radiolok/dekatronpc/TRS.md

---
title: DekatronPC — Требования v0.10
version: "0.10"
date: 2026-10-07
status: draft
supersedes: rtl/DekatronPC/DekatronPC_TRS_v0_7.md (с черновиком v0.8 golden model) и DekatronPC_TRS_v0_8.md
tags:
  - dekatronpc
  - requirements
  - rtl
  - hardware
  - checklist
---

# DekatronPC — Требования v0.10

## 0. Назначение документа

Документ задаёт функциональные и технические требования к проекту DekatronPC:

- ламповый компьютер на декатронах А110;
- RTL/FPGA-эмулятор (ядро `DekatronPC` + слой `Emulator`);
- модель одного декатрона `DekatronTubeV2` (физический уровень);
- испытательный стенд;
- ламповые модули;
- интерфейс к P&R-инструменту;
- верификацию и план работ.

Документ используется как:

- чек-лист «что готово / что осталось» (разделы 19, 21);
- источник требований для RTL, железа, тестов и P&R;
- основа для дальнейшего планирования (раздел 20).

**v0.9 заменяет v0.8.** Файл лежит в корне репозитория под именем `TRS.md` без номера версии: номер — в заголовке и в истории изменений ниже, прежние редакции — в истории git. Основа документа не переписана с нуля — сохранена структура и ID требований, статусы обновлены по результатам разбора двух функциональных отчётов по текущему RTL (`rtl-functional-report.md`, `emulator-functional-report.md`) и спецификации `DekatronTubeV2` (`Dekatron_Model_TRS_v0_1.md`). Новое помечается по версии, от **[v0.3]** до **[v0.9]**.

---

## 1. История изменений

### v0.10 — у декатрона нет признака достоверности

Признак `Valid` (ИЛИ-10 по главным катодам, лампа `OR10_X7`) удалён из `DekatronModule`, вместе с ним `out_valid` и `settled_q` в `DekatronCounter`. Признак говорил лишь «разряд на каком-то главном катоде», а не «операция закончена». Готовность теперь выводится из известных длительностей: шаг укладывается в один такт `clk`, запись и сброс — в окно реле времени `writeTimer`. Подъём `soft_rst`/`hard_rst` запускает то же окно (состояние `ST_RST`), и `ready` возвращается, только когда линия снята и окно истекло. Экономия — одна лампа ИЛИ-10 на каждую декаду.

`LOOP_DEKATRON_NUM = 2` внесён в `rtl/parameters.sv` (REQ-CNT-002 — Done): владелец подтвердил, что глубины вложенности 0–99 достаточно. Значение `TOP_VALUE` по умолчанию в `DekatronCounter` теперь следует за `D_NUM`, иначе двухдекадный счётчик давал WIDTHTRUNC. Схемы `img/schemes/` перерисованы генератором `tools/schemes/`.

Находка: при нарезке 3/4/3 и `FALL_STEP_HS = 3` разряд падал на главный катод ровно на следующем фронте `clk`, без запаса. Прежний `settled_q` это маскировал, фактически растягивая шаг на два такта. Нарезка по умолчанию изменена на **3/3/4** (`PHASE2_HS = 3`), а проверка окна сваливания стала строгой. `IpLine` на `looptest.bfk` — 656 мкс вместо 784. Отчёт: `doc/dekatron_valid_removal.md`.

Лишние триггеры `DekatronCounter` удалены по решению владельца: `primed_q` (автомат выходит из `rst_n` через `ST_RST`), `tops_q`, старшие разряды `nines_q`/`zeroes_q`. `zero` и `at_top` теперь комбинационно с катодов; защёлкнутые `zero_q`/`at_top_q` остались только при `TOP_LIMIT_MODE` для автоперехода через край. Флаги, маскированные `accept`, — без сброса. Переполнение вложенности (REQ-CNT-007) ловится до шага по `at_top`. По четырём счётчикам 49 → 24 триггера. Отчёт: `doc/dekatron_counter_flop_reduction.md`.

**Бюджет ламп и синтез.** Владелец задал бюджет: не более 1500 ламп на всю машину (REQ-MOD-009). Триггер в библиотеке теперь стоит 7 ламп (3×N16B + 4×J2B, 2 А накала при 6,3 В), инверсный выход у него бесплатный — в liberty добавлен вывод `QN` (REQ-MOD-010). `synt_dpc.tcl` переведён на отображение по площади (`&deepsyn` в ABC) с проверкой эквивалентности `equiv_opt` и проходом `qn_absorb.py`, который переносит инверторы с `Q` на `QN`: IpLine + ApLine + MachineCtrl — 2336,5 лампы против 2636 при прежнем скрипте; из них 910 — триггеры. Приём с терминала идёт по Valid/Ready, данные держит передающая сторона, входной регистр `rx_q` из ApLine удалён, у `DekatronPC` появился выход `rx_rdy` (REQ-UART-008, In Review; ApLine 989 → 874 лампы, три блока — 2242). Отчёт: `doc/tube_count_reduction.md`.

Автомат `ApLine` переписан (REQ-APV2-007): пары OP/WAIT слиты, 9 состояний → 6, стробы `valid` к счётчикам и памяти дешифруются из состояния и поднимаются только при готовности всех исполнителей, поэтому рукопожатие происходит в том же такте. Внешнее поведение не изменилось. ApLine 874 → 719 ламп, три блока — 2087. Отчёт: `doc/tube_count_reduction.md` §10.

Тем же способом переписан автомат `IpLine` (REQ-IPV2-007): пары OP/WAIT слиты, стробы дешифруются из состояния, `ip_dec` и `scan_dec_q` объединены в `dir_q`, `loop_init_q` и `clr_is_loop_q` убраны. Новый `IpLine_tb` с памятью по дисциплине `Ram` нашёл дефект прежнего автомата: инструкция защёлкивалась в такте приёма чтения по устаревшему `rd_valid`, и каждая выборка возвращала опкод предыдущей. Исправлено переписыванием. IpLine 902 → 722 лампы, три блока — 1948. Отчёт: `doc/tube_count_reduction.md` §11.

Третьим переписан `MachineCtrl` (REQ-CTLV2-010): 15 состояний → 10, все выходные стробы (`ip_valid`, `ap_valid`, `tx_vld`, `rx_rdy`, `*_rst_req`, `bell`) дешифруются из состояния, коды операций `ip_op`/`ap_op`/`ap_dec` — прямо из `insn`, который IpLine держит до следующей выборки. Убраны 16 триггеров, в том числе `echo_pending`, `bell_pending`, двухбитный `rst_type` и мёртвое состояние `S_BELL`; машина тратит на инструкцию на такт меньше. Новый `MachineCtrl_tb` (модели IpLine/ApLine/реле/терминала, все 32 опкода, TEST, CIN с эхом, загрузка, сбросы, переполнение, пошаговый режим) подтвердил дефект прежнего автомата из `doc/dpcrun_golden_model.md`: при переполнении вложенности ветка `S_FETCH_W` перебивала останов, машина декодировала скобку и шла дальше (REQ-CTLV2-005). Исправлено: переполнение приоритетнее любого состояния и ловится по фронту. MachineCtrl 512 → 284,5 лампы, триггеров 25 → 9, три блока — 1720,5. Отчёт: `doc/tube_count_reduction.md` §12.

CI `sim` падал: в образе Icarus 12, не знающий `break`/`continue`, которые появились в `IpLine_tb` и `MachineCtrl_tb`. Тестбенчи переписаны без них. Заодно найдены проверки, проходившие без проверки: `DekatronPC_tb.sv` не включал сценарий с программой (`TRY_PROGRAM`), терял символы TX на рукопожатии и завершал сторож через `$error` (код выхода 0); `DekatronPC_tb.cpp` не сравнивал ничего. Исправлено, пошаговое сравнение с golden model работает в CI (REQ-GM-002 — In Review). Отчёт: `doc/ci_sim_check.md`.

Появилась симуляция нетлиста (REQ-VER-025 — In Progress): `rtl/run/synth_sim.sh` синтезирует каждый DUT тем же `synt_dpc.tcl` с параметрами его тестбенча и гоняет те же Icarus-тесты на нетлисте. Модели ячеек `rtl/vtube/vtube_cells.v` приведены к liberty (имена, `NOR10_N16X7`, выход `QN`). Декатрон, `OneShot`/`Impulse`, `RstTimeRelay` и память под `SYNTH` пусты и остаются чёрными ящиками с RTL-моделью в симуляции. `OneShot`/`Impulse` — специальные ламповые схемы, а не логика из ячеек (решение владельца): в счёт ламп ABC они не входят, их надо учитывать в бюджете отдельно, как декатроны. Все тесты проходят, включая DekatronPC (helloworld, program.bfk). Две причины прежнего падения DekatronPC были не в ламповой логике: X из выходного регистра модели памяти (`RamGroup.digit_q` без начального значения; ABC-нетлист не маскирует X, как RTL) и всплеск нулевой длительности на `IsHalted`, который ловил асинхронный `wait` тестбенча. Отчёт: `doc/synth_sim.md`.

Вывод `.` переделан по решению владельца (OPEN-017 закрыт): символ всегда берётся со счётчика данных, мультиплексор `tx_data_bcd = lock ? data_out : rd_data` в ApLine удалён. `MachineCtrl` выдаёт `AP_COUT`, и только по его окончании — `tx_vld`. При снятом MemLock `AP_COUT` загружает ячейку в счётчик (из регистра памяти или после чтения), MemLock не меняется. Цена — одно окно записи на каждый `.`, при 110 бодах незаметно. Hello World через загрузчик теперь печатается верно. ApLine 714 → 679,5 лампы, три блока — 1672,5. Отчёт: `doc/tube_count_reduction.md` §13.

Инструкция декодируется один раз (R3) и хранится только в памяти (R4). Кодом операции ApLine теперь служит сама инструкция `{insn_mode, insn}`, её дешифрирует ApLine; порты `ap_op[3:0]`, `ap_dec` и шифратор в `MachineCtrl` убраны, у IpLine вместо `ip_op[1:0]` один бит `clr` (REQ-APV2-008). Регистр опкода `insn_q` в IpLine удалён: выходной регистр памяти программ меняется только при обращении, а следующее обращение бывает лишь после того, как `MachineCtrl` закончил с текущей инструкцией, поэтому `insn` — это прямо `mem_rd_data`. EOT в память не пишется, о нём сообщает однобитный `insn_eot` (решение владельца). При загрузке опкод пишется в память в такте рукопожатия, `insn_in_ready` поднимается при свободной памяти; состояния `S_FETCH_W` и `S_WRITE` убраны (REQ-IPV2-008). Интерфейс Emulator ↔ DekatronPC (Приложение B) не изменился. IpLine 717,5 → 652, MachineCtrl 282 → 250, ApLine 675,5 → 676 (оба варианта синтезированы в один день одним скриптом), три блока — 1578. Отчёт: `doc/tube_count_reduction.md` §14.

**Новая цель по лампам.** Владелец снизил бюджет всей машины с 1500 до **1200 ламп** (REQ-MOD-009). Три блока, которые сейчас считает синтез (IpLine + ApLine + MachineCtrl со счётчиками), занимают 1578 ламп — на 378 больше нового бюджета ещё до учёта обвязки памяти, реле сброса и пульта. Чистка автоматов исчерпана: оставшиеся идеи из `doc/tube_count_reduction.md` §5 (R5, R11) дают 10–30 ламп. Нужен новый подход (§22, п. 10).

**Реле для тумблеров** (REQ-MOD-011, In Review). Логика, которой управляют только панельные тумблеры, переведена на реле 2CO: ячейка `RELAY_2CO` (0 ламп), модули `RelayMux`/`RelayEn` (`rtl/Logic/Relay.sv`, не расплющиваются синтезом). В `MachineCtrl` — 5 реле (звонок ×3, выбор пуска после сброса ×2); эхо и `SoftRstOnEOT` оставлены на лампах, где реле ничего не экономит. Выигрыш по `MachineCtrl` — около 4,5 ламп в среднем по 7 зёрнам ABC (в пределах разброса одного прогона). Отчёт: `doc/tube_count_reduction.md` §15.

**Упреждающая выборка** (REQ-PERF-003, P3 из `doc/cycle_profile_helloworld.md`, решение владельца). Операция над ApLine не трогает ни IP, ни память программ, поэтому `MachineCtrl` в такте выдачи `ap_valid` выдаёт и `ip_valid`: следующая инструкция читается, пока исполняется текущая. Исключения — скобка (TEST: решение о промотке зависит от его результата) и CIN (ждёт терминал). Выход памяти программ при этом меняется до конца операции, поэтому код инструкции снова защёлкивается — в `MachineCtrl` (`op_q`, 4 триггера), а не в IpLine; ApLine получает `{insn_mode, op_q}` через порт `ap_op`. По окончании операции автомат идёт из `S_WAIT`/`S_COUT` прямо в `S_DECODE`. IP в это время стоит на следующей инструкции; при останове IpLine по входу `ip_ahead` его не сдвигает, а после пуска читает ту же инструкцию заново. helloworld: 5540 → 4184 такта, CPI 13,8 → 10,4; MachineCtrl 248 → 319 ламп. Интерфейс Emulator ↔ DekatronPC не изменился. Отчёт: `doc/prefetch_p3.md`.

**Pi пошагово.** `pi.bfk` прогнан на полном `DekatronPC` в Verilator с пошаговым сравнением (`DekatronPC_tb.cpp -s`, с упреждающей выборкой): 221 386 инструкций, 3,17 млн тактов, ни одного расхождения, вывод `3.141`. Независимый интерпретатор Brainfuck на Python даёт тот же вывод и сходится по счёту инструкций. Первый прогон остановился на 6-й инструкции (`<` из ячейки 0): RTL переходит на 99999, модель — на 29999. В `ApLine` счётчик AP собран без верхнего предела, а `Ram` данных — на 100 000 ячеек (владелец подтвердил, что RTL теперь работает со 100k), поэтому тестбенч собирает модель с `apTop = 99999` (ключ `-a` меняет предел). OPEN-001 не закрыт (REQ-CNT-005, REQ-MEM-DATA-005). Отчёт: `doc/pi_step_check.md`.

Появилась модель декатрона без тактовой базы (REQ-DEK-010 — In Progress): `DekatronTubeDelay` — та же кольцевая модель, но без входа `hsClk`, длительности отрабатываются инерционными задержками `#N` в абсолютном времени (`HS_NS = 100` нс на единицу `*_HS`). Положение разряда входит в запрос перемещения, поэтому два шага подряд в одну сторону не сливаются, а иголки нулевой длительности на подкатодах (нетлист) отфильтровываются. Подключается `` `define DEKATRON_DELAY_MODEL `` в `DekatronModule`, в `DPC.files` не входит (Verilator и Quartus её не видят). `DekatronPC_tb` теперь идёт на настоящих 10 МГц `hsClk` / 1 МГц `Clk` (было 5 МГц / 500 кГц). Все Icarus-тесты, pi.bfk на RTL и на нетлисте проходят; новые задания CI `sim_delay` и `synth_sim_delay`. Затем тем же define на задержки переведены `Impulse`, `OneShot`, `DekatronPhaseGen` и проверки `DekatronPulseSender` (новых модулей нет, логику выбирает `` `ifdef ``): `DekatronCounter` больше не использует `hs_clk`, тесты Counter/Dekatron идут с `hsClk` в нуле. У `OneShot` вход окна проходит инерционный фильтр 1 пс, чтобы иголки нулевой длительности не запускали окно. Затем так же переведено `RstTimeRelay`: весь DekatronPC работает без `hsClk`. Найдена гонка в `DekatronPC_tb`: кнопки пульта выставлялись блокирующим присваиванием сразу после `@(posedge Clk)`, и автомат видел их в том же такте или в следующем в зависимости от порядка событий (отсюда расхождение RTL и нетлиста на один такт). Кнопки и тумблеры теперь неблокирующие, обе модели и нетлист дают одинаковые числа тактов. Отчёт: `doc/dekatron_delay_model.md`.

**Один флаг MemLock** (REQ-APV2-003, решение владельца). Признак `dirty` удалён из `ApLine` и из `dpcrun`: он отличался от `lock` только после `STORE`. Правило теперь одно: без MemLock данные сначала загружаются, при MemLock шаг адреса и `CLRML` сначала выгружают счётчик, и выгрузка снимает MemLock. Попутно закрыт дефект v0.9 — MemLock больше не переживает шаг адреса после `STORE` (REQ-ML-005). Цена — повторная запись того же значения после `STORE`; на `pi.bfk` и `helloworld` счёт обращений не изменился. Отчёт: `doc/memlock_single_flag.md`.

**Требования к P&R по ревью webui** (2026-10-09, `doc/webui_review.md` на ветке `webui`, PR #28). Владелец ответил на Q1–Q11, решения внесены в §17 как REQ-PR-011…019. Нетлист остаётся иерархическим; блок P&R — это ящик из 3–5 корзин. Блок трассируется вместе с разъёмами HD-68 на другие блоки, а весь компьютер можно разводить в одном проекте. На плате корзины только питание, сигналы идут проводами. Ферритовая память — вне P&R. Для RTL добавлена задача: структуры из проводов по разъёмам блока (REQ-PR-019, §22).

### v0.9 — конфигурация счётчиков зафиксирована по реальным программам

Разрядность счётчиков до сих пор выбиралась по оценке. Теперь она проверена на наборе **Brainfuck-100**: сто программ с GitHub (классика, математика, текстовые утилиты, алгоритмы, интерпретаторы и компиляторы, квайны, игры, нагрузочные тесты), прогнанных в интерпретаторе с 8-битными ячейками. Для каждой сняты длина программы, занятая лента, число исполненных инструкций, число шагов промотки и **реальный максимум счётчика вложенности при промотке**.

**Зафиксирована конфигурация 5 + 2 + 5 + 3 = 15 декатронов.**

| Счётчик | Декатронов | Диапазон | Покрытие набора | Решение |
|---|---:|---|---|---|
| IP | 5 | 0–99999 | 99 из 100 (при 4 — 88, при 3 — 61) | оставлен |
| Loop | **2** | **0–99** | 100 из 100, максимум 67 | **сокращён с 3** |
| AP | 5 | 0–29999 / 0–99999 | 98 / 100 | предел остаётся открытым (OPEN-001) |
| Data | 3 | 0–255 | 100 из 100 | оставлен |

**Почему хватает двух декатронов вложенности.** Счётчик считает вложенность от скобки, с которой началась промотка, а не от начала программы. Статическая глубина в тексте завышает потребность: у `password-vault.bf` она 124, а при исполнении счётчик доходит до 52; у `Kiloseconds.b` — 90 против 67. Из 273 просмотренных программ не помещается только `OptimTease.b` — тест на прочность оптимизаторов с вложенностью 258. Переполнение по-прежнему безопасно: инкремент со 99 не выдаётся, промотка прерывается и машина останавливается (REQ-CNT-007). Экономия — одна декада без схемы чтения (`LOOP_READ = 0`), около 10 ламп.

**Попутная находка — цена промотки.** На одну исполненную инструкцию в среднем приходится 1,7 шага промотки IP; у `pi.bfk` 313 968 шагов промотки против 198 594 инструкций. Время выборки во время промотки влияет на быстродействие машины не меньше, чем время исполнения. Внесено как REQ-PERF-001.

Новый раздел 4.4 фиксирует текущие ограничения архитектуры и десять программ, которые их определяют.

**Сведение с веткой `claude_nextGen` (04.10.2026).** Существовали две параллельные редакции v0.8: в репозитории — черновик про golden model, вне репозитория — синтезируемость памяти и ассерты. Обе вошли в v0.8 ниже. Состояние RTL ветки на момент сведения:

- `LOOP_DEKATRON_NUM` в `rtl/parameters.sv` пока равен 3: решение REQ-CNT-002 принято, в коде не внесено.
- Ширины счётчиков задаются глобально в `rtl/parameters.sv`, а не параметрами `IpLine`/`ApLine`.
- Признак достоверности декатрона при синтезе (`SYNTH`) — явный экземпляр лампы ИЛИ-10 `OR10_X7` из `rtl/vtube/vtube_cells.lib`: abc не собирает такой широкий элемент из reduction-OR. В моделировании — `|MainOneHot`. Модуль `OneHotValid` из дерева удалён; запись — снова `BcdToBinEn`.
- При синтезе Yosys банковое дерево `Ram` заменяется заглушкой с тем же интерфейсом: рекурсивный `RamGroup` зацикливает `hierarchy -check`. Число ламп по синтезу (≈ 2600) — без памяти.
- В ветку не внесены две подготовленные правки: сброс `lock` в `ApLine` при шаге адреса без выгрузки (после STORE) и вывод через `AP_COUT` в `MachineCtrl` (OPEN-017).
- Операнды не защёлкиваются ни в `DekatronCounter`, ни в `ApLine`: мастер держит их до `ready`.

---

### v0.8 — синтезируемость памяти, параметр размера банка, управление ассертами

Версия написана по итогам первых прогонов в симуляторе и попытки синтеза. Все изменения — следствия того, что показали инструменты, а не пересмотр замысла.

**Память перестала быть несинтезируемой.**

Попытка синтеза подтвердила опасение, зафиксированное в `OPEN-015`, но причин оказалось две, а не одна.

Первая — дробление. Банк 10×10 при ширине четыре бита занимает 400 бит, а блок памяти ПЛИС вмещает 10 240: пропадает 96% каждого блока. На две памяти требовалось около 1300 блоков там, где по объёму достаточно 80.

Вторая, не менее важная и не замеченная ранее, — **асинхронное чтение в банке**. Блоки памяти ПЛИС умеют только синхронное чтение; при асинхронном массив раскладывается в триггеры, а это 700 000 штук при бюджете порядка 40 000 логических элементов. Одно увеличение банка проблему бы не решило.

Исправлено обоими способами сразу:

| | Банков | Блоков памяти |
|---|---:|---:|
| Программ 100k×4, банк 10×10 | 1000 | 1000 |
| Программ 100k×4, банк 100×100 | 10 | 50 |
| Данных 30k×10, банк 10×10 | 300 | 300 |
| Данных 30k×10, банк 100×100 | **3** | **30** |

**Размер банка стал параметром, а не выбором.** `BANK_DIGITS` = 2 даёт матрицу 10×10 для физической машины и P&R, 4 — матрицу 100×100 для ПЛИС. Рекурсия та же, меняется лишь уровень её остановки. Вторая, плоская реализация памяти, которую требовал `REQ-MEMV2-006`, оказалась не нужна: одна и та же память служит обеим целям. Требование снято, `OPEN-015` закрыт.

**Третье, найденное попутно:** без ограничения по реально используемому объёму память данных разворачивалась на все 100 000 ячеек адресного пространства при используемых 30 000. Введён параметр `CELLS`, банки выше границы не создаются.

**Цена.** Синхронное чтение добавляет такт: обращение занимает два такта вместо одного. На программе вычисления Pi это около 99 тысяч дополнительных тактов. Избежать нельзя — асинхронной памяти нужного объёма в ПЛИС нет.

**Внутри банка появилась адресная арифметика** — тетрады сводятся в линейный индекс. Это не возврат к тому, от чего избавлялись: пересчёт не выходит за пределы одного банка и существует только в поведенческой модели и реализации для ПЛИС. В железе тетрады идут прямо на дешифраторы строк и столбцов матрицы.

**Golden model на полный ISA** (черновик v0.8 из репозитория). C++ golden model (`bfutils/dpcrun`) переписана: оба ISA, MemLock с ленивым чтением, SOT/EOT, сбросы, переполнение счётчика циклов, ПЗУ загрузчика. По решению владельца проекта модель повторяет RTL как есть, в том числе там, где RTL расходится с TRS (CLRI и MemLock, снятие MemLock после STORE). 53 модульных теста в CI репозитория bfutils. Сверка вскрыла дефект: `.` не выдаёт `AP_COUT`, поэтому OPEN-017 открыт снова. Подробности и остальные находки — `doc/dpcrun_golden_model.md`.

**Управление ассертами переведено на условную компиляцию.**

Параметр `EN_ASSERTIONS` заменён на `` `ifdef ASSERTIONS ``. Параметр требовал протаскивания через всю иерархию инстанцирований и молча оставался включённым там, где его забыли передать. Проверки конфигурации на этапе элаборации (`initial` с контролем параметров) остаются под `` `ifndef SYNTH ``: их следует получать при каждой сборке, а не только при включённых ассертах.

---

### v0.7 — ленивое чтение, отказ от APB, регистровый выход памяти

Три связанных решения, принятых по итогам измерений на реальных программах.

**Ленивое чтение вместо упреждающего.**

В v0.6 `ApLine` читал ячейку сразу после каждой смены адреса. Замер показал, что это дорого: перемещения указателя составляют половину инструкций типичной программы, а каждое из них вызывало обращение к памяти, даже когда следующая инструкция — снова перемещение.

Теперь ячейка читается только тогда, когда её значение действительно нужно. Замер на программе вычисления числа Pi (`pi.bfk`, 198 594 инструкции, `<` и `>` — 51% кода):

| Схема | Обращений к памяти | Изменение |
|---|---:|---|
| Упреждающее чтение | 155 625 | — |
| Ленивое чтение | 99 077 | **−36%** |

На последовательности `>>>>>...<<<<<` разница сорокакратная: одно обращение против сорока одного. Закрывает `OPEN-016` с цифрами.

**Регистровый выход памяти вместо копии ячейки в ApLine.**

Первая редакция ленивого чтения требовала в `ApLine` собственную копию ячейки — десять триггеров, а лампового триггера дороже элемента в библиотеке нет. Оказалось, что регистр не нужно добавлять: он и так существует физически. У ферритовой памяти чтение разрушающее, считанное значение оседает в усилителях считывания и держится там на время восстановительной записи.

Поэтому регистр перенесён в память: `rd_data` хранит значение последней затронутой ячейки до следующего обращения, запись сквозная. В `ApLine` состояния осталось три бита — `lock`, `dirty`, `mem_here`. Показатели при этом соответствуют варианту с полной копией, а не урезанному.

**Отказ от APB.**

APB был выбран в v0.6 и оказался неподходящим по двум причинам. Во-первых, он гарантирует валидность данных только в такте `PREADY`, а требуется обратное — чтобы значение держалось до следующего чтения; полагаться на негарантированное поведение нельзя. Во-вторых, две обязательные фазы дают минимум два такта на обращение там, где достаточно одного.

Память переведена на тот же Valid/Ready, что и остальной тракт. Заодно исчез разнобой протоколов: раньше `ApLine` и `IpLine` были мастерами двух разных дисциплин сразу.

Наложение ПЗУ загрузчика перестало быть отдельным мультиплексором: `Ram` получил входы `ovl_hit`/`ovl_data`, поэтому автомат обращений и выходной регистр остались в единственном экземпляре.

**Цена решения.**

Проверка скобки перестала быть бесплатной: признак нуля при ленивом чтении не всегда под рукой, и перед `[` или `]` верхний автомат просит `ApLine` обеспечить его достоверность операцией `TEST`. Обращение к памяти при этом происходит, только если значение не прочитано, а во время самой промотки тела цикла проверка не повторяется. В Debug ISA скобки проверяют счётчик адреса, достоверный всегда, поэтому там `TEST` не выдаётся.

**Найденный дефект: комбинационная петля в `DekatronCounter`.** Обнаружен прогоном в симуляторе. Сигнал `ready` содержал условие `~writing`, а окно записи запускается от `accept`, который сам зависит от `ready`:

```
ready -> accept -> write_req -> Impulse -> OneShot -> writing -> ready
```

Петля замыкалась при любой операции записи, включая автопереходы через верхний предел. Icarus зацикливался на одном такте, Verilator выдавал `UNOPTFLAT`, синтез был бы некорректен. Следствие: `set`, `set_zero` и переходы `255+1`/`0−1` были неработоспособны, при том что инкремент, декремент и оба сброса работали.

Условие оказалось избыточным: автомат покидает `ST_IDLE` при приёме операции записи и возвращается только по окончании окна, поэтому состояние уже несёт нужную информацию. Петля разорвана удалением `~writing`.

**Второе замечание симулятора: UNOPTFLAT на цепочке переноса.** Поразрядная запись рипла

```systemverilog
assign step_f_chain[d] = step_f_chain[d-1] & nines_q[d-1];
```

заставляет Verilator видеть зависимость вектора от самого себя: анализ ведётся с точностью до целого сигнала, а не отдельных битов. Физически петли нет — перенос идёт строго от младшей декады к старшей.

Устранено структурно: рипл вынесен в локальные переменные внутри `always_comb`, а векторы `step_*_chain` только записываются и нигде не читаются. Подавление предупреждения не выбрано намеренно: оно скрыло бы и настоящие петли, если они появятся в этом же файле. Эквивалентность старой и новой цепочки проверена на 8000 случайных векторов.

**Этот дефект принципиально не мог быть найден на модели.** Такт-в-такт копия на Python вычисляет сигналы в порядке присваивания и нуль-задержечную петлю не видит вовсе: у неё нет понятия сходимости комбинационной логики. Это ровно тот класс ошибок, ради которого в документе стоит `REQ-VER-029`, и первое подтверждение, что «проверено на модели» и «проверено в симуляторе» — разные вещи.

**Найденный дефект.** `MachineCtrl` не видел сброса, пришедшего с пульта: реагировал только на сброс, запрошенный им самим по инструкции HRST или SRST. Реле срабатывало, счётчики сбрасывались, а автомат продолжал исполнять инструкцию и не менял набор команд — после аппаратного сброса машина осталась бы в Brainfuck ISA вместо Debug, и загрузчик бы не стартовал. Добавлены входы `soft_rst`/`hard_rst`, реакция общая для обоих источников.

---

### v0.6 — Шаг 1в выполнен: весь тракт переведён на Valid/Ready

Переписаны память, обе линии и верхний автомат. Фаза 1 плана работ закрыта полностью.

**Память переведена на банковую организацию и APB.** *(решение об APB отменено в v0.7, банковая организация сохранена)*

Единый массив с преобразованием BCD-адреса в двоичный заменён иерархией: банк 10×10 (2 декатрона) → группа из 10 банков (3 декатрона) → и так далее до пяти. Адресной арифметики нет вовсе — тетрада напрямую выбирает потомка сравнением. Это закрывает `REQ-MEM-IP-003/004`, `REQ-MEM-DATA-003/004` и снимает `REQ-REF-010`: умножители на 10/100/1000/10000 не появляются, потому что линейный индекс не вычисляется.

Ширина ячейки данных зафиксирована: **10 бит `{hundreds[1:0], tens[3:0], ones[3:0]}`** — закрывает расхождение `REQ-MEM-DATA-002`.

Загрузчик в памяти программ занимает ровно один банк 10×10 (100 инструкций по адресам 99900–99999). Прежний мультиплексор по `isBootloader` не нужен.

**ApLine: предвыборка текущей ячейки.** *(заменена ленивым чтением в v0.7)*

Прежний код считал `DataZero` как `~(|RamDataOut)` и выдавал `tx_data_bcd` прямо с выхода памяти — это работало только потому, что память моделировалась асинхронной. Ферритовая память так не умеет: чтение разрушающее, а по APB `rd_data` валиден лишь в такте `p_ready`. Поэтому `ApLine` держит копию текущей ячейки и обновляет её после каждой смены адреса. Побочный выигрыш: `LOAD`, `COUT`, `[`, `]` вообще не обращаются к памяти.

Замерено на модели: серия `+++++` после первой загрузки не трогает память ни разу, а `+++>+++` даёт ровно три обращения (предвыборка, выгрузка, предвыборка) — то, чего добивался §7.5.

**IpLine: промотка циклов целиком внутри блока.**

Прежде решение о перемотке принимал декодер и повторно поднимал `IpRequest`, а шаг IP выдавался из трёх мест. Теперь `IpLine` получает признак `loop_val_zero` и мотает сам; разбор скобки вынесен в отдельное состояние. Подключены `CLRI` и `CLRL`.

**MachineCtrl: логика циклов из декодера удалена.**

Декодер сводится к таблице диспетчеризации по паре `{insn_mode, insn}`. Сверено построчно с §6: все 32 комбинации покрыты. Подключены отсутствовавшие ранее `BELL`, `CLRL`, `CLRI`, `HRST`, `SRST`, `CLRD`, `CLRML`, `LOAD`, `STORE`.

Асинхронные входы `Rst_n`/`HardRst_n` из тракта убраны: сброс декатронов — физический импульс по катоду, длительность держит внешнее реле времени. Машина выдаёт запрос и ждёт снятия `rst_busy`.

**Найденные и устранённые дефекты:**

- **`CLRD` обязан выставлять `MemLock`.** Допущение v0.5 («не трогает, по аналогии с LOAD/STORE») проверено и оказалось неверным: при нём `[-]` не обнуляет ячейку — ноль ложится в счётчик, счётчик считается устаревшим, и при смене адреса из памяти возвращается прежнее значение. Закрывает `OPEN-002` против прежнего допущения.
- **Зависание при переполнении вложенности.** Счётчик циклов перескакивал 999→0, флаг ошибки поднимался, но промотка продолжалась: парная скобка уже не найдётся, IP уходит за пределы памяти, машина висит. Теперь промотка прерывается, машина останавливается.
- **Дублирующийся `InsnLoopDetector`** в `IpLine` — два инстанса, подключённые к одному и тому же регистру.
- **Запись в область загрузчика** прежде уходила в RAM, а читался всегда ROM: ячейка становилась недостижимой. Теперь блокируется и поднимает `p_slverr`.

**Замечание о методе проверки.** Первая модель `IpLine` работала с символами вместо опкодов и потому не отражала интерфейс RTL — именно она скрывала зависание при переполнении. После переписывания модели на опкоды дефект проявился сразу. Модели, не совпадающие с интерфейсом проверяемого блока, дают ложную уверенность.

---

### v0.5 — реализована подсистема декатрона, Шаги 1а и 1б Фазы 1 закрыты

Написан и проверен RTL нижних уровней. Шаги 1а и 1б плана работ выполнены, Шаг 1в (распространение Valid/Ready на `IpLine`/`ApLine`) остаётся открытым.

**Модель декатрона переработана на кольцевой регистр — отказ от FSM-модели TRS v0.1.**

Вместо FSM из четырёх состояний состояние прибора описывается 30-битным регистром в кольцевом режиме: ровно один установленный бит — текущее положение разряда, перемещение — циклический сдвиг. Соседние электроды вычислять не требуется, они соседние по построению. Кодировка: индекс `% 3 == 0` — главный катод (цифра = индекс/3), `% 3 == 1` — первый подкатод, `% 3 == 2` — второй.

Ключевое физическое уточнение, давшее эту переработку: **на подкатоде разряд остаться не может** — при снятии сигнала он сваливается на соседний главный катод (с первого подкатода назад, со второго вперёд). Отсюда напрямую следуют все случаи, которые в FSM-модели описывались отдельными таймерами:

- только первая фаза и снятие → возврат на исходный катод;
- вторая фаза пришла поздно → разряд уже свалился, шага нет;
- частичного инкремента не существует в принципе.

**Поэтому параметры `PHASE_WINDOW_HS` и `RETURN_TIMEOUT_HS` из TRS v0.1 упразднены** — их роль выполняет `FALL_STEP_HS`. Регистры `prev_digit_q`, `target_digit_q` и явная FSM из модели декатрона исчезли полностью.

**Формирователь импульсов: нарезка такта на трети.**

Первая версия делила такт на полуволны (первая фаза — положительная, вторая — отрицательная). Проверка на модели показала, что так счёт не идёт вовсе: к концу такта разряд остаётся на втором подкатоде, а первая фаза следующего такта утаскивает его обратно — разряд бесконечно колеблется между подкатодами и ни разу не попадает на главный катод. Потребовалась бы пауза длиной в целый такт, то есть счёт через такт (500 кГц).

Такт разделён на три части: первый подкатод, второй подкатод, пауза на сваливание. Пауза внутри такта даёт **счёт каждый такт — 1 МГц вместо 500 кГц**. Времязадающая часть вынесена в `DekatronPhaseGen` и моделирует RC-цепи реальной схемы; сам `DekatronPulseSender` стал чистой комбинаторикой (4 И, 2 ИЛИ).

**Найдены и устранены дефекты, которых не было видно в спецификации:**

- Операции записи/сброса «встык», без снятия воздействия между ними (например, импульс сброса в 0 сразу после сброса в 9), не срабатывали: признак завершения сбрасывался только при снятии всех воздействий. Физически импульс на другом катоде — это новая операция. Добавлено отслеживание цели: смена цели без снятия воздействия перезапускает отсчёт.
- Сочетание `GUIDE_STEP_HS=3, FALL_STEP_HS=4` при нарезке 3/4/3 срывает счёт наглухо: окно сваливания не вмещает падение, показание никогда не становится достоверным. Добавлены проверки согласованности таймингов на этапе компиляции.

**Сбросы стали физическими линиями счётчика.**

Промежуточно рассматривался вариант «аппаратный сброс как операция по handshake», но принято другое решение: `soft_rst` и `hard_rst` — прямые линии на уровне счётчика, который разводит их по катодным линиям декад, поскольку только он знает целевые позиции. Длительность обеспечивает **внешнее физическое реле времени**; растяжки внутри счётчика нет — это была бы лишняя логика поверх уже существующей физической цепи.

**Появился сигнал достоверности показания.**

Пока разряд идёт по подкатодам, ни один главный катод не светится и позиционный код нулевой — что неотличимо от настоящего нуля. Прежде это маскировалось выдачей `X` (`OutPos = ... ? 10'bx : _OutPos`), что работало только в симуляции. Теперь есть `Valid` — физически ИЛИ по десяти линиям чтения, реализуемо в железе.

**Подтверждено на модели:** 12 инкрементов подряд без снятия `ready` (одна операция за такт), перенос через все декады, оба режима верхнего предела (255+1→0 и 0−1→255), `hard_rst` → 99900 на пяти декадах.

---

### v0.4 — принципиальное уточнение физики декатрона и порядка работ

Зафиксировано explicit-решение по OPEN-008 (было открыто в v0.3): **последовательная миграция, а не параллельное ведение моделей.** Порядок: сначала `DekatronTubeV2` (физическая модель, полностью без handshake) реализуется и покрывается полным набором тестов из TRS v0.1 — только после этого RTL верхних уровней (`DekatronCounterV2` и выше) переписывается вокруг неё под Valid/Ready. Это меняет структуру Фазы 1 плана работ (раздел 20) — переход на Valid/Ready для `IpLine`/`ApLine` технически не может начаться раньше, чем готова физическая модель декатрона, поскольку именно `DekatronCounterV2` — первый уровень, где handshake вообще физически осмыслен.

Подтверждён и явно закреплён как принцип (не просто ссылкой на TRS v0.1) физический контракт декатрона:

- декатрон не реализует и не может реализовать `valid`/`ready`/`busy` — это физически бессмысленно для газоразрядного прибора;
- стабильное состояние — разряд между анодом и одним из главных катодов без внешних воздействий, не более и не менее того;
- метастабильное состояние (разряд на подкатоде) наблюдаемо только косвенно и годится для assertions в симуляции, но **не существует как физически снимаемый чистый сигнал** — в реальной машине это не будет отдельным проводом с уровнем;
- декатрон реагирует на внешние воздействия заданной длительности **независимо от своего текущего внутреннего состояния**: короткий первый подкатодный импульс может быть не отработан; корректный первый импульс без последующего второго вызывает возврат на исходный катод — это не ошибка декатрона, а его нормальная физика, и вышестоящий блок обязан её учитывать, а не рассчитывать на handshake от самого декатрона;
- гарантируется: инкремент/декремент — не дольше 1 такта 1 МГц; запись — не дольше 10 тактов 1 МГц. Вся дисциплина (handshake, повторные попытки, обработка коротких/отсутствующих импульсов) — ответственность `DekatronCounterV2`, а не декатрона.

**Обнаруженный серьёзный пробел [v0.4]:** в текущем RTL-блоке декатрона (`Dekatron.sv`/`DekatronModule.sv`) **временные характеристики отсутствуют полностью** — нет ни квалификации длительности подкатодных импульсов, ни таймаутов второй фазы, ни минимальной длительности записи как явных, тестируемых параметров (см. также REQ-RTL-015 о маскировании в `X` — это не замена таймингам, а побочный эффект отсутствия явной FSM). Это признано отдельным критическим недостатком, а не второстепенным техдолгом — без временных характеристик модель декатрона функционально неполна независимо от прогресса по handshake наверху.

---

### v0.3 — основные изменения относительно v0.2

**Решения, принятые в этой сессии:**

- **REQ-ARCH-007/008 (handshake):** выбран путь — **полный переход на Valid/Ready-подобный протокол** между блоками (`IpLine`, `ApLine`, `DekatronCounter`, память), а не точечные фиксы. Это поднимает приоритет рефакторинга и меняет объём Фазы 1 плана работ (раздел 20).
- **REQ-CNT-005 / OPEN-001 (AP limit 29999 vs 99999):** остаётся параметром RTL. Явно зафиксирован критерий: `99999` экономит ~20 ламп на декатронах адреса, но требует больше памяти (100k×10 бит вместо 30k×10 бит) и лишний перенос разряда. **Финальный выбор откладывается до момента непосредственно перед фиксацией RTL** — статус остаётся In Review, но с зафиксированными критериями оценки.
- **REQ-REF-003 (`DekatronPulseAllow`):** решение — **удалить как рудимент** (модуль пуст, логика управления переносом уже реализована через `Nines`/`Zeroes` + `RsLatch` в `DekatronCarrySignal`). Требование переведено из TODO в конкретную задачу удаления с проверкой, что каскад переноса в `DekatronCounter` не зависит от этого модуля.

**Рабочие предположения, требующие отдельного подтверждения** (заданы, но ответ не получен явно — помечены как допущение, не как решение):

- **REQ-ML-009 / OPEN-002 (`CLRD` vs `MemLock`):** рабочее допущение — **`CLRD` не трогает `MemLock`**, по аналогии с `LOAD`/`STORE` (симметрия с REQ-ISA-BF-002). Статус: In Review, помечено как допущение в разделе 18.
- **OPEN-003 (`SOT` и переключение ISA):** рабочее допущение — **оставить поведение как в текущем RTL** (см. `1786044911450-emulator-functional-report.md`, `SoftRstOnEOT`), задокументировать как есть. Статус: In Review, требуется явное подтверждение перед фиксацией.

**Находки по функциональным отчётам RTL/Emulator [v0.3]:**

- Подтверждено расхождение между исходным PDF-описанием (`DekatronPC.pdf`, IP = 6 декатронов, 0–999999) и фактической реализацией (RTL: IP = 5 декатронов, 0–99999, bootloader на `99900–99999`). **v0.2/v0.3 архитектура (5 декатронов) считается действующей**, PDF в этой части устарел.
- В `1786044911450-rtl-functional-report.md` формулировка «5 декатронов IP = 20 бит адреса (1M адресуемых ячеек)» — **опечатка/несогласованность в отчёте**: 5 BCD-декатронов дают 100 000 адресуемых ячеек, а не 1M. Зафиксировано как замечание к отчёту, архитектурное решение (100 000) не меняется.
- Интерфейс `Emulator ↔ DekatronPC` де-факто зафиксирован в отчёте (полный список сигналов из инстанцирования в `Emulator.sv:258`). Это закрывает REQ-EMU-002 — статус переведён в Done с фиксацией сигнатуры (Приложение B).
- Обнаружены конкретные технические долги в RTL, ранее описанные общими словами в REQ-REF-*: `RsLatch` не специфицирован при `S=R=1` (использует `always_latch`, потенциальная гонка), `DekatronModule` маскирует выход в `X` через `OutPos = ... ? 10'bx : _OutPos` (осознанный приём, но требует явной формулировки в требованиях к синтезируемости), `Dekatron.sv` дублирует логику для `EN_HARD_RST=0/1` вместо параметризации веткой без дублирования.
- Зафиксирован разрыв между целевой моделью декатрона `DekatronTubeV2` (TRS v0.1: чистый интерфейс `guide_a_i/guide_b_i/write_en_i/write_pos_i/reset0_i/reset9_i`, FSM из 4 состояний) и фактически используемой в RTL моделью (`Dekatron.sv`: `Pulses[1:0]`, `In_n[9:0]`, `HardRst_n`, дублирование по `EN_HARD_RST`). **`DekatronTubeV2` в код ещё не интегрирована** — это отдельная задача миграции (см. Приложение C, новый раздел 11.4).
- Добавлено новое приложение A — таблица сопоставления находок аудита RTL с конкретными файлами/модулями (для трассируемости).

---

## 2. Статусы

| Статус | Значение |
|---|---|
| TODO | Требование/работа ещё не выполнена |
| In Progress | Работа ведётся |
| In Review | Требование требует анализа, оценки или уточнения |
| Assumption **[v0.3]** | Рабочее допущение принято, но не подтверждено явно — использовать с осторожностью |
| Done | Требование принято или уже реализовано |
| Rejected | Отклонено / не требуется в целевой системе |

---

# 3. Область применения и аутентичность

## 3.1. Область применения

| ID | Требование | Статус | Комментарий |
|---|---|---:|---|
| REQ-SCOPE-001 | Проект охватывает: RTL/FPGA-эмулятор, реальную ламповую машину, испытательный стенд, ламповые модули, требования к P&R-инструменту. | Done | Принято. |
| REQ-SCOPE-002 | FPGA-эмулятор рассматривается как временное устройство для подмены ещё не собранных ламповых блоков. | Done | Обязательное требование. |
| REQ-SCOPE-003 | Приоритеты: RTL → стенд → ламповые модули → измерения/liberty. | Done | Принято. |
| REQ-SCOPE-004 | P&R-инструмент разрабатывается отдельно, но получает из этого документа требования по нетлисту, liberty, модулям и разъёмам. | Done | Принято. |
| REQ-SCOPE-005 **[v0.3]** | Модель `DekatronTubeV2` (TRS v0.1) входит в область документа как целевая физическая модель декатрона, отдельная от текущей рабочей RTL-модели `Dekatron.sv`. | Done | См. раздел 11.4 и Приложение C. |

## 3.2. Аутентичность

| ID | Требование | Статус | Комментарий |
|---|---|---:|---|
| REQ-AUTH-001 | В вычислительном тракте реальной машины запрещены кремниевые полупроводниковые элементы. | Done | Обязательное. |
| REQ-AUTH-002 **[v0.10]** | Допускаются германиевые диоды только в выпрямителях (цепях питания) и в обвязке ферритовой памяти. ~~BCD/HEX-шифраторы/дешифраторы~~ **[v0.10]** строятся на лампах. | Done | Обязательное. **[v0.10]** Владелец (2026-10-08): диодные кодеки недопустимы, идея T2 из `doc/tube_count_reduction.md` §17 отклонена. |
| REQ-AUTH-003 | FPGA-эмулятор допустим только как временное средство разработки и подмены несобранных блоков. | Done | Обязательное. |
| REQ-AUTH-004 | Внешние загрузчики, терминалы, UART-адаптеры могут быть внешними устройствами и не обязаны быть ламповыми. | Done | Граница системы. |

---

# 4. Целевая архитектура машины

## 4.1. Общая архитектура

| ID | Требование | Статус | Комментарий |
|---|---|---:|---|
| REQ-ARCH-001 | Машина строится на четырёх реверсивных BCD-счётчиках: IP, Loop, AP, Data. | Done | Базовая архитектура. |
| REQ-ARCH-002 | Архитектура гарвардская: раздельная память инструкций и данных. | Done | Принято. |
| REQ-ARCH-003 | Все внутренние счётчики работают в BCD. | Done | Двоичная адресация допускается только как реализационный приём в FPGA (`BcdToBinEnc`). |
| REQ-ARCH-004 | Основной набор исполняемых инструкций должен точно соответствовать Brainfuck. | Done | Обязательное требование проекта. |
| REQ-ARCH-005 | Машина должна исполнять программы, помещающиеся в 30 000 ячеек данных, без предварительной компиляции. | Done | Brainfuck-совместимость. |
| REQ-ARCH-006 | Ожидается, что 99% существующих 8-битных Brainfuck-программ должны исполняться при условии размещения в памяти. | Done | Исходная цель проекта. |
| REQ-ARCH-007 | Handshake между блоками должен быть надёжным: потеря запроса недопустима. | Done **[v0.6]** | Весь тракт переведён на Valid/Ready. |
| REQ-ARCH-008 | Текущий импульсный Request/Ready заменяется на надёжный Valid/Ready-протокол. | In Progress **[v0.3/v0.4]** | Приоритет Фазы 1 плана работ (раздел 20). Затрагивает `IpLine`, `ApLine`, `DekatronCounter`, `InsnDecoder`, `IpMemory`, `RAM`. **[v0.4]** Технически не может начинаться выше уровня `DekatronCounterV2` — сам декатрон handshake не реализует (физически не может), см. REQ-DEK-012. Порядок работ зафиксирован: `DekatronTubeV2` → `DekatronCounter` → память → `IpLine`/`ApLine` → `MachineCtrl`. **[v0.6]** Выполнено полностью. |
| REQ-ARCH-010 **[v0.9]** | Конфигурация счётчиков зафиксирована: IP — 5, Loop — 2, AP — 5, Data — 3 декатрона, всего 15. | Done | Обоснование — набор Brainfuck-100, раздел 4.4. Открытым остаётся только предел AP (REQ-CNT-005). |
| REQ-ARCH-011 **[v0.9]** | Изменение разрядности любого счётчика проверяется на наборе Brainfuck-100 по таблице раздела 4.4. | Done | Набор и метрики — `bfutils/programs/bf100/` (README, `metrics.json`). |
| REQ-ARCH-009 **[v0.3]** | Расхождение с исходным PDF (IP=6 декатронов, 0–999999) закрыто: действующая архитектура — IP=5 декатронов, 0–99999, bootloader `99900–99999`. | Done | PDF в этой части считается устаревшим. |

## 4.2. Счётчики

| ID | Требование | Статус | Комментарий |
|---|---|---:|---|
| REQ-CNT-001 | IP Counter: 5 декатронов, диапазон `0–99999`. | Done | 100 000 инструкций. Подтверждено RTL (`parameters.sv`). |
| REQ-CNT-002 | Loop Counter: **2 декатрона, диапазон `0–99`**. | Done **[v0.10]** | Решение принято: сокращён с 3 декатронов по набору Brainfuck-100, реальный максимум при промотке — 67 (`Kiloseconds.b`), все 100 программ помещаются. В RTL внесено: `LOOP_DEKATRON_NUM = 2` (`rtl/parameters.sv`) **[v0.10]**. См. раздел 4.4. |
| REQ-CNT-003 | AP Counter: физически 5 декатронов. | Done | Обязательно для BCD-адресации. |
| REQ-CNT-004 | AP Counter: целевой Brainfuck-режим `0–29999`. | Done | Минимально необходимая совместимость. |
| REQ-CNT-005 | AP Counter: выбор `29999` vs `99999` остаётся параметром до момента фиксации RTL. | In Review **[v0.3]** | Критерий зафиксирован: `99999` = −20 ламп на декатронах адреса, но +память (100k×10bit против 30k×10bit) и лишний перенос разряда. Решение — непосредственно перед RTL freeze. **[v0.9]** Данные набора Brainfuck-100: при `29999` помещаются 98 программ из 100, при `99999` — все 100 (выигрывают компилятор `awib` на длинном входе — 30 647 ячеек — и бесконечный генератор случайных чисел). |
| REQ-CNT-006 | Data Counter: 3 декатрона, рабочий диапазон `0–255`. | Done | Brainfuck-совместимость. |
| REQ-CNT-007 | Переполнение Loop Counter выше `99` **[v0.9]** должно вызывать аппаратную ошибку и прерывать промотку. | Done **[v0.6]** | ~~Детектируется обнулением счётчика при инкременте.~~ **[v0.10]** Детектируется ДО шага: `at_top` счётчика (все декады на 9, комбинационно с катодов) и инкремент своей скобкой; шаг не выдаётся, счётчик остаётся на 99 до CLRL или сброса. **Обязательно прерывать промотку:** парная скобка уже не найдётся, и без прерывания машина зависает в бесконечном переборе адресов — дефект найден тестированием. `IpLine` выходит из промотки, `MachineCtrl` останавливает машину. |
| REQ-CNT-008 | В симуляции обязателен контроль невалидных BCD-состояний. | TODO | Для RTL/верификации. |
| REQ-CNT-009 | В реальной машине детектор невалидного BCD не реализуется, если он требует лишних ламп. | Done | Принято. |

## 4.3. Представление данных

| ID | Требование | Статус | Комментарий |
|---|---|---:|---|
| REQ-DATA-001 | Декатронные счётчики выдают BCD шириной `число декатронов × 4`. | Done | Принято. |
| REQ-DATA-002 | Data Counter выдаёт 12 бит BCD. | Done | 3 декатрона × 4 бита. Подтверждено (`tx_data_bcd[11:0]`, `rx_data_bcd[11:0]`). |
| REQ-DATA-003 | В Data RAM и далее на дешифраторы/шифраторы подаются только младшие 10 бит из 12-битного BCD. | Done | Принято. |
| REQ-DATA-004 | Кодирование 10-битной ячейки данных: `{hundreds[1:0], tens[3:0], ones[3:0]}`. | Done **[v0.6]** | Зафиксировано в памяти и в упаковке/распаковке внутри ApLine. |
| REQ-DATA-005 | При чтении из RAM старшие 2 бита hundreds-цифры восстанавливаются как `2'b00`. | Done **[v0.6]** | Реализовано в ApLine при разворачивании десятибитной ячейки в двенадцатибитный код счётчика. |
| REQ-DATA-006 | Терминальная шина данных — 8 бит. | Done | Внешний терминал/UART/Console. |
| REQ-DATA-007 | Преобразование BCD ↔ ASCII допускается выполнять вне лампового ядра, если это внешний интерфейс. | Done | Реализовано: `AsciiToBcd`/`BcdToAscii`, 256-элементные LUT в `Functions/`. |

## 4.4. Текущие ограничения архитектуры [v0.9]

Набор программ, входы и полные метрики лежат в сабмодуле `bfutils/programs/bf100/`, программы разложены по категориям, источники и лицензии — в его README.

Ёмкости при конфигурации REQ-ARCH-010:

| Ресурс | Ёмкость | Определяет | Что не помещается |
|---|---:|---|---|
| Память программ | 99 900 команд | IP, 5 декатронов, минус 100 ячеек загрузчика | `LostKng.b` — 2 110 289 команд |
| Память данных | 30 000 ячеек | AP с пределом 29999 | `awib-0.4.b` на длинном входе — 30 647; бесконечные генераторы со временем |
| Вложенность при промотке | 99 | Loop, 2 декатрона | `OptimTease.b` (вне набора) — 258 |
| Значение ячейки | 0–255 по кругу | Data, 3 декатрона | программы, рассчитанные на 16- и 32-битные ячейки |
| Левый край ленты | переход 0 → 29999 | AP | программы, использующие дальний правый край вместе с ячейкой −1 |

Десять программ, определяющих ограничения, — использование счётчиков:

| Программа | Что проверяет | IP, команд | AP, ячеек | Loop, макс. | Инструкций | Шагов промотки |
|---|---|---:|---:|---:|---:|---:|
| `LostKng.b` — текстовая игра Lost Kingdom | предел памяти программ | **2 110 289** ✗ | 651 | 5 | 9,9·10⁷ | 1,1·10⁹ |
| `hanoi-opt.bf` — Ханойские башни с анимацией | длинная программа | 44 354 | 276 | 9 | 3,2·10⁸ | 4,0·10⁸ |
| `pi-digits.bf` — π до 30 знаков | длинная программа и счёт | 37 655 | 1 245 | 13 | 3,2·10¹⁰ | 3,5·10¹⁰ |
| `Zozotez.b` — интерпретатор LISP | длина и вложенность | 35 269 | 2 648 | 33 | 5,0·10⁸ | 5,2·10⁸ |
| `awib-0.4.b` — компилятор awib | предел памяти данных | 33 528 | **30 647** ✗ | 31 | 1,4·10⁸ | 4,5·10⁸ |
| `cristofd-30000.b` — проверка ленты | ровно 30 000 ячеек | 100 | 30 000 | 4 | 1,8·10⁷ | 1,8·10⁷ |
| `BusyBeaver.b` — «усердный бобёр» | длинная лента | 79 | 27 306 | 3 | 4,0·10⁸ | 4,0·10⁸ |
| `Collatz.b` — гипотеза Коллатца | длинная лента и долгий счёт | 379 | 26 581 | 5 | 4,1·10⁹ | 6,6·10⁹ |
| `Kiloseconds.b` — время в килосекундах | максимум вложенности | 1 675 | 23 | **67** | 1,9·10⁴ | 1,8·10⁴ |
| `password-vault.bf` — проверка пароля | глубокая вложенность в тексте | 3 623 | 9 | 52 (в тексте 124) | 8,1·10³ | 6,1·10³ |

Для сравнения — программа проекта `pi.bfk`: 618 команд, 66 ячеек (включая ячейку −1), Loop — 11, 198 594 инструкции, 313 968 шагов промотки.

По набору в целом: медиана максимума Loop — 5, у 22 программ из 100 он не меньше 10. Счётчик Data у всех программ работает в диапазоне 0–255 с переходом по кругу.

---

# 5. Память

## 5.1. Память инструкций

| ID | Требование | Статус | Комментарий |
|---|---|---:|---|
| REQ-MEM-IP-001 | Ёмкость памяти инструкций: 100 000 ячеек. | Done | Подтверждено (`IpMemory`, `ROWS = 10**IP_DEKATRON_NUM`). |
| REQ-MEM-IP-002 | Ширина ячейки программы: 4 бита. | Done | Opcode. |
| REQ-MEM-IP-003 | Физическая организация: 1000 банков по 10×10 ячеек. | Done **[v0.6]** | Относится к ФИЗИЧЕСКОЙ машине и P&R: `BANK_DIGITS = 2`. Реализовано рекурсивной иерархией: банк 10×10 (2 декатрона) → группа из 10 (3) → и далее. **[v0.8]** Эмулятор использует ту же память с `BANK_DIGITS = 4` — см. REQ-MEMV2-008. |
| REQ-MEM-IP-004 | Банки должны адресоваться BCD-сигналами без появления логических пропусков. | Done **[v0.6]** | Тетрада выбирает потомка сравнением, адресной арифметики нет. Тетрады A..F не выбирают никого и поднимают `p_slverr`. |
| REQ-MEM-IP-005 | В FPGA-эмуляторе допускается RAM + ROM overlay. | Done **[v0.6]** | Загрузчик занимает ровно один банк 10×10 (100 инструкций). Преобразование BCD→binary больше не требуется. |
| REQ-MEM-IP-006 | Bootloader занимает последние 100 инструкций: `99900–99999`. | Done | Подтверждено RTL. |
| REQ-MEM-IP-007 | Bootloader не отключается. | Done | Принято. |
| REQ-MEM-IP-008 | Bootloader исполняется после Hard Reset только при включённом тумблере автозапуска. | Done | Принято, `RunOnHardRst` в Emulator. |

## 5.2. Память данных

| ID | Требование | Статус | Комментарий |
|---|---|---:|---|
| REQ-MEM-DATA-001 | Ёмкость памяти данных для базового режима: 30 000 ячеек. | Done | Подтверждено (`RAM` 30000×8bit в `DekatronPC.sv`). |
| REQ-MEM-DATA-002 | Физическая ширина ячейки данных: 10 бит. | Done **[v0.6]** | Зафиксировано: `{hundreds[1:0], tens[3:0], ones[3:0]}`, диапазон 0..255. Расхождение с прежним 8-битным RTL закрыто. |
| REQ-MEM-DATA-003 | Физическая организация: 300 банков по 10×10 ячеек. | Done **[v0.6]** | Относится к физической машине (`BANK_DIGITS = 2`). Та же иерархия, что и для памяти программ, отличается шириной ячейки. **[v0.8]** В эмуляторе — три банка 100×100. |
| REQ-MEM-DATA-004 | Банки должны адресовываться BCD-сигналами без появления логических пропусков. | Done **[v0.6]** | Аналогично REQ-MEM-IP-004. |
| REQ-MEM-DATA-005 | Если будет выбран AP-режим `0–99999`, объём Data RAM должен быть увеличен до 100 000 ячеек. | In Review | Ожидает оценки вместе с REQ-CNT-005. **[v0.10]** Текущий RTL уже в этом режиме: `Ram` данных на 100 000 ячеек (`D_NUM = AP_DEKATRON_NUM`), счётчик AP в `ApLine` без верхнего предела (`TOP_LIMIT_MODE = 0`, `AP_TOP_VALUE` не подключён), AP переходит 0 ↔ 99999. OPEN-001 остаётся открытым. |
| REQ-MEM-DATA-006 | После включения/сброса память данных должна быть готова к работе с нулевыми ячейками согласно Brainfuck-семантике. | TODO | Bootloader/очистка. |

## 5.3. Bootloader

| ID | Требование | Статус | Комментарий |
|---|---|---:|---|
| REQ-BOOT-001 | Bootloader размещается в адресах `99900–99999`. | Done | Подтверждено RTL. |
| REQ-BOOT-002 | Hard Reset устанавливает IP на начало bootloader. | Done | `IP = 99900`. |
| REQ-BOOT-003 | Bootloader должен очищать Data RAM до нулей. | TODO | Требуется реализация/проверка. |
| REQ-BOOT-004 | Bootloader может завершаться Soft Reset, Halt или переходом к программе. | In Review | Нужно выбрать точное поведение. |
| REQ-BOOT-005 | Bootloader должен использовать Debug-циклы для обхода/очистки памяти данных. | In Review | Соответствует исходной идее (см. пример в PDF §7.3.3). |

---

# 6. Набор инструкций

## 6.1. Общие требования

| ID | Требование | Статус | Комментарий |
|---|---|---:|---|
| REQ-ISA-001 | Текущая таблица опкодов считается около-финальной. | Done | Уже используемые коды не менять. |
| REQ-ISA-002 | Инструкции NOP, HALT, ISA0, ISA1 присутствуют в обоих ISA. | Done | Подтверждено RTL (`insnValues.sv`). |
| REQ-ISA-003 | Пустые/undefined опкоды исполняются как NOP. | Done | Принято. |
| REQ-ISA-004 | Undefined opcode не вызывает аппаратную ошибку. | Done | Принято. |
| REQ-ISA-005 | В симуляции undefined opcode может дополнительно логироваться/подсвечиваться. | TODO | Опционально для отладки. |
| REQ-ISA-006 | Добавить инструкцию BELL. | Done **[v0.6]** | Опкод `0x02` подключён в MachineCtrl, выход `bell` выведен. |

## 6.2. Debug ISA

| Opcode | Мнемоника | Назначение | Статус |
|---:|---|---|---|
| 0x0 | NOP | Нет операции | Done |
| 0x1 | HALT | Останов | Done |
| 0x2 | BELL | Вызов оператора / звонок | TODO — отсутствует в RTL |
| 0x3 | reserved | Пустой opcode, ведёт себя как NOP | Done |
| 0x4 | EOT | Конец загрузки программы | Done |
| 0x5 | SOT | Начало загрузки программы | Done |
| 0x6 | LABEG / `{` | Пропустить тело цикла, если AP == 0 | Done |
| 0x7 | LAEND / `}` | Повторить цикл, если AP != 0 | Done |
| 0x8 | CLRL | Сброс Loop Counter | Done |
| 0x9 | CLRI | Сброс IP Counter и MemLock | Done |
| 0xA | CLRD | Сброс Data Counter | In Review |
| 0xB | CLRA | Сброс AP Counter и MemLock | Done |
| 0xC | HRST | Hard Reset | In Review **[v0.3]** | 
| 0xD | SRST | Soft Reset | In Review **[v0.3]** |
| 0xE | ISA0 | Переход в Debug ISA | Done |
| 0xF | ISA1 | Переход в Brainfuck ISA | Done |

> **[v0.3] Несогласованность найдена:** v0.2 фиксирует `0xC = HRST`, `0xD = SRST` (REQ-ISA-DEBUG-008/009). В `1786044911450-rtl-functional-report.md` (`insnValues.sv`) присутствует только `5'h0D = RST` (Hard Reset), опкод `0x0C` в отчёте не упомянут отдельно, `SRST` как отдельный код не подтверждён. **Требуется сверка кода `insnValues.sv` построчно с этой таблицей** — вынесено в раздел 18 как открытый пункт.

### Требования Debug ISA

| ID | Требование | Статус | Комментарий |
|---|---|---:|---|
| REQ-ISA-DEBUG-001 | Debug-циклы `{`/`}` проверяют AP, а не Data. | Done | Подтверждено (`LoopValZero = InsnMode ? DataZero : ApZero`). |
| REQ-ISA-DEBUG-002 | `LABEG`: если AP == 0 — пропустить тело цикла. | Done | Принято. |
| REQ-ISA-DEBUG-003 | `LAEND`: если AP != 0 — повторить итерацию. | Done | Принято. |
| REQ-ISA-DEBUG-004 | `CLRI` сбрасывает IP Counter и MemLock. | Done | Подтверждено. |
| REQ-ISA-DEBUG-005 | `CLRA` сбрасывает AP Counter и MemLock. | Done | Подтверждено. |
| REQ-ISA-DEBUG-006 | `CLRL` сбрасывает Loop Counter. | Done | Принято. |
| REQ-ISA-DEBUG-007 | `CLRD` сбрасывает Data Counter. | In Review | Влияние на MemLock требует уточнения (см. REQ-ML-009). |
| REQ-ISA-DEBUG-008 | `HRST` вызывает Hard Reset. | Done **[v0.6]** | Опкод `0x0C` подключён: выдаётся `hard_rst_req`, машина ждёт снятия `rst_busy`. |
| REQ-ISA-DEBUG-009 | `SRST` вызывает Soft Reset. | Done **[v0.6]** | Опкод `0x0D` подключён, выдаётся `soft_rst_req`. Вопрос «нужен ли opcode-триггер» решён положительно: он нужен для завершения загрузчика. |
| REQ-ISA-DEBUG-010 | Opcode `0x3` считается пустым и исполняется как NOP. | Done | Подтверждено. |

## 6.3. Brainfuck ISA

| Opcode | Мнемоника | BF | Назначение | Статус |
|---:|---|---|---|---|
| 0x0 | NOP | — | Нет операции | Done |
| 0x1 | HALT | — | Останов | Done |
| 0x2 | INC | `+` | Инкремент данных | Done |
| 0x3 | DEC | `-` | Декремент данных | Done |
| 0x4 | AINC | `>` | Инкремент AP | Done |
| 0x5 | ADEC | `<` | Декремент AP | Done |
| 0x6 | LBEG | `[` | Пропустить цикл, если данные == 0 | Done |
| 0x7 | LEND | `]` | Повторить цикл, если данные != 0 | Done |
| 0x8 | COUT | `.` | Вывод | Done |
| 0x9 | CIN | `,` | Ввод | Done |
| 0xA | CLRD | `[-]` | Обнуление текущей ячейки | In Review |
| 0xB | CLRML | — | Сброс MemLock | Done |
| 0xC | LOAD | — | Явная загрузка из RAM в Data Counter | Done |
| 0xD | STORE | — | Явная запись Data Counter в RAM | Done |
| 0xE | ISA0 | — | Переход в Debug ISA | Done |
| 0xF | ISA1 | — | Переход в Brainfuck ISA | Done |

### Требования Brainfuck ISA

| ID | Требование | Статус | Комментарий |
|---|---|---:|---|
| REQ-ISA-BF-001 | Brainfuck-циклы `[`/`]` проверяют значение данных, а не адрес. | Done | Подтверждено. |
| REQ-ISA-BF-002 | `LOAD` и `STORE` не изменяют MemLock. | Done | Подтверждено. |
| REQ-ISA-BF-003 | `LOAD` после `+`/`-` перезаписывает Data Counter значением из RAM по текущему AP. | Done | Нужно покрыть тестами. |
| REQ-ISA-BF-004 | `STORE` без предварительного `LOAD` записывает текущее значение Data Counter в RAM. | Done | Используется для копирования. |
| REQ-ISA-BF-005 | `.` и `,` при активном MemLock работают со значением в Data Counter. | Done | Нужно покрыть тестами. |
| REQ-ISA-BF-006 | `CLRML` принудительно сбрасывает MemLock. | Done | Принято. |

---

# 7. BELL и оператор

| ID | Требование | Статус | Комментарий |
|---|---|---:|---|
| REQ-BELL-001 | В Debug ISA реализовать инструкцию `BELL` по opcode `0x2`. | TODO | Подтверждено отсутствие в RTL. |
| REQ-BELL-002 | `BELL` не изменяет IP, AP, Data, Loop, MemLock. | TODO | Кроме собственного advance IP. |
| REQ-BELL-003 | Машина должна иметь физический/эмуляторный выход BELL. | TODO | Звонок, лампа, реле. Не найдено в Emulator-отчёте. |
| REQ-BELL-004 | BELL может автоматически вызываться при входе в CIN. | TODO | Требует тумблера. |
| REQ-BELL-005 | BELL может автоматически вызываться при HALT. | TODO | Требует тумблера. |
| REQ-BELL-006 | BELL может автоматически вызываться при hardware error. | TODO | Требует тумблера. |
| REQ-BELL-007 | Панельные тумблеры: `BellOnCIN`, `BellOnHALT`, `BellOnError`. | TODO | Состав может быть уточнён. |

---

# 8. Сбросы и панельное управление

## 8.1. Hard Reset

| ID | Требование | Статус | Комментарий |
|---|---|---:|---|
| REQ-RST-001 | Hard Reset устанавливает IP Counter на начало bootloader: `99900`. | Done | Подтверждено. |
| REQ-RST-002 | Hard Reset устанавливает AP, Data, Loop в 0. | Done | Принято. |
| REQ-RST-003 | Hard Reset сбрасывает MemLock. | Done | Принято. |
| REQ-RST-004 | Hard Reset устанавливает ISA в Debug. | Done | Подтверждено (`InsnDecoder`: `HardRst → ISA=DEBUG`). |
| REQ-RST-005 | Hard Reset сбрасывает error-флаги. | TODO | Error-флагов пока нет вообще (см. REQ-CNT-007). |
| REQ-RST-006 | После снятия Hard Reset при включённом тумблере автозапуска bootloader машина начинает исполнять bootloader. | Done | Принято. |
| REQ-RST-007 | Если автозапуск bootloader выключен, машина ждёт Run или Step. | Done | Принято. |

## 8.2. Soft Reset

| ID | Требование | Статус | Комментарий |
|---|---|---:|---|
| REQ-RST-010 | Soft Reset устанавливает все счётчики в 0. | Done | Главное отличие от Hard Reset. |
| REQ-RST-011 | Soft Reset устанавливает IP = 0. | Done | Принято. |
| REQ-RST-012 | Soft Reset сбрасывает MemLock. | Done | Принято. |
| REQ-RST-013 | Soft Reset устанавливает ISA в Brainfuck. | Done | Подтверждено (`SoftRst → ISA=BRAINFUCK`). |
| REQ-RST-014 | Soft Reset сбрасывает error-флаги. | TODO | Аналогично REQ-RST-005. |
| REQ-RST-015 | При включённом тумблере автозапуска программы машина начинает исполнение с IP = 0. | Done | Принято. |
| REQ-RST-016 | Если автозапуск выключен, машина ждёт Run или Step. | Done | Принято. |

## 8.3. Панельные тумблеры

| ID | Требование | Статус | Комментарий |
|---|---|---:|---|
| REQ-PANEL-001 | Тумблер `RunBootloaderAfterHardRst`. | Done | В RTL — `RunOnHardRst` (сейчас захардкожен `1'b0` в Emulator, требуется реальный тумблер). |
| REQ-PANEL-002 | Тумблер `RunProgramAfterSoftRst`. | Done | В RTL — `RunOnSoftRst` (аналогично захардкожен `1'b0`). |
| REQ-PANEL-003 | Тумблер `SoftRstOnEOT`. | Done | Подтверждено, в Emulator сейчас захардкожен `1'b1`. |
| REQ-PANEL-004 | Тумблер `BellOnCIN`. | TODO | Опционально. |
| REQ-PANEL-005 | Тумблер `BellOnHALT`. | TODO | Опционально. |
| REQ-PANEL-006 | Тумблер `BellOnError`. | TODO | Опционально. |
| REQ-PANEL-007 | Тумблеры конфигурации UART. | TODO | Для FPGA-эмулятора. Не найдено — скорость 110 бод захардкожена. |
| REQ-PANEL-008 | Тумблер EchoMode. | In Review | Подтверждено: в Emulator сейчас `EchoMode = 1'b1` всегда (захардкожен). |

> **[v0.3] Замечание:** несколько тумблеров, задокументированных как «Done» в v0.2, по факту в RTL реализованы как **захардкоженные константы**, а не переключаемые физические тумблеры (`RunOnHardRst=0`, `RunOnSoftRst=0`, `SoftRstOnEOT=1`, `EchoMode=1`). Формально сигнал в интерфейсе `DekatronPC` есть (Done по контракту модуля), но физического тумблера на плате/эмуляторе — нет (TODO по железу/панели). Статусы оставлены как в v0.2 (интерфейс), но это несоответствие явно вынесено в раздел 19 чек-листа отдельными пунктами.

---

# 9. Загрузка программ: SOT/EOT

| ID | Требование | Статус | Комментарий |
|---|---|---:|---|
| REQ-LOAD-001 | После исполнения `SOT` машина переходит в режим приёма инструкций по текущему адресу, т.е. по адресу после SOT. | Done | Принято. |
| REQ-LOAD-002 | Машина сама инкрементирует IP после каждой принятой инструкции. | Done | Принято. |
| REQ-LOAD-003 | Приём инструкций идёт по handshake: `InsnInValid` / `InsnInReady`. | Done | Подтверждено сигнатурой `IpLine`/`Emulator`. |
| REQ-LOAD-004 | Стартовый адрес загрузки может быть любым. | Done | Принято. |
| REQ-LOAD-005 | Основное предполагаемое размещение `SOT` — старший адрес памяти, чтобы после инкремента IP перейти в 0. | Done | Для 5-разрядного IP. |
| REQ-LOAD-006 | Пользовательская программа может исполнить `SOT`. | TODO | Нужно проверить тестами. |
| REQ-LOAD-007 | При приёме `EOT` машина завершает режим загрузки. | Done | Принято. |
| REQ-LOAD-008 | Если включён тумблер `SoftRstOnEOT`, после EOT выполняется Soft Reset. | Done | Принято. |
| REQ-LOAD-009 | Если `SoftRstOnEOT` выключен, машина либо остаётся в Halt, либо при автозапуске исполняет программу с текущего адреса. | Done | Принято. |
| REQ-LOAD-010 | Переполнение памяти программ не отслеживается. | Done | Явное не-требование. |
| REQ-LOAD-011 | Загрузка программ возможна с клавиатуры, терминального параллельного порта, перфоленты и магнитной ленты. | TODO | Нужна внешняя обвязка. В RTL сейчас — клавиатура и 2 предзашитых `FirmwareLoader` (Hello World, Pi). |
| REQ-LOAD-012 | Переключение источников загрузки может выполняться релейными блоками. | Done | Редкое переключение. В эмуляторе сейчас — `selector[3:0]`, программный мультиплексор. |
| REQ-LOAD-013 | Основной канал ввода инструкций — 4-битный opcode-канал. | Done | Принято. |
| REQ-LOAD-014 | К 4-битному каналу могут подключаться DTMF-декодер магнитной ленты, считыватель перфоленты или ASCII→opcode энкодер. | TODO | Нужно зафиксировать интерфейсы. |
| REQ-LOAD-015 | В FPGA-эмуляторе должна поддерживаться загрузка через UART и/или внешний параллельный терминальный канал. | In Progress | UART есть (110 бод), но подключён к CIN/COUT-каналу, а не к каналу загрузки инструкций напрямую — путать не стоит, это два разных канала. |
| REQ-LOAD-016 **[v0.3]** | `SOT` должна явно и однозначно переключать ISA-регистр (в текущем RTL поведение не зафиксировано этим документом отдельно). | Assumption **[v0.3]** | Рабочее допущение: оставить поведение как в текущем RTL (см. раздел 1). Требуется явное подтверждение. |

---

# 10. MemLock и доступ к памяти данных

| ID | Требование | Статус | Комментарий |
|---|---|---:|---|
| REQ-ML-001 | MemLock защёлкивается перед первым `+` или `-`, если значение ещё не загружено в Data Counter. | Done | Базовая оптимизация. |
| REQ-ML-002 | При активном MemLock последовательности `+`, `-`, `.`, `,` работают с Data Counter без лишнего чтения/записи RAM. | Done | Принято. |
| REQ-ML-003 | MemLock сбрасывается при необходимости записать значение обратно в RAM. | Done | Точные события должны быть специфицированы. |
| REQ-ML-004 | Явные `LOAD` и `STORE` не изменяют MemLock. | Done | Подтверждено. |
| REQ-ML-005 | При смене AP через `>`/`<` при активном MemLock значение Data Counter должно быть записано в старую ячейку. | Done **[v0.6]** | Реализовано в ApLine: выгрузка выполняется до шага счётчика адреса. |
| REQ-ML-006 | `CLRI` сбрасывает MemLock. | Done | Подтверждено. |
| REQ-ML-007 | `CLRA` сбрасывает MemLock. | Done | Подтверждено. |
| REQ-ML-008 | `CLRML` выгружает счётчик в память и снимает MemLock. | Done **[v0.6]** | Уточнено: без выгрузки значение терялось бы. |
| REQ-ML-009 | `CLRD` выставляет MemLock. | Done **[v0.6]** | **Допущение v0.3–v0.5 опровергнуто проверкой.** Если MemLock не выставлять, `[-]` не обнуляет ячейку: ноль ложится в счётчик, счётчик считается устаревшим, и при смене адреса из памяти возвращается прежнее значение. Симметрия с LOAD/STORE обманчива — те не меняют содержимое ячейки, а CLRD меняет. |
| REQ-ML-010 | Поведение `.` и `,` при активном MemLock должно быть покрыто тестами. | TODO | Особенно CIN/COUT. |

---

# 11. Декатроны и временные параметры

| ID | Требование | Статус | Комментарий |
|---|---|---:|---|
| REQ-DEK-001 | Модель декатрона отражает 10 главных катодов и 30 физических катодов. | Done | Подтверждено (`Dekatron.sv`: `Cathodes[29:0]`, 3 триады × 10). |
| REQ-DEK-002 | FPGA-эмулятор использует `Clk = 1 MHz` как процессорный такт. | Done | Принято. |
| REQ-DEK-003 | FPGA-эмулятор использует `hsClk = 10 MHz` для моделирования длительностей импульсов декатрона. | Done | Принято, совпадает с параметром `HS_PER_CLK=10` из TRS v0.1. |
| REQ-DEK-004 | В реальной машине `hsClk = 10 MHz` не требуется. | Done | Декатрон реагирует на длительности сам. |
| REQ-DEK-005 | Импульс записи/сброса декатрона примерно в 10 раз длиннее счётного импульса. | Done | Оценка подтверждена (RTL: `OneShot#(DELAY=100)` на запись vs `DELAY=3/4/8/9` на счётный импульс). |
| REQ-DEK-006 | Текущая задержка записи `100 hsClk` является оценочной и должна уточняться экспериментами. | In Progress | Совпадает с `WRITE_MIN_HS=100` из TRS v0.1. Нужны измерения на стенде. |
| REQ-DEK-007 | Перенос между декатронами работает параллельно: контроль текущего значения и запрошенной операции. | Done | Текущая RTL-логика через `DekatronCarrySignal` (`RsLatch` на `CarryLow`/`CarryHigh`). |
| REQ-DEK-008 | FPGA-эмулятор должен максимально точно имитировать задержки реальных декатронов. | Done | Принято. |
| REQ-DEK-009 | После синтеза в физическую библиотеку поведение должно сохраняться без служебного `hsClk`, если это требуется для физической модели. | TODO | Критично для Yosys/physical flow. |
| REQ-DEK-010 | RTL должен допускать замену `OneShot`/`hsClk`-модели на физическую модель задержек/таймеров без изменения ISA. | In Progress **[v0.10]** | Архитектурно заложить. Согласуется с §18.2–18.3 TRS v0.1 (SYNTH-подмена). **[v0.10]** Первый шаг — сам декатрон: `DekatronTubeDelay` (без `hsClk`, инерционные задержки `#N` в нс, те же параметры `*_HS`), выбирается `` `define DEKATRON_DELAY_MODEL `` в `DekatronModule`. Все Icarus-тесты и pi.bfk проходят на RTL и на нетлисте (`run_tests.sh -d`, `synth_sim.sh -d`, CI `sim_delay`/`synth_sim_delay`). Второй шаг: тем же define `Impulse`, `OneShot`, `DekatronPhaseGen`, `DekatronPulseSender` переходят на задержки (ветки `` `ifdef ``/`` `else `` в тех же модулях, порты не меняются), и `DekatronCounter` работает без `hsClk`: Counter_tb и Dekatron_tb держат `hsClk` в нуле и проходят, в нетлисте у всех `Impulse`/`OneShot` `.Clk(1'h0)`. Третий шаг: так же переведено `RstTimeRelay`, и весь `DekatronPC` работает с `hsClk` в нуле (`DekatronPC_tb` под define сам формирует `Clk`); порт `hsClk` остаётся (Приложение B), но внутрь не идёт. helloworld, program.bfk и pi.bfk проходят на RTL и на нетлисте с теми же числами тактов, что и тактовая модель. Отчёт: `doc/dekatron_delay_model.md` §8–9. |
| REQ-DEK-011 | Для формирователя импульсов сброса/записи допускается использовать реле времени или аналогичный физический таймер. | Done | Принято. |
| REQ-DEK-012 **[v0.4]** | Декатрон физически не реализует и не может реализовать `valid`/`ready`/`busy` или любую форму handshake. Он только реагирует на внешние воздействия заданной длительности, независимо от своего текущего внутреннего состояния. Всю дисциплину операций (включая обработку коротких/пропущенных импульсов) обеспечивает вышестоящий блок. | Done (принцип) | Формализованный физический контракт — см. раздел 1 (v0.4) и TRS v0.1 §2.2. Обязателен к соблюдению в `DekatronTubeV2` и любых будущих моделях декатрона. |
| REQ-DEK-013 **[v0.4]** | Метастабильное состояние (разряд на подкатоде) допустимо использовать в assertions симуляции, но оно не является физически снимаемым чистым сигналом и не должно трактоваться верхним уровнем как надёжный логический выход. | Done (принцип) | Согласуется с TRS v0.1 §3.2 (`on_guide_dbg_o` — debug-only, не физический выход). |
| REQ-DEK-014 **[v0.4]** | В RTL-блоке декатрона временные характеристики должны присутствовать как явные параметры. | Done **[v0.5]** | Закрыто. Реализованы `GUIDE_STEP_HS`, `FALL_STEP_HS`, `GUIDE_MAX_HS`, `WRITE_MIN_HS`, `RESET_MIN_HS`. `PHASE_WINDOW_HS`/`RETURN_TIMEOUT_HS` не реализованы намеренно — упразднены кольцевой моделью (см. REQ-DTV2-010). |
| REQ-DEK-015 **[v0.5]** | На подкатоде разряд остаться не может: при снятии подкатодных сигналов он сваливается на соседний главный катод — с первого подкатода назад, со второго вперёд. | Done (принцип) | Ключевое физическое свойство, на котором построена кольцевая модель. Из него следуют возврат при неполной последовательности и отсутствие частичного инкремента. |
| REQ-DEK-016 **[v0.5]** | Показание декатрона достоверно только когда разряд стоит на главном катоде и внешних воздействий нет. Во всех прочих состояниях позиционный код нулевой. | Done | Реализовано: `main_onehot_o` обнуляется вне устойчивого состояния. Отдельного признака достоверности нет **[v0.10]**: верхний уровень опирается на известные длительности, а не на чтение катодов. |

## 11.4. DekatronTubeV2 — целевая модель декатрона [v0.3]

TRS v0.1 (`Dekatron_Model_TRS_v0_1.md`) задаёт **новую целевую модель** одного декатрона — `DekatronTubeV2`, с интерфейсом и FSM, заметно отличающимися от того, что реально используется в текущем RTL (`Dekatron.sv` + `DekatronModule.sv` + `DekatronPulseSender.sv`).

| ID | Требование | Статус | Комментарий |
|---|---|---:|---|
| REQ-DTV2-001 | `DekatronTubeV2` должна моделировать только физику одного декатрона: положение разряда, реакцию на подкатодные импульсы, запись, сбросы. | Done **[v0.5]** | Реализовано (`DekatronTubeV2.sv`). Проверено на 90 сценариях плана TRS v0.1 §14 на двух наборах параметров. |
| REQ-DTV2-002 | `DekatronTubeV2` не должна включать `valid/ready/busy`, очередь команд, логику многоразрядного счёта, верхний предел — это ответственность `DekatronCounter`. | Done **[v0.5]** | Граница соблюдена: в модуле декатрона нет ни одного сигнала handshake. |
| REQ-DTV2-003 | Интерфейс: `guide_a_i`, `guide_b_i`, `write_en_i`, `write_pos_i` (one-hot), `reset0_i`, `resetN_i`, `main_onehot_o` + debug-выходы. | Done **[v0.5]** | Отличие от TRS v0.1: `reset9_i` обобщён до `resetN_i` с параметром `RESET_N_POS`. При 9 это прежний reset9, при 5 — линия сброса в 5 для счётчика данных до 255. Добавлены модельные `sim_preset_*` (не физические, отключаются параметром). |
| REQ-DTV2-004 | Отсутствие цифровых сбросов (`rst_n` и т.п.) как части физического интерфейса — только `reset0_i`/`reset9_i`. | Done (спецификация) | Прямо противоречит текущему RTL, где `Dekatron.sv` имеет `Rst_n` и `HardRst_n` как отдельные цифровые входы, причём с **дублированной** логикой под `EN_HARD_RST=0/1`. |
| REQ-DTV2-005 | FSM из 4 состояний: `ST_STABLE`, `ST_GUIDE`, `ST_WRITE_RESET`, `ST_INVALID`. | **Отменено [v0.5]** | Заменено кольцевой моделью (REQ-DTV2-010): состояние полностью описывается положением разряда в 30-битном кольце, отдельная FSM не нужна. Assertions сохранены и расширены инвариантом one-hot кольца. |
| REQ-DTV2-006 | Мигрировать текущий RTL (`Dekatron`/`DekatronModule`/`DekatronCounter`) на `DekatronTubeV2`, а не вести её параллельно. | Done (решение) **[v0.4]** | **Решение принято.** Порядок зафиксирован: сначала `DekatronTubeV2` реализуется и полностью покрывается тестами (TRS v0.1 §14–16) в изоляции, без handshake — затем и только затем начинается переписывание `DekatronCounter`/`IpLine`/`ApLine` под Valid/Ready вокруг неё. Закрывает OPEN-008. |
| REQ-DTV2-007 | `DekatronCounter` переписывается по контракту раздела 17 TRS v0.1: handshake, HardReset через `resetN`+`reset0` по разрядам, SoftReset через `reset0`. | Done **[v0.5]** | Реализовано (`DekatronCounter.sv`). Первый и единственный уровень, где вводится Valid/Ready. |
| REQ-DTV2-008 | Полный набор unit-тестов `DekatronTubeV2` (TRS v0.1 §14–16) переносится в верификационный набор. | In Progress **[v0.5]** | Тестбенч написан (`DekatronTubeV2_tb.sv`, 5 конфигураций DUT). **Не прогонялся в симуляторе** — проверка выполнялась на такт-в-такт Python-копии RTL. Требуется прогон в Verilator. Не покрыты операции «встык» (см. REQ-VER-028). |
| REQ-DTV2-009 **[v0.5]** | Смена цели операции записи/сброса без снятия воздействия (импульс по другому катоду встык) должна трактоваться как новая операция и перезапускать отсчёт длительности. | Done | Найдено тестированием: `SetZero` сразу после `SetTop` не срабатывал. Исправлено отслеживанием цели операции. |
| REQ-DTV2-010 **[v0.5]** | Состояние декатрона описывается 30-битным кольцевым регистром (one-hot), перемещение разряда — циклический сдвиг. Явная FSM, `prev_digit`, `target_digit`, окно фазы и таймаут возврата не используются. | Done | Заменяет REQ-DTV2-005. Инвариант one-hot проверяется assertion. |

## 11.5. Реализованная подсистема декатрона [v0.5]

Состав: `DekatronTubeV2` → `DekatronModule` → `DekatronCounter`, плюс `DekatronPhaseGen`, `DekatronPulseSender`, кодеры `BinToBcd` и `BcdToBinEn`. Признака достоверности у модуля нет **[v0.10]**.

### Формирователь импульсов

| ID | Требование | Статус | Комментарий |
|---|---|---:|---|
| REQ-PULSE-001 | Такт счёта делится на три интервала: первый подкатод, второй подкатод, пауза на сваливание разряда. | Done | Деление на две полуволны проверено и отвергнуто: счёт не идёт вовсе. |
| REQ-PULSE-002 | Третий интервал обязателен и должен вмещать `FALL_STEP_HS` с запасом **[v0.10]**: окно строго больше `FALL_STEP_HS`, чтобы разряд был на главном катоде до следующего фронта `clk`. | Done | Проверяется `$error` на этапе компиляции в `DekatronModule`. При 3/4/3 окно равнялось `FALL_STEP_HS` и разряд падал на самом фронте; нарезка по умолчанию — 3/3/4 **[v0.10]**. |
| REQ-PULSE-003 | Направление счёта меняет порядок фаз, а не логику: вперёд — первая фаза на подкатод A, назад — на подкатод B. | Done | Реализовано мультиплексированием, 4 И и 2 ИЛИ. |
| REQ-PULSE-004 | Времязадающая часть выделена в отдельный модуль и моделирует RC-цепи реальной схемы. | Done | `DekatronPhaseGen` на `Impulse` + двух `OneShot`. При физическом синтезе заменяется реальной времязадающей цепью. |
| REQ-PULSE-005 | Генератор фаз общий на весь многоразрядный счётчик: фазы одинаковы для всех декад, шагает та, которой цепочка переноса разрешила. | Done | Параметр `EXT_PHASES`. Для шестидекадного счётчика экономит пять времязадающих цепей. |
| REQ-PULSE-006 | Шаг подаётся на декаду уровнем на весь такт, а не импульсом. | Done | Следствие нарезки на трети. Снятие запроса в середине такта оставит разряд на подкатоде — требование к вышестоящему блоку. **[v0.10]** Уровнем держится разрешение декады `En`. |
| REQ-PULSE-007 **[v0.10]** | Формирователь импульсов один на счётчик: `DekatronPulseSender` в `DekatronCounter` выдаёт общие шины `GuideA`/`GuideB` в порядке, заданном направлением, а декада пропускает их на свои подкатоды двумя ключами — по лампе J2 (пентод с двумя управляющими сетками: импульс подкатода и `En`) на подкатод — по разрешению `En` из цепочки переноса. | Done | Владелец, 2026-10-08 (T5). Ключ — ячейка `GUIDE_EN_J2` в `vtube_cells.lib` (1 лампа J2 на подкатод, 2 на декаду; без функции: ABC её не использует), у `DekatronModule` порты `GuideA`, `GuideB`, `En` вместо `StepF`/`StepR`/`Phase*_i`. Было 6 ламп И-ИЛИ на декаду, стало 2 (`doc/tube_count_reduction.md` §17.7). |

### Декатронный модуль

| ID | Требование | Статус | Комментарий |
|---|---|---:|---|
| REQ-DMOD-001 | Декатрон присутствует всегда; преобразователь BCD→позиционный ставится только по `WRITE`, позиционный→BCD только по `READ`. | Done | Схема записи — самая дорогая по лампам часть обвязки. |
| REQ-DMOD-002 | Все вложенные блоки остаются отдельными инстансами для замены базовыми ячейками на этапе P&R. | Done | Внутри — вентильные примитивы. |
| REQ-DMOD-003 | Преобразователь BCD→позиционный выполняется пятивходовыми И, где пятый вход — сигнал записи. | Done | Соответствует схемотехнике из описания проекта (пятивходовые И на двух сдвоенных триодах, сетка — сигнал записи). |
| REQ-DMOD-004 | `TOP_LIMIT_MODE` подключает выход позиции `TOP_PIN_OUT` к линии `TopPin` для вышестоящего счётчика. | Done | Нужно для получения 255+1→0. |
| REQ-DMOD-005 | Сброс в нуль и в верхнюю позицию идут на выделенные катодные линии декатрона, а не подмешиваются в шину записи. | Done | Ручная сборка `InPosDek_n` из `Set[2:0]` упразднена. |
| REQ-DMOD-006 | ~~Модуль выдаёт признак достоверности показания.~~ | **Rejected [v0.10]** | Признак показывал только «разряд на главном катоде» и не говорил о завершении операции. Выход `Valid` и лампа `OR10_X7` удалены; готовность выводит `DekatronCounter` по длительностям (REQ-CNT-V2-002/003). |

### Счётчик

| ID | Требование | Статус | Комментарий |
|---|---|---:|---|
| REQ-CNT-V2-001 | Счётчик предоставляет Valid/Ready; `ready` не зависит от `valid`. | Done | Первый уровень иерархии, где handshake физически осмыслен. |
| REQ-CNT-V2-002 | Инкремент/декремент выполняется за один такт, `ready` при этом не снимается. | Done | Проверено: 12 операций подряд без снятия `ready`. Состояния `INC`/`DEC` упразднены. С **[v0.10]** это гарантия по длительности, а не по чтению катодов: показание и признаки достоверны на следующем фронте `clk` (REQ-PULSE-002). |
| REQ-CNT-V2-002a **[v0.7]** | `ready` не должен зависеть от сигнала окна записи. Готовность определяется только состоянием автомата и линиями сброса (признак установления разряда упразднён **[v0.10]**). | Done | Зависимость от окна замыкает комбинационную петлю через `accept`, поскольку окно этим же `accept` и запускается. Условие избыточно: состояние автомата уже несёт эту информацию. |
| REQ-CNT-V2-002b **[v0.7]** | Окно записи обязано быть длиннее такта счёта. | Done | Автомат проверяет окно по фронту `clk`; при более коротком окне он увидит его уже снятым и прервёт операцию. Проверяется на этапе компиляции. |
| REQ-CNT-V2-003 | Запись и сбросы по handshake снимают `ready` на время окна записи. | Done | Около 10 тактов `clk` при `WRITE_MIN_HS=100`. |
| REQ-CNT-V2-004 | Операнды не защёлкиваются **[v0.9]**: `dec`, `set`, `set_zero` нужны мастеру только до рукопожатия (`valid & ready`), `in` — до возврата `ready`, потому что идёт прямо в схему записи декатронов на всё окно записи. | Done **[v0.9]** | Решение владельца: регистр на входе убран ради экономии ламп. Единственный мастер с `set` — `ApLine` для счётчика данных: `in` — это `rx_data_bcd` (его держит передающая сторона, REQ-UART-008) или регистр памяти, выбор по `op`, а `MachineCtrl` держит `ap_op` до `ap_ready`, поэтому вход стабилен. Прежняя формулировка («защёлкиваются по accept») отменена. |
| REQ-CNT-V2-005 | `soft_rst` и `hard_rst` — физические линии счётчика, а не операции по handshake. Разводку по декадам выполняет счётчик. | Done **[v0.5]** | Только счётчик знает целевые позиции: `soft_rst` → нуль всех декад, `hard_rst` → девятка старших `HARD_RST_D_CNT` декад и нуль остальных. |
| REQ-CNT-V2-006 | Длительность сигналов сброса обеспечивает внешнее физическое реле времени. Растяжка внутри счётчика не реализуется. | Done **[v0.5]** | Лишняя логика поверх уже существующей физической цепи. В симуляции недостаточная длительность ловится проверкой. |
| REQ-CNT-V2-007 | Пока сброс активен, счётчик не готов и шаги не выдаются. | Done | Подкатодные импульсы во время сброса — недопустимое воздействие на декатрон. **[v0.10]** Подъём линии запускает окно `writeTimer` (состояние `ST_RST`); `ready` возвращается после снятия линии и конца окна. Сама линия не растягивается (REQ-CNT-V2-006). |
| REQ-CNT-V2-008 | Цепочка переноса строится на значениях, защёлкнутых до текущего шага, и распространяется в пределах одного такта. | Done | Значения защёлкиваются на каждом фронте `clk` **[v0.10]**: к фронту шаг завершён по длительности. |
| REQ-CNT-V2-008a **[v0.7]** | Рипл переноса не должен записываться поразрядно в вектор, который сам же и читается. | Done | Иначе Verilator видит зависимость сигнала от самого себя и выдаёт UNOPTFLAT, хотя петли физически нет: он анализирует зависимости с точностью до целого сигнала. Рипл вынесен в локальные переменные `always_comb`. |
| REQ-CNT-V2-009 | Счётчик выдаёт ~~признак достоверности показания и~~ признак достижения верхнего предела. | Done | `at_top`. `out_valid` удалён **[v0.10]**: мастер ждёт `ready`. **[v0.10]** `at_top` и `zero` берутся с катодов комбинационно (достоверны на фронтах при `ready`, как `out`); без `TOP_LIMIT_MODE` `at_top` = все декады на 9. IP и AP его не подключают. |
| REQ-CNT-V2-010 | `rst_n` сбрасывает только логику счётчика и не двигает разряд. | Done | Позицию задают исключительно катодные импульсы. |

---

# 12. Требования к RTL

## 12.1. Платформа и инструменты

| ID | Требование | Статус | Комментарий |
|---|---|---:|---|
| REQ-RTL-001 | Целевая FPGA-плата: DE0-Nano-SoC. | Done | Подтверждено (`De0Nano.sv`, Cyclone V, 50 МГц). |
| REQ-RTL-002 | Основная симуляционная среда: Verilator. | Done | Принято. |
| REQ-RTL-003 | Дополнительная симуляционная среда: Icarus Verilog. | Done | Принято. |
| REQ-RTL-004 | Синтез для FPGA сохраняется как рабочий flow. | Done | Quartus/Yosys по ситуации. **[v0.10]** Сборка битстрима из командной строки: `rtl/run/build_fpga.sh` (проект собирается из `DPC.files`/`Emul.files`, выводы из `rtl/quartus/Emulator.qsf`); elaboration проходит, полная компиляция ещё не запускалась (`doc/fpga_build.md`). |
| REQ-RTL-005 | Синтез в ламповую библиотеку через Yosys рассматривается как отдельный целевой flow. | TODO | Требуется для physical netlist. |

## 12.2. Стиль и синтезируемость

| ID | Требование | Статус | Комментарий |
|---|---|---:|---|
| REQ-RTL-010 | В RTL допускаются только синтезируемые конструкции. | Done | Есть исключения — см. REQ-RTL-015 [v0.3]. |
| REQ-RTL-011 | FPGA-трюки допускаются только выше блока `DekatronPC`, т.е. в слое эмулятора. | Done | Принято. |
| REQ-RTL-012 | Внутри `DekatronPC` не должно быть платформенно-зависимых FPGA-примитивов. | TODO | Нужно проверить. |
| REQ-RTL-013 | Стиль кода должен быть унифицирован в SystemVerilog. | TODO | `BcdToBin.v`/`BinToBcd.v` до сих пор в Verilog-95. |
| REQ-RTL-014 | Не допускается необоснованное подавление lint-предупреждений. | TODO | Особенно UNUSEDSIGNAL. |
| REQ-RTL-017 **[v0.8]** | Ассерты времени выполнения включаются условной компиляцией `` `ifdef ASSERTIONS ``, а не параметром модуля. | Done | Параметр требовал протаскивания через всю иерархию и молча оставался включённым там, где его забыли передать. |
| REQ-RTL-018 **[v0.8]** | Проверки конфигурации на этапе элаборации остаются под `` `ifndef SYNTH `` и не зависят от `ASSERTIONS`. | Done | Некорректную конфигурацию нужно ловить при каждой сборке, а не только при включённых ассертах. |
| REQ-RTL-015 **[v0.3]** | Маскирование выхода `DekatronModule` в `X` во время импульсов недопустимо как синтезируемая цель. | Done **[v0.5]** | Приём удалён. Заменён физически реализуемым сигналом `Valid` (ИЛИ по десяти линиям чтения, `OR10_X7`), который в свою очередь удалён **[v0.10]**. |
| REQ-RTL-016 **[v0.3]** | `Dekatron.sv` дублирует логику полностью для `EN_HARD_RST=0` и `EN_HARD_RST=1` вместо единой параметризованной ветки. | TODO | Технический долг, повышает риск рассинхронизации при правках. Кандидат на устранение при миграции на `DekatronTubeV2`. |

## 12.3. Такты и сбросы

| ID | Требование | Статус | Комментарий |
|---|---|---:|---|
| REQ-CLK-001 | Основной CPU-домен: 1 MHz. | Done | Принято. |
| REQ-CLK-002 | Физический моделирующий домен: 10 MHz hsClk. | Done | Только для FPGA-эмуляции. |
| REQ-CLK-003 | Остальные такты относятся к эмулятору/периферии и не обязательны для ядра. | Done | Подтверждено полным деревом тактов в отчёте (10MHz→1MHz→10KHz/1KHz→100Hz/1Hz). |
| REQ-CLK-004 | Необходимы CDC-правила для оценки критических путей. | TODO | Минимально необходимо. Особое внимание: `consul` (100 Hz) и UART (1 MHz) читают данные из домена `Clk` (1 MHz) — переходы не задокументированы. |
| REQ-RST-RTL-001 | Регистры имеют один асинхронный сброс. | Done | Принято. |
| REQ-RST-RTL-002 | Каждый декатрон поддерживает сброс в 0. | Done | Принято. |
| REQ-RST-RTL-003 | IP-декатроны должны поддерживать дополнительный сброс/установку в 9. | Done **[v0.3]** | Подтверждено: `TOP_LIMIT_MODE`/`SET_TOP` в `DekatronCounter`/`DekatronModule` реализуют установку в TOP_VALUE, используется для `IP=99900` через HardRst. Согласуется с TRS v0.1 §17.2 (`reset9_i` на разряды 4/3/2). |
| REQ-RST-RTL-004 | HardRst и SoftRst должны быть разделены на уровне декатронных счётчиков. | Done | Принято, подтверждено (`HardRst_n` отдельно от `Rst_n` в `DekatronCounter`). |

## 12.4. Рефакторинг по итогам аудита

| ID | Требование | Статус | Комментарий |
|---|---|---:|---|
| REQ-REF-001 | Устранить потерю запросов из-за однотактного импульсного handshake. | Done **[v0.6]** | Закрыто на всех уровнях: счётчик, память, обе линии, верхний автомат. |
| REQ-REF-002 | Перевести взаимодействие модулей на надёжный уровневый/Valid-Ready протокол. | Done **[v0.7]** | Единый протокол на всех уровнях: память, счётчики, обе линии, верхний автомат. Промежуточное решение v0.6 об APB для памяти отменено. |
| REQ-REF-003 | Удалить пустой `DekatronPulseAllow` и все его инстанцирования. | Done **[v0.5]** | Модуль не используется в новой подсистеме: цепочка переноса строится напрямую на защёлкнутых `nines_q`/`zeroes_q`. Остаётся удалить файл и инстанцирования из старых блоков при переходе Шага 1в. |
| REQ-REF-004 | Устранить гонку `Nines`/`Zeroes` и `state` в `DekatronCounter`. | Done **[v0.5]** | Старый счётчик заменён целиком. Гонки нет: состояния `INC`/`DEC` упразднены, а `zeroes_q`/`nines_q`/`tops_q` обновляются только при достоверном показании всех декад. **[v0.10]** Оставлены только нужные триггеры: `nines_q`/`zeroes_q[D-2:0]` для переноса, `zero_q`/`at_top_q` только при `TOP_LIMIT_MODE`, все без сброса; `tops_q` и `primed_q` удалены (doc/dekatron_counter_flop_reduction.md). |
| REQ-REF-005 | Уменьшить/убрать длинные комбинаторные цепочки Ready. | In Review **[v0.6]** | `ready` каждого блока собирается из состояния и готовности подчинённых. Глубину цепочки надо оценить после прогона синтеза. |
| REQ-REF-006 | Сократить лишние Impulse-прослойки, кроме необходимых для физической модели импульсов. | Done **[v0.5]** | Из четырёх прослоек осталась одна пара `Impulse`+`OneShot` — таймер окна записи. Шаг подаётся уровнем, нарезку делает `DekatronPhaseGen`; растяжка сбросов не нужна, её обеспечивает физическое реле времени. |
| REQ-REF-007 | Устранить рассогласование `Insn` и `IpLineReady` на 1 такт. | Done **[v0.6]** | Введён `insn_valid`; выборка считается завершённой только при `ip_ready & insn_valid`. |
| REQ-REF-008 | Определить поведение `RsLatch` при `S=1, R=1`. | **Неактуально [v0.5]** | `DekatronCarrySignal` и `RsLatch` в новой подсистеме не используются: перенос строится на защёлкнутых по `clk` значениях `nines_q`/`zeroes_q`, одновременный перенос в обе стороны невозможен по построению (`step_f` и `step_r` взаимоисключающи). Требование сохраняет силу только для старых блоков до их замены. |
| REQ-REF-009 | Убрать дублирование логики HardRst/Rst. | TODO | Medium. Пересекается с REQ-RTL-016 (`Dekatron.sv` дублирование по `EN_HARD_RST`). |
| REQ-REF-010 | Оптимизировать `BcdToBinEnc`, чтобы избежать избыточных умножителей. | Done **[v0.6]** | Снято банковой организацией памяти: линейный индекс не вычисляется, `BcdToBinEnc` из тракта памяти удалён вместе с умножителями. |
| REQ-REF-011 | Обеспечить детерминированное поведение всех FSM после сброса. | Done **[v0.6]** | Все новые автоматы имеют явную инициализацию всех регистров по `rst_n`. |
| REQ-REF-012 **[v0.3]** | Унифицировать стиль модулей `BcdToBin.v`/`BinToBcd.v` (Verilog-95) с остальным SystemVerilog-кодом. | TODO | Низкий приоритет, но снижает риск lint-проблем при масштабировании. |

## 12.5. Реализованный тракт Valid/Ready [v0.6]

Состав: `Ram` / `IpMemory` → `ApLine` / `IpLine` → `MachineCtrl`. Все интерфейсы — Valid/Ready.

### Память

| ID | Требование | Статус | Комментарий |
|---|---|---:|---|
| REQ-MEMV2-001 | Память использует тот же Valid/Ready, что и остальной тракт: `valid`, `ready`, `wr`, `addr`, `wr_data`, `rd_data`, `rd_valid`, `err`. | Done **[v0.7]** | **Заменяет решение v0.6 об APB.** APB гарантирует валидность данных только в такте `PREADY`, а требуется удержание до следующего чтения; кроме того две обязательные фазы дают два такта на обращение вместо одного. Единый протокол снимает и разнобой: линии перестали быть мастерами двух дисциплин сразу. |
| REQ-MEMV2-001a **[v0.7]** | Выход `rd_data` — регистр, хранящий значение последней затронутой ячейки до следующего обращения. Запись сквозная: после неё регистр содержит записанное значение. | Done | Регистр не добавлен ради удобства, а перенесён туда, где существует физически: у ферритовой памяти считанное значение оседает в усилителях считывания на время восстановительной записи. Благодаря этому вышестоящим блокам не нужна собственная копия ячейки. |
| REQ-MEMV2-001b **[v0.7]** | Соответствие выходного регистра нужному адресу отслеживает мастер; память знает лишь то, что регистр относится к последнему обращению. | Done | Разграничение ответственности: память не знает, сменился ли у мастера адрес. |
| REQ-MEMV2-002 | Число тактов чтения и записи параметризуется отдельно. | Done | У ферритовой памяти чтение разрушающее и требует восстановления, поэтому заведомо длиннее записи; единым параметром это не выразить. |
| REQ-MEMV2-002a **[v0.8]** | Обращение занимает не менее двух тактов: синхронное чтение добавляет такт поверх такта приёма запроса. | Done | Плата за синтезируемость. На `pi.bfk` это около 99 тысяч дополнительных тактов; избежать нельзя, асинхронной памяти нужного объёма в ПЛИС нет. |
| REQ-MEMV2-003 | Адрес принимается в BCD, по тетраде на декатрон; значения A..F не используются и поднимают `err`. | Done | Преобразование адреса не выполняется. |
| REQ-MEMV2-004 | Загрузчик занимает старший банк памяти программ и защищён от записи. | Done **[v0.6]** | Запись туда поднимает `err`. Прежде она уходила в RAM, а читался всегда ROM — ячейка становилась недостижимой. |
| REQ-MEMV2-007 **[v0.7]** | Наложение ПЗУ реализуется входами `ovl_hit`/`ovl_data` самой памяти, без отдельного автомата обращений и второго выходного регистра. | Done | Прежний мультиплексор на выходе `IpMemory` не нужен. |
| REQ-MEMV2-005 | Второй порт чтения предназначен только для индикации в эмуляторе и отключается параметром. | Done | В реальной машине его нет. |
| REQ-MEMV2-006 | Для FPGA-эмулятора требуется плоская реализация памяти с тем же интерфейсом. | **Отменено [v0.8]** | Не понадобилась: размер банка стал параметром, и одна банковая память служит и физической модели, и ПЛИС. Заменено на REQ-MEMV2-008..011. |
| REQ-MEMV2-008 **[v0.8]** | Размер банка задаётся параметром `BANK_DIGITS`: 2 — матрица 10×10 для физической машины и P&R, 4 — матрица 100×100 для ПЛИС. | Done | Рекурсия та же, меняется только уровень её остановки. При банке 10×10 эмулятор требует около 1300 блоков памяти вместо 80 по объёму: банк занимает 400 бит при ёмкости блока 10 240. |
| REQ-MEMV2-009 **[v0.8]** | Чтение внутри банка синхронное, выходной регистр стоит в самом банке. | Done | Условие работоспособности, а не оптимизация: блоки памяти ПЛИС умеют только синхронное чтение, при асинхронном массив раскладывается в 700 000 триггеров при бюджете около 40 000 логических элементов. Одного укрупнения банка недостаточно. |
| REQ-MEMV2-010 **[v0.8]** | Параметр `CELLS` ограничивает реально используемый объём; банки целиком выше границы не создаются. | Done | Иначе память данных разворачивается на все 100 000 ячеек адресного пространства при используемых 30 000 — три банка вместо десяти. |
| REQ-MEMV2-011 **[v0.8]** | Сведение тетрад в линейный индекс допускается ВНУТРИ банка и только там. | Done | В железе этой арифметики нет: тетрады идут прямо на дешифраторы строк и столбцов матрицы. Пересчёт существует лишь в поведенческой модели и реализации для ПЛИС и за пределы банка не выходит, поэтому REQ-REF-010 не нарушается. |

### Линия работы с данными

| ID | Требование | Статус | Комментарий |
|---|---|---:|---|
| REQ-APV2-001 | Чтение ленивое: смена адреса не вызывает обращения к памяти. Ячейка читается только когда её значение действительно нужно. | Done **[v0.7]** | **Заменяет упреждающее чтение из v0.6.** Замер на `pi.bfk`: 99 077 обращений против 155 625, на 36% меньше. На чистом перемещении указателя — одно обращение вместо сорока одного. |
| REQ-APV2-002 | Собственной копии ячейки блок не хранит: значение держит выходной регистр памяти. | Done **[v0.7]** | Состояния три бита — `lock`, `dirty`, `mem_here` — вместо двенадцатибитной копии. **[v0.10]** Осталось два: `dirty` удалён, флаг владения один — `lock` (REQ-APV2-003). Ламповый триггер дороже любого другого элемента библиотеки, поэтому перенос регистра в память, где он есть физически, важнее удобства. |
| REQ-APV2-003 | ~~Выгрузка счётчика в память выполняется только при `dirty`.~~ **[v0.10]** Флаг владения ячейкой один — MemLock (`lock`). Изменить данные без MemLock нельзя: счётчик сначала загружается. Сменить адрес (`>`, `<`, `CLRA`) или выполнить `CLRML` при MemLock нельзя без выгрузки, которая снимает MemLock. | Done **[v0.10]** | **[v0.10] Решение владельца:** `dirty` отличался от `lock` только после `STORE` и экономил одну повторную запись того же значения; ценой было то, что MemLock переживал шаг адреса (дефект v0.9, REQ-ML-005). Теперь после `STORE` следующий шаг адреса или `CLRML` пишет ячейку второй раз. bfpp `STORE` не порождает: на `pi.bfk` счёт обращений тот же (55 723 чтения + 43 354 записи = 99 077). |
| REQ-APV2-004 | Признак `mem_here` снимается при смене адреса и при физическом сбросе счётчиков. | Done | Иначе после сброса значение относилось бы к прежней ячейке. |
| REQ-APV2-005 | Блок выдаёт `data_zero_valid`; обеспечить достоверность признака перед проверкой цикла обязан вышестоящий блок. | Done **[v0.7]** | Прямое следствие ленивого чтения: признак нуля перестал быть всегда доступным. |
| REQ-APV2-006 | Операции задаются кодом, а не набором отдельных линий запроса. | Done | Подключены LOAD, STORE, CLRML, отсутствовавшие в прежнем ApLine, и добавлена внутренняя операция TEST. **[v0.10]** Кодом служит сама инструкция (REQ-APV2-008); TEST — это скобка BF, выданная в ApLine. |
| REQ-APV2-007 **[v0.10]** | Стробы исполнителям (`ap_valid`, `data_valid`, `mem_valid`, `set`, `set_zero`, `wr`) дешифруются из состояния автомата, а не хранятся в триггерах. Каждое состояние выдаёт одну операцию, когда готовы все исполнители, и покидает себя в такте её приёма; отдельных состояний ожидания нет. Окончание обращения к памяти — возврат `mem_ready`: `rd_data` к этому моменту достоверен. | In Review **[v0.10]** | 6 состояний вместо 9, 7 регистровых стробов убраны; ApLine 874 → 719 ламп. `ApLine_tb` дополнен STORE, CLRML, CLRA с выгрузкой, переходом 255 ↔ 0, счётом обращений к памяти и монитором «`mem_valid` без `mem_ready`» (прежний автомат нарушал его на первом обращении после сброса; на остальных он принимал за окончание чтения устаревший `rd_valid` предыдущего обращения и работал только благодаря `mem_ready` в условии `ready`). `mem_rd_valid` в ApLine больше не используется. |
| REQ-APV2-008 **[v0.10]** | Кодом операции ApLine служит инструкция `{insn_mode, insn}` без перекодирования: `0x0A`/`0x1A` — обнуление данных, `0x0B` — обнуление адреса, `0x12`/`0x13` — шаг данных, `0x14`/`0x15` — шаг адреса, `0x16`/`0x17` — TEST, `0x18` — COUT, `0x19` — CIN, `0x1B` — CLRML, `0x1C` — LOAD, `0x1D` — STORE. Направление шага — `insn[0]`. Дешифрирует ApLine; прочие коды — NOP, `MachineCtrl` их не выдаёт. | In Review **[v0.10]** | Порты `ap_op[3:0]`, `ap_dec` и шифратор в `MachineCtrl` убраны (часть R3, `doc/tube_count_reduction.md` §14). MachineCtrl 282 → 250 ламп, ApLine без изменений (675,5 → 676). `ApLine_tb` переведён на опкоды, добавлены оба кода обнуления и `]` как TEST; `MachineCtrl_tb` проверяет, что `{insn_mode, insn}` не меняется до `ap_ready` и что ApLine получает только операции над данными. **[v0.10]** С упреждающей выборкой (REQ-PERF-003) код операции — `{insn_mode, op_q}`: регистр `op_q` в `MachineCtrl` (порт `ap_op[4:0]`), потому что выход памяти программ меняется раньше, чем ApLine заканчивает операцию. Перекодирования по-прежнему нет, ApLine не изменён. |

### Линия выборки инструкций

| ID | Требование | Статус | Комментарий |
|---|---|---:|---|
| REQ-IPV2-001 | Промотка тела цикла выполняется внутри IpLine по признаку `loop_val_zero`. | Done | Декодер в этом больше не участвует. |
| REQ-IPV2-002 | Промотка останавливается НА парной скобке, а не за ней. | Done | Дальше её обрабатывает обычная выборка. |
| REQ-IPV2-003 | Счётчик вложенности самоочищается: к концу промотки он снова нуль. | Done | Проверено на вложенности до трёх уровней. |
| REQ-IPV2-004 | При переполнении счётчика вложенности промотка прерывается. | Done **[v0.6]** | Без прерывания машина зависает: парная скобка не найдётся, IP уходит за пределы памяти. |
| REQ-IPV2-005 | На уровне IpLine инструкции представлены ТОЛЬКО опкодами. | Done **[v0.6]** | Преобразование символ/опкод выполняет загрузчик программ. Модель для верификации обязана соблюдать это же ограничение. |
| REQ-IPV2-006 | Распознавание скобок не зависит от набора команд. | Done | Опкоды `0x6`/`0x7` одинаковы в Debug и Brainfuck ISA, поэтому достаточно одного детектора. |
| REQ-IPV2-007 **[v0.10]** | Стробы исполнителям (`ip_valid`, `loop_valid`, `mem_valid`, `set_zero`, `dec`, `wr`) дешифруются из состояния автомата и регистров `dir_q`/`insn_q` (**[v0.10]** `insn_q` позже убран, см. REQ-IPV2-008, — опкод с выхода памяти), а не хранятся в отдельных триггерах. Каждое состояние выдаёт одну операцию, когда готовы оба счётчика и память, и покидает себя в такте её приёма. Окончание чтения — возврат `mem_ready`; ждёт его только `S_FETCH_W`, защёлкивающий опкод. В память при загрузке пишется защёлкнутый `insn_q`, а не живой `insn_in`. | In Review **[v0.10]** | 11 состояний вместо 12, триггеров 51 → 40 (со счётчиками); IpLine 902 → 722 лампы, `equiv_opt` доказан. Прежний автомат защёлкивал опкод в такте приёма чтения по устаревшему `rd_valid` и с памятью по дисциплине `Ram` возвращал опкод предыдущей выборки; при загрузке писал в память `insn_in` через такт после рукопожатия. `IpLine_tb` переписан: память с задержкой и X до `ready`, загрузка с EOT, 400 выборок со случайным `loop_val_zero` против эталонной модели, переполнение и CLRL, CLRI, останов с ручными шагами, аппаратный сброс; проходит на Icarus. `mem_rd_valid` в IpLine больше не используется. |
| REQ-IPV2-008 **[v0.10]** | Собственного регистра опкода у IpLine нет: `insn` — выходной регистр памяти программ, который меняется только при обращении и держит последнюю прочитанную или записанную (сквозная запись) инструкцию. EOT в память не пишется; о нём сообщает признак `insn_eot`, снимаемый следующей операцией. При загрузке опкод пишется в память прямо с `insn_in` в такте рукопожатия, `insn_in_ready` поднимается только при свободной памяти и не зависит от `insn_in_valid`. Операция от `MachineCtrl` — один бит `clr`: 0 — следующая инструкция, 1 — CLRL/CLRI по `insn[0]`. | In Review **[v0.10]** | Часть R3 и R4 (`doc/tube_count_reduction.md` §14). Состояний 11 → 9 (`S_FETCH_W`, `S_WRITE` убраны), триггеров обвязки 22 → 17, IpLine 717,5 → 652 лампы, `equiv_opt` доказан; `looptest` в `IpLine_tb` на 13% быстрее. Условие для памяти: регистр `rd_data` не меняется без обращения — так устроены `Ram` (банковый `rd_q`, `digit_q`, `ovl_*_q` обновляются только при приёме) и ферритовая память. Запись в область загрузчика `Ram` отвергает, и `insn` тогда показывает ПЗУ, а не принятый опкод; такая запись и так ошибка. `IpLine_tb` проверяет `insn` после каждой записи, `insn_eot` после EOT и его снятие. **[v0.10]** С упреждающей выборкой (REQ-PERF-003) следующее обращение выдаётся вместе с операцией ApLine, поэтому опкод текущей инструкции снова защёлкивается — но в `MachineCtrl` (`op_q`), а не в IpLine. У IpLine регистра опкода по-прежнему нет; решение о промотке он принимает в такте приёма запроса, пока `insn` ещё текущий. Новый вход `ip_ahead`: при останове с заранее выбранной инструкцией IP не сдвигается. |

### Верхний автомат

| ID | Требование | Статус | Комментарий |
|---|---|---:|---|
| REQ-CTLV2-001 | Декодирование ведётся по паре `{insn_mode, insn}`. | Done | Опкоды 0xB..0xD в двух наборах означают разное. |
| REQ-CTLV2-002 | Все 32 комбинации набора команд покрыты явно или общей веткой. | Done | Сверено построчно с разделом 6. |
| REQ-CTLV2-003 | Сброс счётчиков запрашивается, а удерживается внешним реле времени. | Done | Машина не может держать импульс сама — для этого нужен счётчик на сотню тактов `hs_clk`. |
| REQ-CTLV2-004 | Набор команд после сброса: Debug ISA после аппаратного, Brainfuck после программного. | Done | Реализовано состоянием ожидания сброса, а не асинхронными ветками. |
| REQ-CTLV2-005 | Переполнение счётчика вложенности останавливает машину. | Done | Флага ошибки без остановки недостаточно. **[v0.10]** До v0.10 не выполнялось: присваивание `S_HALT` по переполнению перебивалось веткой `S_FETCH_W` того же `always_ff`, машина декодировала скобку и продолжала работу, а флаг ошибки, снятый CLRL в такте до сброса признака в IpLine, взводился снова и глушил следующее переполнение. Исправлено переписыванием (REQ-CTLV2-010): останов приоритетнее любого состояния, реакция по фронту `loop_overflow`; проверено `MachineCtrl_tb`. |
| REQ-CTLV2-006 | `EOT` вне режима загрузки исполняется как NOP. | Done **[v0.6]** | Вне загрузки у кода нет смысла. Зафиксировано явно, а не как следствие ветки по умолчанию. |
| REQ-CTLV2-007 **[v0.7]** | Перед скобкой автомат обеспечивает достоверность признака нуля операцией `TEST` к ApLine. | Done | Обращение к памяти происходит, только если значение не прочитано. Во время промотки тела цикла проверка не повторяется: решение принимается один раз, на входе в промотку. |
| REQ-CTLV2-008 **[v0.7]** | В Debug ISA скобки проверяют счётчик адреса, достоверный всегда, поэтому `TEST` там не выдаётся. | Done | Экономит обращение на каждой служебной скобке. |
| REQ-CTLV2-009 **[v0.7]** | Автомат реагирует на физические линии сброса, а не только на собственный запрос. | Done | **Дефект найден при разборе слоя эмулятора:** сброс с пульта автомат не видел, продолжал исполнять инструкцию и не менял набор команд. После аппаратного сброса машина осталась бы в Brainfuck ISA, и загрузчик бы не стартовал. |
| REQ-CTLV2-010 **[v0.10]** | Стробы исполнителям (`ip_valid`, `ap_valid`, `tx_vld`, `rx_rdy`, `soft_rst_req`/`hard_rst_req`, `bell`) дешифруются из состояния автомата, а коды операций (`ip_op`, `ap_op`, `ap_dec`) — из `{insn_mode, insn}`, а не хранятся в триггерах (**[v0.10]** позже коды убраны вовсе: ApLine получает `{insn_mode, insn}`, IpLine — бит `ip_clr`, REQ-APV2-008/REQ-IPV2-008; EOT при загрузке приходит признаком `insn_eot`). `valid` поднимается только при готовности обеих линий, рукопожатие — в том же такте. Ожиданий окончания операции два: `S_FETCH_W` (выборка) и общий `S_WAIT`. После сброса с `RunOnHardRst`/`RunOnSoftRst` автомат идёт из `S_RST_WAIT` прямо в `S_IDLE`. | In Review **[v0.10]** | 10 состояний вместо 15 (`S_BELL` был недостижим), триггеров 25 → 9, MachineCtrl 512 → 284,5 лампы, `equiv_opt` доказан. Коды `S_HALT`, `S_IDLE`, `S_DECODE`, `S_CIN_WAIT` сохранены для `DekatronPC_tb.cpp`. `MachineCtrl_tb` проходит на Icarus; на Hello World (`DekatronPC_tb`, загрузка через загрузчик) вывод и IP на каждом символе совпадают с прежним автоматом. Прежний автомат на один такт проходил `S_HALT` после сброса с автозапуском, и `DekatronPC_tb` (`TRY_PROGRAM`) принимал это за конец программы. **[v0.10]** Упреждающая выборка (REQ-PERF-003): в `S_EXEC` вместе с `ap_valid` выдаётся `ip_valid` (кроме TEST), `ip_clr` = `S_EXEC` & CLRL/CLRI; после `S_WAIT`/`S_COUT` автомат идёт прямо в `S_DECODE`. Код дешифрируется из `op_q`, который пишется в `S_FETCH_W` и в последнем такте инструкции. `DekatronPC_tb.cpp` считает инструкцию законченной и на входе в `S_DECODE` из `S_WAIT`/`S_COUT`. |

---

# 13. Эмулятор и периферия

## 13.1. Границы эмулятора

| ID | Требование | Статус | Комментарий |
|---|---|---:|---|
| REQ-EMU-001 | Слой `Emulator` находится выше `DekatronPC` и может использовать FPGA-удобства. | Done | Принято. |
| REQ-EMU-002 | Интерфейс `Emulator ↔ DekatronPC` должен быть зафиксирован. | Done **[v0.3]** | **Закрыто.** Полный список сигналов задокументирован по факту инстанцирования `DekatronPC` в `Emulator.sv:258` — см. Приложение B. Любое изменение этого списка теперь считается breaking change и требует ревизии этого документа. |
| REQ-EMU-003 | Эмулятор может подменять несобранные ламповые блоки. | Done | Принято. |

## 13.2. Дисплей, клавиатура, IN-12, MS6205

| ID | Требование | Статус | Комментарий |
|---|---|---:|---|
| REQ-EMU-DISP-001 | Поддержка MS6205, IN-12 и клавиатуры относится к эмулятору. | Done | Подтверждено (`io_key_display_block`, `Sequencer`, `MS6205`, `Keyboard`). |
| REQ-EMU-DISP-002 | Существующая логика отображения считается работоспособной. | Done | Нужны правки после рефакторинга handshake (см. REQ-EMU-DISP-003). |
| REQ-EMU-DISP-003 | После изменения handshake RTL дисплей должен быть адаптирован. | TODO | Обязательно потребуется — `MS6205`/`Sequencer` завязаны на текущие сигналы `IpAddress`/`ApAddress`/`RomData1` и т.п., которые переживут рефакторинг по контракту (Приложение B), но внутренняя синхронизация (`Clock_1ms`-сравнение) может потребовать проверки при смене протокола. |

## 13.3. UART

| ID | Требование | Статус | Комментарий |
|---|---|---:|---|
| REQ-UART-001 | UART рассматривается как внешняя периферия поверх параллельного интерфейса терминала. | Done | Принято. |
| REQ-UART-002 | UART не входит в аутентичное вычислительное ядро. | Done | Принято. |
| REQ-UART-003 | UART может быть реализован на внешнем микроконтроллере. | Done | Допускается. |
| REQ-UART-004 | В FPGA-эмуляторе UART сохраняется для отладки. | Done | Подтверждено (`uart_tx`/`uart_rx`, DATA_WIDTH=7, PARITY_CHECK=NONE, CLK_FREQ=1MHz, BAUD_RATE=110, STOP_BITS=1). |
| REQ-UART-005 | Скорость 110 бод является базовой для имеющегося терминала. | Done | Принято. |
| REQ-UART-006 | Скорость/параметры UART должны быть конфигурируемы тумблерами на FPGA-плате. | TODO | Подтверждено: сейчас параметры (`BAUD_RATE=110` и т.п.) захардкожены в инстанцировании, тумблеров нет. |
| REQ-UART-007 | FIFO на выходе UART — опциональное требование. | TODO | Не обязательно. |
| REQ-UART-008 **[v0.10]** | Приём символа с терминала — handshake Valid/Ready: передающая сторона держит `rx_data_bcd` до рукопожатия, входного регистра в ядре нет. | In Review **[v0.10]** | Сделано: `rx_q` (12 триггеров) из `ApLine` удалён, `data_in` при CIN берётся прямо с `rx_data_bcd`. У `DekatronPC` появился выход `rx_rdy` (Приложение B): его комбинационно выдаёт `MachineCtrl` в такте, когда `ApLine` закончил CIN (`S_AP_OP_W & ap_op==AP_CIN & ap_ready`, вне сброса); от `rx_vld` он не зависит. В `Emulator.sv` добавлен буфер приёма: байт UART/консула захватывается по фронту `vld` и держится до `rx_vld & rx_rdy`. `ApLine_tb` проверяет CIN с выгрузкой и обратным LOAD; буфер эмулятора проверен только линтом. |

## 13.4. Consul

| ID | Требование | Статус | Комментарий |
|---|---|---:|---|
| REQ-CONSUL-001 | Текущая поддержка Consul работает, но в целевой машине от него планируется отказ. | Done | Подтверждено рабочей реализацией: FSM из 5 состояний (`IDLE`→`WAIT`→`SET_CODE`→`SET_SYNC`→`SET_PAUSE`), таймингами `PERIOD_SYMBOL/PAUSE/NL` на 100 Гц, полной перекодировкой ASCII→консул. |
| REQ-CONSUL-002 | Consul не является обязательным для целевой системы. | Rejected | Может остаться как legacy в эмуляторе. |
| REQ-CONSUL-003 | Если Consul остаётся в тестах, его поведение должно быть задокументировано как legacy. | Done **[v0.3]** | Задокументировано в разделе 11 `1786044911450-emulator-functional-report.md` — считать закрытым. |

## 13.5. IO-шины и платы расширения

| ID | Требование | Статус | Комментарий |
|---|---|---:|---|
| REQ-IO-001 | Старая модель `io_register_block`, рассчитанная на низкие частоты, отвергается. | Rejected | Принято. При этом модуль по факту используется в эмуляторе (2 из 16 плат установлено) — считается временным решением до появления LVDS-плат. |
| REQ-IO-002 | Нужны новые внешние платы с LVDS-интерфейсом до FPGA. | TODO | Принято. |
| REQ-IO-003 | Одна такая плата должна позволять подключить целый блок машины. | TODO | Блочное подключение. |
| REQ-IO-004 | Ожидаемое количество таких плат: 2–3. | In Review | Оценка. |
| REQ-IO-005 | Новые IO-платы должны поддерживать частоты целевого блока, вплоть до 1 MHz. | TODO | Критично. |
| REQ-IO-006 | Необходимо зафиксировать распиновку и протокол LVDS-подключения блоков. | TODO | Пока отсутствует. |

---

# 14. Верификация

## 14.1. Текущее состояние

| ID | Требование | Статус | Комментарий |
|---|---|---:|---|
| REQ-VER-001 | Все текущие тесты считаются проходящими на момент подготовки рефакторинга. | Done | Подтверждено (таблица тестов PASSED в PDF §9.1.2: Dekatron, Counter, IpLine-LoopTest, ApLine, Hello World, Pi, ROT13). |
| REQ-VER-002 | C++ golden model существует, но поддерживает только базовый набор инструкций. | Done | Расширена до полного ISA **[v0.8]**, см. REQ-GM-001. |
| REQ-VER-003 | После рефакторинга RTL текущие тесты должны быть починены/адаптированы. | TODO | Обязательно, особенно с учётом перехода на Valid/Ready. |

## 14.2. Обязательные тесты

| ID | Требование | Статус | Комментарий |
|---|---|---:|---|
| REQ-VER-010 | Unit-тесты декатрона. | Done/TODO | Есть для текущего `Dekatron.sv`. Для `DekatronTubeV2` — полный список готов в TRS v0.1 §14 (UT-PERF-001..005, UT-DBG-001..005 и др.), но не реализован. |
| REQ-VER-011 | Unit-тесты декатронных счётчиков. | Done/TODO | Есть, но пересмотреть при переходе на `DekatronCounterV2`. |
| REQ-VER-012 | Тесты переноса между разрядами. | TODO | Особенно для 5-разрядных счётчиков. |
| REQ-VER-013 | Тесты IP-счётчика и Loop-поиска. | Done/TODO | Уже есть базово. |
| REQ-VER-014 | Тесты AP/Data-линии. | Done/TODO | Уже есть базово. |
| REQ-VER-015 | Тесты всех инструкций Debug ISA. | TODO | Особенно BELL, HRST/SRST (после сверки opcode, см. §6.2), CLRI/CLRA. |
| REQ-VER-016 | Тесты всех инструкций Brainfuck ISA. | TODO | Нужно расширить после доработок. |
| REQ-VER-017 | Тесты MemLock для последовательностей `+`, `-`, `>`, `<`, `.`, `,`, LOAD, STORE. | TODO | Критично. |
| REQ-VER-018 | Тесты SOT/EOT загрузки. | TODO | Особенно разные стартовые адреса. |
| REQ-VER-019 | Тесты bootloader. | TODO | Очистка памяти, HardRst, автозапуск. |
| REQ-VER-020 | Тесты невалидных BCD-состояний в симуляции. | TODO | Обязателен для RTL. |
| REQ-VER-021 | Тесты переполнения Loop Counter. | TODO | Должен быть hardware error. |
| REQ-VER-022 | Тесты undefined opcode. | TODO | Undefined должен вести себя как NOP. |
| REQ-VER-023 | Тесты 10-битного представления данных и банков памяти. | TODO | Новые требования. |
| REQ-VER-024 | Тесты производительности. | TODO | Отсутствуют. |
| REQ-VER-025 | Gate-level simulation после Yosys с задержками liberty. | In Progress **[v0.10]** | Требуется для physical flow. **[v0.10]** Первый шаг без задержек: `rtl/run/synth_sim.sh` гоняет Icarus-тесты на нетлистах Yosys (декатрон, `OneShot`/`Impulse`, `RstTimeRelay`, память — чёрные ящики с RTL-моделью). Все прогоны проходят, включая DekatronPC (исправлены начальное значение `RamGroup.digit_q` в модели памяти и выборка `IsHalted` по спаду `Clk` в тестбенче). CI `synth_sim` прошёл на Icarus 12 и стал обязательным (без `continue-on-error`). Задержки liberty ещё не учтены. Отчёт: `doc/synth_sim.md`. **[v0.10]** `synth_sim.sh -d` — тот же прогон с моделью декатрона на задержках (`DekatronTubeDelay`, чёрный ящик без `hsClk`), плюс тест `Pi` (pi.bfk на нетлисте DekatronPC); CI `synth_sim_delay`. См. `doc/dekatron_delay_model.md`. |
| REQ-VER-026 **[v0.3]** | Полный перенос тестового плана `DekatronTubeV2` (TRS v0.1 §14–16) в верификационный набор проекта — FSM coverage, функциональное покрытие (инкремент/декремент/запись/сброс для всех цифр 0–9, короткие/длинные импульсы, конфликты входов). | TODO | Зависит от решения REQ-DTV2-006 (мигрировать или вести параллельно). |
| REQ-VER-027 **[v0.3]** | Тесты на Valid/Ready-протокол: отсутствие потери транзакций, корректный backpressure между `IpLine`/`ApLine`/`DekatronCounter`. | In Progress **[v0.5]** | Для счётчика проверено на модели (back-to-back без снятия `ready`). Для верхних уровней — после Шага 1в. |
| REQ-VER-028 **[v0.5]** | Тестбенч `DekatronTubeV2` должен покрывать операции записи и сброса «встык», без снятия воздействия между ними. | TODO | Дефект REQ-DTV2-009 был найден вне тестбенча; регрессии на него пока нет. |
| REQ-VER-029 **[v0.5]** | Весь написанный RTL должен быть прогнан в Verilator и Icarus. | In Progress **[v0.7]** | Первый прогон выполнен и сразу дал результат: найдена комбинационная петля в `DekatronCounter`, из-за которой не работали `set`, `set_zero` и переходы через верхний предел. Подтверждает, что проверка на Python-модели не заменяет симулятор: нуль-задержечные петли в ней невидимы. Остальные блоки прогнать. **[v0.9]** В регрессии CI на Icarus — `DekatronPulseSender`, `DekatronCounter`, `Ram`, `IpMemory` (тесты переписаны под Valid/Ready); `ApLine`, `IpLine`, `MachineCtrl` — пока только Verilator-прогоны `run_tests.sh -t`. |
| REQ-VER-031 **[v0.7]** | Регрессия должна включать проверку на комбинационные петли: `UNOPTFLAT` в Verilator трактуется как ошибка, а не предупреждение. | TODO | Класс ошибок, который модель не ловит вовсе, а симулятор ловит сразу. Уже дал две находки: настоящую петлю через окно записи и ложную на векторе цепочки переноса. |
| REQ-VER-032 **[v0.7]** | Предупреждения `UNOPTFLAT` устраняются структурно, а не подавлением `lint_off`. | Done | Подавление в файле скрыло бы и настоящие петли, появившиеся в нём позже. Обе находки устранены переписыванием. |
| REQ-VER-033 **[v0.9]** | Набор Brainfuck-100 входит в регрессию: каждая программа на своём входе, сравнение вывода с эталонным интерпретатором. | TODO | Программы, входы и метрики — `bfutils/programs/bf100/`. Бесконечные генераторы прогоняются с ограничением числа шагов. |
| REQ-VER-034 **[v0.9]** | Регрессия сверяет с метриками набора максимум AP, максимум Loop и число шагов промотки, снятые с RTL. | TODO | Расхождение означает ошибку в промотке или ленивом чтении. |
| REQ-VER-030 **[v0.5]** | Тестбенчи `DekatronModule` и `DekatronCounter` (Valid/Ready, перенос, оба режима верхнего предела, физические линии сброса). | In Progress **[v0.9]** | cocotb-тест `DekatronCounter` (`tb/tests/test_dekatron_counter.py`) в CI: инкремент, декремент, перенос, `set`, `set_zero`, back-to-back, обнуление по `soft_rst`. Не покрыты: `DekatronModule` отдельно, `hard_rst`, режимы верхнего предела. |

## 14.3. Быстродействие [v0.9]

| ID | Требование | Статус | Комментарий |
|---|---|---:|---|
| REQ-PERF-001 **[v0.9]** | Время шага промотки (шаг IP + чтение опкода + при скобке шаг Loop) оптимизируется наравне со временем исполнения инструкции. | TODO | По набору Brainfuck-100 на одну исполненную инструкцию приходится в среднем 1,7 шага промотки. **[v0.10]** Измерено на helloworld: шаг промотки — 4 такта (S_IP, S_FETCH, ожидание памяти, S_SCAN_EVAL), промотка — 20,6% тактов программы; можно сократить до 3 тактов (`doc/cycle_profile_helloworld.md`, P2). |
| REQ-PERF-002 **[v0.9]** | Быстродействие измеряется прогоном набора Brainfuck-100 в Verilator: тактов на программу, тактов на инструкцию, тактов на шаг промотки. | In Progress **[v0.10]** | Заменяет оценки из исходного описания (200 тыс. операций в секунду в пике, 45 тыс. в среднем). **[v0.10]** Первое измерение — helloworld в Icarus, профиль по волновой диаграмме (`rtl/run/cycle_profile.py`): 401 инструкция за 5540 тактов, CPI 13,8; набор Brainfuck-100 в Verilator ещё не прогонялся (`doc/cycle_profile_helloworld.md`). **[v0.10]** С упреждающей выборкой (REQ-PERF-003): 401 инструкция за 4184 такта, CPI 10,4 (`doc/prefetch_p3.md`). |
| REQ-PERF-003 **[v0.10]** | Упреждающая выборка (P3): пока ApLine исполняет операцию, кроме скобки (TEST) и CIN, IpLine уже сдвигает IP и читает следующую инструкцию; по окончании операции `MachineCtrl` сразу дешифрирует её. Код текущей инструкции держит регистр `op_q` в `MachineCtrl`. При останове с заранее выбранной инструкцией IP стоит на ней (вход `ip_ahead` IpLine), после пуска она читается заново. | In Review | helloworld: 5540 → 4184 такта (−24,5 %), `+` 9 → 6, `+` после смены адреса 22 → 17, `<`/`>` → 6; program.bfk −21 % времени всего прогона. Теперь узкое место простой инструкции — сама выборка (4 такта). MachineCtrl +70 ламп. Проверено: `MachineCtrl_tb` (выборка вместе с операцией ровно у нужных опкодов, `ap_op` держится, останов в пошаговом режиме с повторным чтением), `IpLine_tb` (останов с `ip_ahead`), `ApLine_tb`, `DekatronPC_tb` (helloworld, program.bfk) на Icarus, Verilator `--lint-only`. Решение владельца. Отчёт: `doc/prefetch_p3.md`. |

## 14.4. Golden model

| ID | Требование | Статус | Комментарий |
|---|---|---:|---|
| REQ-GM-001 | C++ golden model должна поддерживать полный ISA. | Done **[v0.8]** | `bfutils/dpcrun`: все 32 комбинации `{mode, opcode}`, память программ хранит опкоды. Модель повторяет RTL, расхождения с TRS перечислены в `doc/dpcrun_golden_model.md` §4. 53 модульных теста в CI bfutils. |
| REQ-GM-002 | Golden model должна использоваться для пошагового сравнения с RTL. | In Review **[v0.10]** | `DekatronPC_tb.cpp` переведён на новую модель и новые состояния `MachineCtrl`. **[v0.10]** Прежде тест ничего не сравнивал: память программ без предзагрузки, Run терялся во время реле, `-s` не передавался. Теперь программа загружается по `InsnIn` после кнопки загрузки, EOT даёт Soft Reset с автозапуском; `run_tests.sh -t` гоняет `-s`: helloworld (400 инструкций) и program.bfk (5771) совпадают с моделью на каждом шаге, расхождение даёт код выхода 1. Отчёт: `doc/ci_sim_check.md`. **[v0.10]** `pi.bfk` совпадает с моделью на всех 221 386 шагах (с упреждающей выборкой, вывод `3.141`), модель собирается с пределом AP 99999, как в RTL. Отчёт: `doc/pi_step_check.md`. |
| REQ-GM-003 | Golden model должна поддерживать Debug ISA. | Done **[v0.8]** | Включая Debug-циклы по AP, BELL, CLRI/CLRA/CLRL, HRST/SRST. |
| REQ-GM-004 | Golden model должна поддерживать MemLock, SOT/EOT, reset behavior. | Done **[v0.8]** | MemLock с `lock`/`mem_here` (**[v0.10]** `dirty` удалён, как в RTL) и счётом обращений (99 077 на `pi.bfk`, совпадает с §1 v0.7), SOT/EOT с защитой ПЗУ, Hard/Soft Reset. |

---

# 15. Испытательный стенд

## 15.1. Назначение стенда

| ID | Требование | Статус | Комментарий |
|---|---|---:|---|
| REQ-STAND-001 | Стенд включается в данный документ. | Done | Принято. |
| REQ-STAND-002 | Основная функция стенда: питание модулей. | Done | Принято. |
| REQ-STAND-003 | Вторая функция: отладка ламповых и декатронных схем с подачей последовательностей. | Done | Принято. |
| REQ-STAND-004 | Стенд должен позволять измерять параметры для формирования liberty. | Done | Принято. |
| REQ-STAND-005 | Стенд должен позволять отрабатывать схемотехнику до установки в полную машину. | Done | Принято. |

## 15.2. Питание

| ID | Требование | Статус | Комментарий |
|---|---|---:|---|
| REQ-PWR-001 | Источник накала 6.3 В, не менее 6 А. | Done | Базовое требование. |
| REQ-PWR-002 | Токовый шунт до 6 А с выводом на байонет. | TODO | Нужно реализовать. |
| REQ-PWR-003 | Проволочный резистор на 50 Вт с байпасом. | TODO | Нужно реализовать. |
| REQ-PWR-004 | Регулируемое анодное питание 50–200 В, 0.1 А. | Done | Базовое требование. |
| REQ-PWR-005 | Источник питания декатрона 300–500 В, 20 мА. | Done | Базовое требование, согласуется с PDF (финальная схема +500В). |
| REQ-PWR-006 | Напряжение смещения −20…−70 В. | Done | Базовое требование. |
| REQ-PWR-007 | Источники +10 В и −20 В, 0.2 А каждый для питания логики. | Done | Базовое требование. |
| REQ-PWR-008 | Все регулируемые напряжения должны отображаться на вольт-амперметрах. | Done | Желательно стрелочные, но не обязательно. |

## 15.3. Генератор последовательностей

| ID | Требование | Статус | Комментарий |
|---|---|---:|---|
| REQ-GEN-001 | Встроенный генератор должен покрывать базовые нужды отладки до 1 МГц. | Done | Принято. |
| REQ-GEN-002 | Если требуется частота выше 1 МГц, используется внешний генератор. | Done | Принято. |
| REQ-GEN-003 | Фронты встроенного генератора: не хуже 50 нс. | Done | Принято. |
| REQ-GEN-004 | Идеальная цель по фронтам: около 10 нс. | Done | Принято как цель. |
| REQ-GEN-005 | Должны быть делители на 2, 4, 8, 16, 32. | Done | Исходное требование. |
| REQ-GEN-006 | Должна быть цепочка импульсов длиной до 6–8. | Done | Для setup/hold. |
| REQ-GEN-007 | Должна быть возможность ручной подачи сигналов кнопками. | Done | Исходное требование. |
| REQ-GEN-008 | Должна быть возможность отключить встроенный генератор и подключить внешний. | Done | Исходное требование. |

## 15.4. Измерения и точки доступа

| ID | Требование | Статус | Комментарий |
|---|---|---:|---|
| REQ-STAND-IO-001 | Основные сигналы должны выводиться на байонеты. | Done | Исходное требование. |
| REQ-STAND-IO-002 | Синхросигнал с генератора должен выводиться отдельно. | Done | Исходное требование. |
| REQ-STAND-IO-003 | Нужно 2–4 выхода на осциллограф/логический анализатор. | Done | Исходное требование. |
| REQ-STAND-IO-004 | Нужны банановые точки напряжений питания. | Done | Исходное требование. |
| REQ-STAND-IO-005 | Три слота для установки плат поперёк сетапа. | Done | Исходное требование. |
| REQ-STAND-IO-006 | Измерение задержек выполняется вручную осциллографом. | Done | Принято. |

## 15.5. Безопасность и охлаждение

| ID | Требование | Статус | Комментарий |
|---|---|---:|---|
| REQ-SAFE-001 | Высоковольтные цепи должны быть изолированы. | Done | Обязательное. |
| REQ-SAFE-002 | Необходима индикация наличия высокого напряжения. | Done | Обязательное. |
| REQ-SAFE-003 | Необходима безопасная схема заземления. | Done | Обязательное. |
| REQ-SAFE-004 | В HV-цепях нужны разрядные резисторы/цепочки. | TODO | Желательно зафиксировать. |
| REQ-SAFE-005 | TO-220 фланцы в силовых каналах стенда должны быть изолированы от общего радиатора. | Done | Уже отмечено в стенде. |
| REQ-SAFE-006 | Активное охлаждение требует расчёта. | TODO | Нужно выполнить, см. PDF §8.3.1 (openFoam + натурные эксперименты). |
| REQ-SAFE-007 | Нужно определить допустимую температуру воздуха. | In Review | В материалах упоминалось 65°C. |
| REQ-SAFE-008 | Нужно определить минимальный воздушный поток. | In Review | В PDF даны конкретные цифры: 3× вентилятора NMB 4710PS-23T-B20 → 5.8 м³/мин (350 м³/ч), для лампы ГУ-5 достаточно 400 м³/ч — т.е. текущая конфигурация чуть ниже расчётной цели. Нужно уточнить для реальной ламповой нагрузки блока (не ГУ-5). |

---

# 16. Ламповые модули

| ID | Требование | Статус | Комментарий |
|---|---|---:|---|
| REQ-MOD-001 | Финальный разъём модуля логики: edge connector 2×36. | Done | Принято, согласуется с PDF (модуль 140×140мм, разъём 3×36 либо ГРПМШ-31 — уточнено до 2×36 edge connector). |
| REQ-MOD-002 | ГРПМШ-31 может использоваться только в специальных местах, если потребуется. | Done | Не основной разъём. |
| REQ-MOD-003 | Библиотека логических элементов близка к финальной, но не финальна. | Done | Текущий список: BUF_N16, NOT_N16, OR2_N16, OR4_N16, NOR2_N16, NOR4_N16, AOI21_J2N16, AOI22_J2, NAND_J2, LATCH_J2N16, DFF_J2N16. |
| REQ-MOD-004 | Для каждой ячейки должны быть измерены задержки, fan-out и потребление. | TODO | Критично для liberty. |
| REQ-MOD-005 | Должны быть разработаны платы: ИЛИ-НЕ, 2И-НЕ/ИЛИ-И-НЕ, D-триггер, управление декатроном, плата декатрона, усилители записи/чтения. | TODO | По roadmap. |
| REQ-MOD-006 | Схема сброса декатрона должна быть вынесена за пределы декатронной платы до выбора финального варианта. | Done | Есть в материалах (PDF §5.1). |
| REQ-MOD-007 | Нужно определить вариант сброса: отрицательный импульс на катод или отключение остальных катодов. | TODO | Экспериментально. **[v0.3]** TRS v0.1 уже де-факто выбрала подход «отключение остальных катодов» (изоляция главных катодов при записи/сбросе, §3.4) как модель поведения — но это выбор для RTL-модели, не подтверждённый экспериментом на реальном А110. Физический выбор варианта остаётся открытым. |
| REQ-MOD-008 **[v0.3]** | RTL-примитивы (`Impulse`, `OneShot`, `RsLatch`, `Compare`, `BCDCounterX1`, `Register`, mux-библиотека) должны быть сопоставлены с целевыми ламповыми ячейками (REQ-MOD-003) для оценки, какие примитивы уже имеют прямой ламповый аналог, а какие нужно спроектировать отдельно. | TODO | Пример: `RsLatch` → `LATCH_J2N16`, `Register`/`DFF`-подобное → `DFF_J2N16`. Не сделано. |
| REQ-MOD-009 **[v0.10]** | Бюджет: вся машина — не более ~~1500~~ **1200** ламп **[v0.10]**. | TODO | **[v0.10]** Владелец снизил бюджет с 1500 до 1200 на всю машину. Входят ли в бюджет декатроны, уточнить у владельца. Сейчас синтез считает только IpLine + ApLine + MachineCtrl со счётчиками — 1578 (`run_tests.sh -s`, после R1–R4, R6, R7: переписка автоматов ApLine/IpLine/MachineCtrl, вывод со счётчика данных, однократная дешифрация, без `insn_q`; при старом скрипте синтеза было 2636); память, реле сброса и пульт не входят. Только эти три блока на 378 ламп (24 %) выше бюджета всей машины. Оставшиеся идеи (R5, R11) дают 10–30 ламп; нужен новый подход. Сводка и статус идей: `doc/tube_count_reduction.md` (раздел Status, §5, §6). **[v0.10]** Упреждающая выборка (REQ-PERF-003) добавляет в MachineCtrl ≈ 70 ламп (248 → 319, среднее по трём seed `&deepsyn`): 5 триггеров (35) и дешифрация (`doc/prefetch_p3.md` §5). **[v0.10]** T4–T6 (владелец, 2026-10-08): один формирователь импульсов на счётчик с ключом J2 в декаде (REQ-PULSE-007), счётчики вложенности и AP без записи — один триггер занятости вместо автомата, коды состояний MachineCtrl подобраны перебором: три блока **1377** ламп в среднем по трём seed (1437 → 1377, −60; `doc/tube_count_reduction.md` §17.7). Диодные кодеки (T2) отклонены (REQ-AUTH-002), защёлки (T3) и волновой перенос (T8) отложены, P3 остаётся (T7). **[v0.10]** Двоичное кодирование состояний автоматов DekatronCounter, IpLine и ApLine (`fsm_encoding = "binary"`; Yosys иначе перекодировал их в one-hot): три блока 1669,5 → **1450,5** лампы (по трём seed ≈ 1656 → 1437, −219), триггеров 80 → 64 (`doc/tube_count_reduction.md` §17). Следующие идеи там же: диодные кодеки по REQ-AUTH-002 (≈ −160), защёлки для флагов переноса (≈ −75). |
| REQ-MOD-010 **[v0.10]** | Триггер (`DFF`, `DFFSR`, `DFFSR_n`, `LATCH`) имеет бесплатный инверсный выход `QN`; синтез обязан его использовать. Цена триггера — 7 ламп, накал 2 А при 6,3 В. | Done | `QN` в `vtube_cells.lib`, проход `rtl/run/qn_absorb.py` в `synt_dpc.tcl`. |
| REQ-MOD-011 **[v0.10]** | Логика, которой управляют только панельные тумблеры (EN/MUX от тумблера), строится на реле 2CO (две перекидные группы), а не на лампах: у реле нет накала. Обмотку реле питает только тумблер; в тактируемой и вообще быстрой логике реле запрещены. Реле ставится только там, где оно действительно убирает лампы. | In Review | Ячейка `RELAY_2CO` в `vtube_cells.lib` (площадь 0, без функции — ABC её не использует), модули `RelayMux`/`RelayEn` с `keep_hierarchy` в `rtl/Logic/Relay.sv`. В `MachineCtrl`: `BellOnHALT`/`BellOnCIN`/`BellOnError` — три `RelayEn`, выбор `RunOnSoftRst`/`RunOnHardRst` — `RelayMux` на 2 реле; итого 5 реле. `EchoMode` и `SoftRstOnEOT` оставлены на лампах: реле там лампу не экономит (замер по 8 вариантам × 7 зёрен ABC). `dpc_stat.py` печатает лампы и реле. Отчёт: `doc/tube_count_reduction.md` §15. |

---

# 17. Требования к P&R-инструменту

P&R разрабатывается отдельно, но из этого документа получает следующие требования.

| ID | Требование | Статус | Комментарий |
|---|---|---:|---|
| REQ-PR-001 | P&R должен принимать структурный Verilog-нетлист после синтеза. | In Progress **[v0.10]** | Базовый вход. **[v0.10]** Нетлист **иерархический** (решение владельца 2026-10-09): `synt_dpc.tcl` не делает `flatten`, подмодули становятся платами (REQ-PR-011). Парсер webui пока понимает только плоский нетлист и на иерархии молча склеивает цепи — `doc/webui_review.md` F1 (ветка `webui`, PR #28). |
| REQ-PR-002 | P&R должен принимать liberty-файл с именами ячеек и портов. | Done **[v0.10]** | Базовый вход. **[v0.10]** Парсер webui читает все 27 ячеек `rtl/vtube/vtube_cells.lib`, включая `QN` и `tubes`; группа `relays` пока игнорируется. |
| REQ-PR-003 | P&R должен поддерживать пользовательские элементы-заглушки, например DEKATRON. | Done **[v0.10]** | Важно для ранних этапов. **[v0.10]** Вкладка Elements. Базовые элементы = ячейки liberty плюс добавленные вручную (`Impulse`, `OneShot`, `RstTimeRelay`, `DekatronTubeV2`), REQ-PR-016. |
| REQ-PR-004 | P&R должен поддерживать KiCad netlist для модулей. | TODO | Для маппинга пинов. |
| REQ-PR-005 | P&R должен поддерживать модуль с edge connector 2×36. | Done | Принято. |
| REQ-PR-006 | Приоритет: ручное размещение и ручная трассировка. | Done | Исходный приоритет. |
| REQ-PR-007 | Автоматическое размещение/трассировка — поздние фазы. | Done | Исходный приоритет. |
| REQ-PR-008 | P&R должен экспортировать таблицы соединений для монтажа. | TODO | Важно. |
| REQ-PR-009 | P&R должен учитывать будущие liberty-параметры: задержки, fan-out, нагрузку. | TODO | После измерений. |
| REQ-PR-010 | P&R должен позволять работать с блоками: IpLine, ApLine, MachineCtrl, память, декатронные узлы. | In Progress **[v0.10]** | Архитектурно. **[v0.10]** Блоки IpLine, ApLine, MachineCtrl — по ящикам (REQ-PR-012); ферритовая память — вне P&R (REQ-PR-018); декатронный узел — одна плата (REQ-PR-011). |
| REQ-PR-011 **[v0.10]** | Нетлист для P&R остаётся иерархическим. Подмодуль, которому назначен тип платы (например, `DekatronModule` — одна плата), размещается как один модуль; остальные подмодули разворачиваются до базовых элементов. | TODO | Решение владельца 2026-10-09 (Q3, Q7). |
| REQ-PR-012 **[v0.10]** | Блок P&R = функциональный блок (IpLine, ApLine, MachineCtrl) = ящик машины из 3–5 корзин. Ряд в P&R = корзина: 420 мм, сетка 12 мм, трансформатор по центру шириной 72 + 12·K мм. | In Progress | Решение владельца 2026-10-09 (Q2, Q4, Q8). В webui модель блока и ряда уже такая; ширина трансформатора пока задаётся 70–100 мм. |
| REQ-PR-013 **[v0.10]** | Трассируется блок вместе с разъёмами на другие блоки. Разъёмов на блоке может быть несколько; рассматривается кабель SCSI HD-68, разъёмы стоят сверху страницы блока. Контакты разъёма — концы трасс. | TODO | Решение владельца 2026-10-09 (Q1, Q9). |
| REQ-PR-014 **[v0.10]** | Все три блока можно вести в одном проекте и разводить весь компьютер сразу; межблочные цепи идут по кабелям между разъёмами блоков. | TODO | Решение владельца 2026-10-09 (Q1). Нужен REQ-PR-019 на стороне RTL. |
| REQ-PR-015 **[v0.10]** | На соединительной плате корзины — только питание, все сигналы — проводами. Провод в P&R — либо связь «вывод — вывод», либо проложенный провод из горизонтальных и вертикальных участков. Цепи питания не трассируются. Для отдельных узлов (декатрон + запись + считывание) допускаются небольшие соединительные платы. | TODO | Решение владельца 2026-10-09 (Q10). Вид провода в модели webui уже совпадает. |
| REQ-PR-016 **[v0.10]** | Фиксированного набора плат модулей нет. Модуль описывается набором базовых элементов: какой элемент на каких выводах стоит и сколько их. | Done | Решение владельца 2026-10-09 (Q11). Совпадает с моделью слотов webui 0.3.0. |
| REQ-PR-017 **[v0.10]** | Логика на реле (`RelayMux`/`RelayEn`) стоит на отдельных платах модулей. | Assumption | Решение владельца 2026-10-09 (Q5): от реле, возможно, откажемся — экономия 5 ламп даёт 5 реле и новый тип модуля. |
| REQ-PR-018 **[v0.10]** | Ферритовая память — отдельный блок вне P&R. | Done | Решение владельца 2026-10-09 (Q6). |
| REQ-PR-019 **[v0.10]** | RTL: для межблочных соединений сделать структуры из проводов — по структуре на каждый разъём блока, чтобы порты IpLine, ApLine и MachineCtrl в нетлисте группировались по разъёмам. | TODO | Решение владельца 2026-10-09 (Q1). Вход для REQ-PR-013/014. |

---

# 18. Открытые решения

| ID | Вопрос | Статус | Комментарий |
|---|---|---:|---|
| OPEN-001 | AP limit: `29999` или `99999`. | In Review | Критерий зафиксирован (раздел 1): 99999 экономит ~20 ламп, но требует больше памяти и переноса. Решение — непосредственно перед фиксацией RTL. |
| OPEN-002 | Точное поведение `CLRD` относительно MemLock. | **Closed [v0.6]** | Решено проверкой: `CLRD` выставляет MemLock. Прежнее допущение опровергнуто — без этого `[-]` не обнуляет ячейку. См. REQ-ML-009. |
| OPEN-003 | Должен ли `SOT` автоматически переключать ISA в текущем RTL. | Assumption **[v0.3]** | Рабочее допущение: оставить как есть в RTL. Требует подтверждения. |
| OPEN-004 | Точное завершение bootloader. | In Review | Soft Reset / Halt / переход к программе. |
| OPEN-005 | Физическая распиновка и протокол LVDS-плат. | TODO | Нужно для гибридной эмуляции. |
| OPEN-006 | Охлаждение: воздушный поток и температура. | TODO | Нужен расчёт, ориентир — данные PDF §8.3.1. |
| OPEN-007 | BELL: длительность, снятие, подтверждение оператора. | TODO | Нужно определить поведение. |
| OPEN-008 | Мигрировать текущий RTL декатрона на `DekatronTubeV2`/`DekatronCounterV2`, или вести параллельно? | **Closed [v0.4]** | Решено: последовательная миграция. Сначала `DekatronTubeV2` реализуется и полностью верифицируется в изоляции (без handshake — он физически невозможен на этом уровне), затем вокруг неё пишется `DekatronCounterV2` с Valid/Ready, и только потом рефакторинг идёт выше (`IpLine`/`ApLine`). См. REQ-DTV2-006/007, раздел 20 Фаза 1. |
| OPEN-009 **[v0.3]** | Opcode `0xC`/`0xD` в Debug ISA — сверить `HRST`/`SRST` построчно между `DekatronPC_TRS_v_02.md` и фактическим `insnValues.sv`; в частности, существует ли отдельный opcode-триггер Soft Reset или SRST только внешний сигнал. | TODO | См. раздел 6.2, примечание после таблицы Debug ISA. |
| OPEN-010 **[v0.3]** | `RsLatch` при `S=R=1` в `DekatronCarrySignal`. | **Closed [v0.5]** | Снят: узел не используется в новой подсистеме, см. REQ-REF-008. |
| OPEN-012 **[v0.5]** | `TOP_LIMIT_MODE` и `HARD_RST_D_CNT` взаимоисключающи: обе используют линию `resetN` декатрона, но с разной целевой позицией (цифра `TOP_VALUE` против девятки). По текущей таблице инстансов конфликта нет (IP — предустановка, AP и Data — верхний предел), поэтому поставлен `$error`. Нужно ли где-то сочетание, требующее второй линии сброса? | TODO | Влияет на число линий сброса и на количество ламп в обвязке декады. |
| OPEN-013 **[v0.5]** | Значения `GUIDE_STEP_HS`, `FALL_STEP_HS`, `WRITE_MIN_HS`, `RESET_MIN_HS` и нарезка `PHASE1_HS`/`PHASE2_HS` пока оценочные. Требуется калибровка на экспериментальной декатронной ячейке. | TODO | Прямо влияет на достижимую тактовую частоту: при неверном соотношении фаз и времени сваливания счёт срывается полностью (проверено на модели). Задача Фазы 2. **[v0.10]** Нарезка по умолчанию 3/3/4: окно сваливания обязано быть строго больше `FALL_STEP_HS`, иначе шаг не укладывается в такт `clk`. |
| OPEN-015 **[v0.6]** | Банковая память не синтезируется для ПЛИС. | **Closed [v0.8]** | Причин оказалось две: дробление на мелкие банки и асинхронное чтение. Решено параметром `BANK_DIGITS` и переносом выходного регистра внутрь банка. Вторая реализация не понадобилась: 80 блоков памяти вместо 1300. |
| OPEN-016 **[v0.6]** | Упреждающее чтение против ленивого. | **Closed [v0.7]** | Измерено на Hello World, ROT13, MOV и `pi.bfk`. Ленивое чтение выигрывает 36% обращений на Pi, где перемещения указателя составляют половину кода. Выбрано ленивое, копия ячейки перенесена в выходной регистр памяти. |
| OPEN-017 **[v0.6]** | Операция `AP_COUT` определена, но не используется. | In Review **[v0.10]** | Было закрыто в v0.7 («теперь используется»), но в `MachineCtrl.sv` опкод `5'h18` поднимает `tx_vld`, не выдавая `AP_COUT`. После `>` выводится предыдущая ячейка: Hello World печатается как `Hello WWrld!!` (подтверждено в Icarus). См. `doc/dpcrun_golden_model.md` §5.1. **[v0.10]** Решение владельца: вывод всегда со счётчика данных. `MachineCtrl` выдаёт `AP_COUT` и поднимает `tx_vld` по его окончании; `AP_COUT` без MemLock загружает ячейку в счётчик, MemLock не меняет; в ApLine `tx_data_bcd = data_out`. Hello World печатается верно. Golden model приведена к тому же: COUT без MemLock грузит ячейку в счётчик, `txData()` = счётчик данных (55 тестов bfutils проходят). |
| OPEN-018 **[v0.7]** | Инвариант «между операциями к памяти программ не обращается никто, кроме IpLine» держится на том, что у каждой памяти единственный мастер. Стоит ли закрепить его assertion или структурно? | TODO | Сейчас соблюдается по построению, но нигде не проверяется. |
| OPEN-014 **[v0.5]** | Ограничение темпа: непрерывный счёт возможен только если окно сваливания внутри такта вмещает `FALL_STEP_HS`. Нужно подтвердить на железе, что при 1 МГц реальный декатрон А110 успевает отработать все три интервала. | TODO | От этого зависит, останется ли быстродействие 1 МГц или придётся вернуться к счёту через такт (500 кГц). |
| OPEN-011 **[v0.3]** | Панельные тумблеры `RunOnHardRst`, `RunOnSoftRst`, `SoftRstOnEOT`, `EchoMode` сейчас захардкожены в Emulator — нужны ли они как физические тумблеры в ближайшем релизе, или это можно отложить до этапа реальной панели управления? | TODO | Влияет на объём Фазы 2/3 плана работ. |

---

# 19. Чек-лист готовности

## 19.1. Архитектура и ISA

- [x] IP = 100k, 5 декатронов.
- [x] Loop = 2 декатрона, 0–99. **[v0.9]**
- [x] Конфигурация 5 + 2 + 5 + 3 = 15 декатронов проверена на наборе Brainfuck-100. **[v0.9]**
- [x] `LOOP_DEKATRON_NUM = 2` в `rtl/parameters.sv`; `LoopCount` в интерфейсе эмулятора сужается до 8 бит (ширина выводится из параметра). **[v0.9]** **[v0.10]**
- [x] AP физически 5 декатронов.
- [x] Brainfuck AP limit = 30k как базовый.
- [ ] Финальный выбор AP `29999` vs `99999` (откладывается до RTL freeze).
- [x] Data Counter = 0–255.
- [x] Data Counter выдаёт 12-bit BCD.
- [x] Data RAM использует младшие 10 бит (по контракту; физически RAM пока 8-бит — см. REQ-MEM-DATA-002).
- [x] Debug-циклы смотрят AP.
- [x] Brainfuck-циклы смотрят Data.
- [x] Реализовать BELL. **[v0.6]**
- [x] Undefined opcode работает как NOP.
- [x] Сверены `0xC`/`0xD` как HRST/SRST, обе подключены. **[v0.6]**
- [x] Поведение CLRD относительно MemLock подтверждено проверкой: выставляет MemLock. **[v0.6]**
- [ ] Подтвердить поведение SOT относительно переключения ISA (сейчас — допущение).

## 19.2. Память

- [x] Программа: 100 000 × 4 бит.
- [x] Программа: 1000 банков 10×10 для физической машины (`BANK_DIGITS=2`). **[v0.6]**
- [x] Для эмулятора та же память с банком 100×100 (`BANK_DIGITS=4`). **[v0.8]**
- [x] Bootloader: последние 100 инструкций, ровно один банк.
- [x] Bootloader: адреса 99900–99999, защищён от записи.
- [x] Данные: 30 000 ячеек как базовый режим.
- [x] Данные: 300 банков 10×10 для физической машины. **[v0.6]**
- [x] Data RAM использует 10-битное кодирование `{hundreds[1:0], tens, ones}`. **[v0.6]**
- [x] Адресная арифметика устранена, `BcdToBinEnc` из тракта памяти удалён. **[v0.6]**
- [x] Память имеет раздельные тайминги чтения и записи. **[v0.6]**
- [x] Память использует Valid/Ready с регистровым выходом и сквозной записью. **[v0.7]**
- [x] Наложение ПЗУ загрузчика встроено в память входами `ovl_*`. **[v0.7]**
- [x] Память синтезируема для ПЛИС: параметр размера банка и синхронное чтение. **[v0.8]**
- [x] Банки выше используемого объёма не создаются. **[v0.8]**
- [ ] Оценка 100k data RAM для AP=99999.

## 19.3. RTL — подсистема декатрона — **[v0.5] реализована, требует прогона в симуляторе**

- [x] Решение принято: последовательная миграция (OPEN-008 закрыт).
- [x] `DekatronTubeV2` реализована — кольцевая модель на 30 электродов.
- [x] Временные характеристики параметризованы (`GUIDE_STEP_HS`, `FALL_STEP_HS`, `WRITE_MIN_HS`, `RESET_MIN_HS`, `GUIDE_MAX_HS`).
- [x] `DekatronPhaseGen` — нарезка такта на трети, счёт каждый такт.
- [x] `DekatronPulseSender` — комбинационная разводка фаз, общий генератор на счётчик; **[v0.10]** сам формирователь тоже один на счётчик, в декаде — два ключа `GUIDE_EN_J2`, по лампе J2 на подкатод (REQ-PULSE-007).
- [x] `DekatronModule` — вентильные кодеки, `Valid`, `TopPin`, выделенные линии сброса.
- [x] `DekatronCounter` — Valid/Ready, однотактный инкремент, физические линии сброса.
- [x] Маскирование выхода в `X` устранено.
- [x] Дефект операций «встык» найден и исправлен.
- [ ] **Прогнать всё в Verilator и Icarus** (REQ-VER-029) — не выполнено, симуляторы были недоступны.
- [ ] Дописать тестбенч на операции «встык» (REQ-VER-028).
- [ ] Написать тестбенчи `DekatronModule` и `DekatronCounter` (REQ-VER-030).
- [ ] Откалибровать тайминги на экспериментальной ячейке (OPEN-013).

## 19.4. RTL — ядро (Valid/Ready выше счётчика) — **[v0.6] выполнено**

- [x] `DekatronCounter` — первый уровень с Valid/Ready.
- [x] Гонка `Nines`/`Zeroes`/`state` устранена заменой счётчика целиком.
- [x] Лишние Impulse-прослойки убраны.
- [x] Память переведена на банковую организацию. **[v0.6]**
- [x] Память переведена на Valid/Ready с регистровым выходом; APB отменён. **[v0.7]**
- [x] `ApLine` переведён на Valid/Ready. **[v0.6]**
- [x] `ApLine` переведён на ленивое чтение, копия ячейки убрана. **[v0.7]**
- [x] `MachineCtrl` реагирует на сброс с пульта. **[v0.7]**
- [x] `IpLine` переведён на Valid/Ready, промотка целиком внутри блока. **[v0.6]**
- [x] `MachineCtrl` переведён на Valid/Ready, логика циклов из декодера удалена. **[v0.6]**
- [x] `ApLine`, `IpLine`, `MachineCtrl`: стробы дешифруются из состояния, пары OP/WAIT слиты (REQ-APV2-007, REQ-IPV2-007, REQ-CTLV2-010). **[v0.10]**
- [x] Инструкция декодируется один раз, регистр опкода в IpLine убран (REQ-APV2-008, REQ-IPV2-008). **[v0.10]**
- [x] Упреждающая выборка следующей инструкции во время операции ApLine, регистр опкода `op_q` в `MachineCtrl` (REQ-PERF-003). **[v0.10]**
- [x] Асинхронные `Rst_n`/`HardRst_n` убраны из тракта, сброс стал физической линией. **[v0.6]**
- [x] Подключены BELL, CLRL, CLRI, HRST, SRST, CLRD, CLRML, LOAD, STORE. **[v0.6]**
- [x] Устранено зависание при переполнении вложенности. **[v0.6]**
- [x] Устранён дублирующийся `InsnLoopDetector`. **[v0.6]**
- [ ] Удалить из дерева исходников старые `Dekatron.sv`, `DekatronPulseAllow`, `DekatronCarrySignal`, `RsLatch`, прежние `RAM`/`IpMemory`/`ApLine`/`IpLine`/`InsnDecoder`.
- [ ] Оценить глубину комбинаторных цепочек `ready` после синтеза (REQ-REF-005).
- [ ] Унифицировать `BcdToBin.v`/`BinToBcd.v` под SystemVerilog.
- [ ] Подготовить RTL к синтезу в физическую библиотеку.
- [ ] Провести lint-чистку.

## 19.5. Эмулятор

- [x] Клавиатура.
- [x] MS6205.
- [x] IN-12.
- [x] UART.
- [ ] UART-тумблеры скорости (сейчас захардкожено 110 бод).
- [ ] FIFO UART — опционально.
- [x] Consul работает в эмуляторе.
- [x] Consul исключается из целевой системы.
- [x] Интерфейс Emulator↔DekatronPC зафиксирован (Приложение B). **[v0.3, закрыто]**
- [ ] Старая IO-шина заменяется новыми LVDS-платами.
- [ ] Определить протокол LVDS-плат.
- [ ] Перевести захардкоженные тумблеры (`RunOnHardRst`, `RunOnSoftRst`, `SoftRstOnEOT`, `EchoMode`) в реальные переключаемые сигналы (OPEN-011).

## 19.6. Стенд и модули

- [ ] Завершить проектирование стенда.
- [ ] Проверить питания под нагрузкой.
- [ ] Реализовать генератор до 1 МГц.
- [x] Внешний генератор допускается для частот выше.
- [x] Фронты: цель ≤50 нс, идеально ~10 нс.
- [ ] Сделать пилотный модуль.
- [ ] Измерить задержки вручную осциллографом.
- [ ] Сформировать первичный liberty.
- [x] Зафиксирован edge connector 2×36.
- [ ] Определить схему сброса декатрона (физический эксперимент, независимо от модели в RTL).
- [ ] Сопоставить RTL-примитивы с ламповыми ячейками библиотеки (REQ-MOD-008).

---

# 20. План работ

## Фаза 0: фиксация требований и оценок

Цель: закрыть открытые архитектурные решения.

Задачи:

1. Подтвердить (не как допущение) поведение `CLRD` относительно MemLock (OPEN-002).
2. Подтвердить поведение `SOT` относительно ISA (OPEN-003).
3. Сверить `0xC`/`0xD` opcode Debug ISA с фактическим `insnValues.sv` (OPEN-009).
4. Принять решение по `DekatronTubeV2`: миграция или параллельная модель (OPEN-008) — **это решение блокирует объём Фазы 1**.
5. Определить завершение bootloader (OPEN-004).
6. Определить поведение BELL-автоматики: CIN/HALT/error (OPEN-007).
7. Зафиксировать точную схему 10-bit data encoding (REQ-DATA-004/005).

## Фаза 1: критический RTL-рефакторинг

Цель: сделать RTL надёжным до дальнейшего развития. **[v0.4] Порядок шагов зафиксирован явно и строго последователен — каждый следующий шаг зависит от предыдущего, распараллеливать 1а/1б нельзя.**

### Шаг 1а — физическая модель декатрона (без handshake) — **ВЫПОЛНЕН [v0.5]**

1. ~~Реализовать `DekatronTubeV2`~~ — сделано, но на кольцевой модели вместо FSM (REQ-DTV2-010).
2. ~~Параметризовать временные характеристики~~ — сделано (REQ-DEK-014).
3. ~~Перенести тестовый план TRS v0.1 §14–16~~ — тестбенч написан, **но не прогнан в симуляторе**.

Остаток по шагу: прогон в Verilator/Icarus (REQ-VER-029), тесты на операции «встык» (REQ-VER-028).

### Шаг 1б — DekatronCounter: первый уровень с Valid/Ready — **ВЫПОЛНЕН [v0.5]**

4. ~~Реализовать счётчик вокруг верифицированной модели декатрона~~ — сделано.
5. ~~Устранить гонку `Nines`/`Zeroes`/`state` и лишние Impulse-прослойки~~ — сделано заменой счётчика целиком.
6. ~~Определить поведение carry при одновременном переносе в обе стороны~~ — снято: узел не используется (OPEN-010 закрыт).

Остаток по шагу: тестбенчи `DekatronModule` и `DekatronCounter` (REQ-VER-030).

### Шаг 1в — распространение Valid/Ready наверх — **ВЫПОЛНЕН [v0.6]**

7. ~~Перевести память, `IpLine`, `ApLine`, `MachineCtrl` на Valid/Ready~~ — сделано, единым протоколом на всех уровнях.
8. ~~Учесть новые свойства счётчика в верхних блоках~~ — сделано: физические линии сброса, однотактный инкремент (`out_valid` удалён в v0.10).
9. ~~Оптимизировать `BcdToBinEnc`~~ — снято банковой организацией памяти.

Остаток по шагу:

10. Удалить старые модули из дерева исходников.
11. ~~Обновить C++ golden model до полного ISA (REQ-GM-001/003/004)~~ — сделано **[v0.8]**.
12. Написать тестбенчи на новые блоки и прогнать всё в Verilator.

## Фаза 2: стенд и первые модули

Цель: получить измерительную базу.

Задачи:

1. Дособрать стенд: питания; генератор до 1 МГц; слоты; байонеты; защиту.
2. Сделать пилотные модули: NOT_N16; OR2_N16/NOR2_N16.
3. Снять первые задержки осциллографом и **откалибровать все временные параметры модели декатрона**: `GUIDE_STEP_HS`, `FALL_STEP_HS`, `WRITE_MIN_HS`, `RESET_MIN_HS` (OPEN-013). Особое внимание — времени сваливания разряда с подкатода на главный катод: именно оно определяет длину третьего интервала такта и, следовательно, достижимую тактовую частоту.
3а. Проверить на реальном А110, что при 1 МГц успевают отработать все три интервала (OPEN-014). Если нет — вернуться к счёту через такт, 500 кГц.
4. Начать заполнение liberty; сопоставить RTL-примитивы (`RsLatch`, `Register`, mux) с ламповыми ячейками (REQ-MOD-008).
5. Перевести захардкоженные Emulator-тумблеры в реальные переключатели, если требуется для стендовых тестов (OPEN-011).

## Фаза 3: гибридная эмуляция и новые IO

Цель: заменить часть RTL реальными блоками.

Задачи:

1. Спроектировать новые LVDS-платы: 2–3 платы; блочное подключение; уровни под 1 MHz.
2. Адаптировать эмулятор для подмены блоков (с учётом зафиксированного интерфейса Emulator↔DekatronPC, Приложение B).
3. Проверить работу IP/AP/Data-блоков в гибриде.
4. Продолжить измерения и уточнение liberty.
5. Передавать данные в P&R-инструмент.

---

# 21. Definition of Done для ближайшего крупного RTL-релиза

RTL считается готовым к следующему этапу, если выполнены следующие условия:

- [x] `DekatronTubeV2` реализована, покрыта временными характеристиками. **[v0.5]**
- [x] `DekatronCounter` реализован вокруг `DekatronTubeV2` с Valid/Ready. **[v0.5]**
- [ ] Вся подсистема декатрона прогнана в Verilator и Icarus. **[v0.5, критично: пока проверена только на Python-копии RTL]**
- [ ] Тестбенчи `DekatronModule` и `DekatronCounter` написаны и проходят.
- [ ] Полный переход на Valid/Ready-протокол выполнен и покрыт тестами на уровне `IpLine`/`ApLine`/памяти. **[v0.3, заменяет прежний пункт «нет известных критических проблем handshake»]**
- [ ] `DekatronPulseAllow` удалён из дерева исходников.
- [ ] Старые `Dekatron.sv`/`DekatronModule.sv`/`DekatronCounter.sv`/`DekatronCarrySignal` удалены из тракта счёта.
- [ ] Все существующие тесты проходят после рефакторинга.
- [x] Debug ISA и Brainfuck ISA покрыты диспетчеризацией; тестами — частично (сквозные прогоны Hello World, ROT13).
- [ ] Undefined opcode ведет себя как NOP.
- [ ] `CLRI` и `CLRA` корректно сбрасывают соответствующие счётчики и MemLock.
- [x] Поведение `CLRD` относительно MemLock подтверждено и покрыто тестом. **[v0.6]**
- [ ] Hard Reset устанавливает IP = 99900 и ISA = Debug.
- [ ] Soft Reset устанавливает IP = 0 и ISA = Brainfuck.
- [x] Opcode `0xC`/`0xD` Debug ISA сверены и подключены. **[v0.6]**
- [ ] SOT/EOT загрузка работает с клавиатуры/Firmware/внешнего канала.
- [ ] Поведение SOT относительно переключения ISA подтверждено (не осталось допущением).
- [ ] Bootloader проходит базовый сценарий.
- [x] Data RAM использует 10-битное представление и банковую модель. **[v0.6]**
- [x] `RsLatch` при `S=R=1` — вопрос снят, узел не используется. **[v0.5]**
- [x] C++ golden model поддерживает полный ISA. **[v0.8]**
- [ ] Есть базовые тесты производительности.
- [ ] Gate-level simulation после Yosys проходит с учётом задержек.
- [x] Решение по `DekatronTubeV2` (миграция/параллельно) принято и отражено в коде. **[v0.5]**
- [ ] Тайминги декатрона откалиброваны на экспериментальной ячейке (OPEN-013).

---

# 22. Следующие рекомендуемые действия

1. **Продолжить прогон в Verilator и Icarus** (REQ-VER-029). Первый прогон уже вскрыл комбинационную петлю в `DekatronCounter`; остальные блоки проверены только на Python-копиях, где такие ошибки невидимы. `UNOPTFLAT` в регрессии трактовать как ошибку (REQ-VER-031).
2. Написать тестбенчи на новые блоки: `Ram`/`IpMemory` (банковая адресация, регистровый выход, сквозная запись, защита загрузчика), `ApLine` (MemLock, ленивое чтение), `IpLine` (промотка, переполнение), `MachineCtrl` (полная таблица ISA, `TEST` перед скобками). **[v0.10]** `ApLine_tb`, `IpLine_tb` и `MachineCtrl_tb` есть и входят в `run_tests.sh -t`; в cocotb-регрессию не входят.
3. Прогнать синтез целиком и сверить фактическое занятие блоков памяти с расчётными 80.
4. Удалить старые модули из дерева исходников, чтобы не осталось двух параллельных трактов.
5. ~~Обновить C++ golden model до полного ISA~~ **[v0.8]**. Подключить пошаговое сравнение с новым RTL: ~~исправить `AP_COUT` (OPEN-017), привести `txData()` модели к выводу со счётчика~~ **[v0.10]**, ~~собрать `DekatronPC_tb.cpp` и прогнать `-s` на Hello World~~ **[v0.10]** (в CI, `doc/ci_sim_check.md`), ~~прогнать Pi~~ **[v0.10]** (`doc/pi_step_check.md`).
6. Проверить на модели тайминги ленивого чтения при медленной памяти: с ростом `READ_CYCLES` выигрыш должен только увеличиваться, но это стоит подтвердить.
7. На Фазе 2 — калибровка таймингов декатрона на экспериментальной ячейке (OPEN-013) и проверка достижимости 1 МГц на реальном А110 (OPEN-014).
8. Внести в RTL решения v0.9: ~~`LOOP_DEKATRON_NUM = 2`~~ (внесено в v0.10), ~~сброс `lock` в `ApLine` при смене адреса~~ (снят вместе с `dirty` в v0.10), ~~`cout_pending` в `MachineCtrl`~~ (вывод через `AP_COUT` внесён в v0.10) **[v0.9]**.
9. Решить, нужен ли признак `Valid` декатрона в функциональном тракте или только для отладки и ассертов (тогда `ready` строится по времени, а не по показанию лампы) **[v0.9]**.
10. **Уложить всю машину в 1200 ламп** (REQ-MOD-009) **[v0.10]**. Сейчас три блока — 1377,5 (после двоичного кодирования автоматов и T4–T6, `doc/tube_count_reduction.md` §17). Сначала посчитать то, что синтез пока не видит (обвязка памяти, `RstTimeRelay`, пульт), чтобы знать полный счёт, затем искать сокращение за пределами чистки автоматов: состояние и флаги на декатронах, разделяемые с декатронами кодеки и т. п. Варианты с изменением правил (как отклонённые R8/R9) — только с решения владельца. Отчёт: `doc/tube_count_reduction.md`.
11. Прогнать с упреждающей выборкой (REQ-PERF-003) ~~пошаговое сравнение `DekatronPC_tb.cpp -s` в Verilator~~ (helloworld и `pi.bfk` совпадают, `doc/pi_step_check.md`) и симуляцию нетлиста `synth_sim.sh` **[v0.10]**.
12. **Структуры из проводов для межблочных соединений** (REQ-PR-019) **[v0.10]**: по одной на каждый разъём блока, чтобы порты IpLine, ApLine и MachineCtrl группировались по разъёмам HD-68. Без этого P&R не может развести весь компьютер (REQ-PR-013/014).

---

# Приложение A. Сводная таблица находок аудита RTL (functional reports → REQ-ID) [v0.3]

| Находка (из отчёта) | Файл/модуль | Связанный REQ-ID |
|---|---|---|
| `DekatronPulseAllow` — пустой модуль, инстанцируется | `Dekatron/DekatronPulseAllow.sv` | REQ-REF-003 — **не используется в новой подсистеме [v0.5]** |
| Дублирование логики `EN_HARD_RST=0/1` | `Dekatron/Dekatron.sv` | REQ-RTL-016, REQ-REF-009 — закрывается удалением старого файла |
| `RsLatch` не специфицирован при `S=R=1` | `Logic/RsLatch.sv`, `DekatronCarrySignal` | REQ-REF-008, OPEN-010 — **снято [v0.5]**, узел не используется |
| `DekatronModule.OutPos` маскируется в `X` во время импульсов | `Dekatron/DekatronModule.sv` | REQ-RTL-015 — **устранено [v0.5]**, заменено сигналом `Valid` |
| 4 Impulse-прослойки в одном счётчике | `Dekatron/DekatronCounter.sv` | REQ-REF-006 — **устранено [v0.5]**, осталась одна пара |
| `BcdToBinEnc` синтезирует умножители на 10/100/1000/10000 | `Functions/BcdToBinEnc.sv` | REQ-REF-010 — **снято [v0.6]** банковой памятью |
| `BcdToBin.v`/`BinToBcd.v` — стиль Verilog-95 | `Dekatron/BcdToBin.v`, `Dekatron/BinToBcd.v` | REQ-RTL-013, REQ-REF-012 |
| IP объявлен как «5 декатронов = 1M ячеек» в тексте отчёта (несогласованность: должно быть 100 000) | `1786044911450-rtl-functional-report.md` §1 | REQ-ARCH-009 (замечание к отчёту, не к RTL) |
| `RAM` данных объявлена 8-битной, а не 10-битной BCD | `DekatronPC/RAM.sv` | REQ-MEM-DATA-002 — **исправлено [v0.6]** |
| Opcode `0x2` (BELL) отсутствует в `insnValues.sv` | `DekatronPC/insnValues.sv` | REQ-ISA-006 — **подключено [v0.6]** |
| Отдельный opcode `SRST` не подтверждён как исполняемая инструкция | `DekatronPC/insnValues.sv`, `InsnDecoder.sv` | OPEN-009 |
| `RunOnHardRst`/`RunOnSoftRst`/`SoftRstOnEOT`/`EchoMode` захардкожены в Emulator | `Emulator/Emulator.sv` | REQ-PANEL-001/002/003/008, OPEN-011 |
| UART-параметры (110 бод и др.) захардкожены, тумблеров нет | `Emulator/Emulator.sv`, `rtl/uart/` | REQ-UART-006 |
| `IpMemory`/`RAM` — monolithic, без банковой организации | `DekatronPC/IpMemory.sv`, `DekatronPC/RAM.sv` | REQ-MEM-IP-003/004 — **реализовано [v0.6]** |
| Отсутствует error-флаг переполнения Loop Counter | `Dekatron/DekatronCounter.sv` (LOOP) | REQ-CNT-007 — **реализовано [v0.6]**, включая прерывание промотки |
| `DekatronTubeV2` (TRS v0.1) не интегрирована в RTL | вся `Dekatron/` подсистема | REQ-DTV2-001..010 — **реализовано [v0.5]** на кольцевой модели |
| Упреждающее чтение ячейки в ApLine | `ApLine.sv` v0.6 | REQ-APV2-001 — **заменено ленивым [v0.7]**, −36% обращений |
| Копия ячейки в ApLine дублирует регистр памяти | `ApLine.sv` v0.6 | REQ-APV2-002 — **устранено [v0.7]**, регистр перенесён в память |
| APB для памяти при единственном мастере | `Ram.sv`, `IpMemory.sv` v0.6 | REQ-MEMV2-001 — **отменено [v0.7]** в пользу Valid/Ready |
| `MachineCtrl` не видит сброса с пульта | `MachineCtrl.sv` v0.6 | REQ-CTLV2-009 — **исправлено [v0.7]** |
| Переполнение вложенности не останавливает машину: `S_FETCH_W` перебивает `S_HALT` | `MachineCtrl.sv` v0.7 | REQ-CTLV2-005 — **исправлено [v0.10]** |

---

# Приложение B. Зафиксированный интерфейс Emulator ↔ DekatronPC [v0.3]

Источник: `1786044911450-emulator-functional-report.md`, раздел 2 (по факту инстанцирования `DekatronPC` в `Emulator.sv:258`). Статус: **Done, зафиксировано** (закрывает REQ-EMU-002).

### Тактирование и сброс
| Сигнал | Направление | Назначение |
|---|---|---|
| `hsClk` | Emu → DPC | Физический такт декатронов (10 MHz) |
| `Clk` | Emu → DPC | Процессорный такт (1 MHz) |
| `SoftRst_n` | Emu → DPC | Программный сброс |
| `HardRst_n` | Emu → DPC | Аппаратный сброс |

### Управление исполнением
| Сигнал | Направление | Назначение |
|---|---|---|
| `Halt` / `Step` / `Run` | Emu → DPC | Управление выполнением |
| `keyNextIp` / `keyPrevIp` | Emu → DPC | Ручной сдвиг IP |
| `key_next_app_i` | Emu → DPC | Переход к следующей программе |
| `InsnLoadingStart` / `InsnLoadingStop` | Emu → DPC | Начало/конец загрузки программы |
| `EchoMode` / `RunOnHardRst` / `RunOnSoftRst` / `SoftRstOnEOT` | Emu → DPC | Панельные режимы (пока захардкожены — см. Приложение A) |

### Канал загрузки инструкций
| Сигнал | Направление | Назначение |
|---|---|---|
| `InsnIn[3:0]` / `InsnInValid` | Emu → DPC | Загружаемая инструкция и её валидность |
| `InsnInReady` / `InsnInLoading` | DPC → Emu | Готовность/статус приёма |

### CIN/COUT
| Сигнал | Направление | Назначение |
|---|---|---|
| `tx_data_bcd[11:0]` / `tx_vld` | DPC → Emu | Вывод; `tx_data_bcd` — всегда счётчик данных, достоверен при `tx_vld` **[v0.10]** |
| `tx_rdy` | Emu → DPC | Готовность принять вывод |
| `rx_data_bcd[11:0]` / `rx_vld` | Emu → DPC | Ввод; `rx_data_bcd` держится до `rx_vld & rx_rdy` **[v0.10]** |
| `rx_rdy` **[v0.10]** | DPC → Emu | Символ принят: CIN завершён, счётчик данных записан (REQ-UART-008) |

### Состояние (для отображения)
| Сигнал | Направление |
|---|---|
| `IRET[31:0]`, `IpAddress[19:0]`, `ApAddress[19:0]`, `LoopCount[7:0]` **[v0.9]**, `ApData1[11:0]`, `RomData1[3:0]`, `state[2:0]`, `Insn[3:0]` | DPC → Emu |
| `IpAddress1[19:0]`, `ApAddress1[19:0]` | Emu → DPC (доп. порт для MS6205) |

**[v0.3] Правило:** любое изменение состава/семантики этого списка сигналов — breaking change, требующий ревизии этого документа и синхронного обновления `io_key_display_block`/`MS6205`/`Sequencer` (см. REQ-EMU-DISP-003).

---

# Приложение C. DekatronTubeV2 vs текущий Dekatron.sv — таблица расхождений [v0.3]

| Аспект | `DekatronTubeV2` (TRS v0.1, целевая модель) | Текущий RTL (`Dekatron.sv`+`DekatronModule.sv`) |
|---|---|---|
| Такт | только `hsClk` | `hsClk` + `Clk` (в `DekatronCounter`) |
| Сброс | только `reset0_i`/`reset9_i` (физический), без цифрового `rst_n` в самом декатроне | `Rst_n` и `HardRst_n` — отдельные цифровые входы, с дублированной логикой под `EN_HARD_RST` |
| Счётные импульсы | `guide_a_i`/`guide_b_i`, явная 2-фазная квалификация с таймаутами (`GUIDE_MIN_HS`/`GUIDE_MAX_HS`/`PHASE_WINDOW_HS`/`RETURN_TIMEOUT_HS`) | `Pulses[1:0]` от `DekatronPulseSender`, формируется цепочкой `OneShot` с фиксированными `DELAY=9/4/3/8` |
| Запись | `write_en_i` + `write_pos_i` (one-hot), с явной длительностью `WRITE_MIN_HS`/`WRITE_MAX_HS` и `settled_dbg_o` | `In_n[9:0]` + управляющие уровни через `DekatronWriteAmp`, длительность через `OneShot#(DELAY=100)` в `DekatronCounter` |
| FSM | явная, 4 состояния (`ST_STABLE`/`ST_GUIDE`/`ST_WRITE_RESET`/`ST_INVALID`) с явными assertions | неявная, комбинационно-регистровая логика без явного перечисления состояний; защита через маскирование в `X` |
| Debug-выходы | `cathodes_dbg_o`, `on_guide_dbg_o`, `in_write_reset_dbg_o`, `settled_dbg_o`, `invalid_dbg_o` | debug-выходы не выделены как отдельный контракт |
| Граница ответственности | чётко исключает `valid/ready/busy`, TOP_LIMIT_MODE — это `DekatronCounterV2` | границы между `Dekatron`/`DekatronModule`/`DekatronCounter` размыты — например, `TOP_LIMIT_MODE` внутри `DekatronCounter`, что соответствует духу разделения, но не по одинаковому контракту |
| Тесты | полный план: FSM coverage, функциональное покрытие, testbench-каркас (TRS v0.1 §13–16) | тесты существуют (см. §14.1), но не по этому плану |

**Вывод [обновлено v0.5]:** таблица выше сохранена как история сравнения FSM-спецификации TRS v0.1 с прежним `Dekatron.sv`. Фактически реализован **третий** вариант — кольцевая модель (REQ-DTV2-010), которая отличается от обоих: явной FSM в ней нет вовсе, а место `PHASE_WINDOW_HS`/`RETURN_TIMEOUT_HS` занял `FALL_STEP_HS`. Ниже — исходный вывод v0.4, приведший к решению о миграции.

**Вывод [v0.4]:** `DekatronTubeV2` — это переработанная, более строгая спецификация того же физического устройства, не совместимая по интерфейсу с текущим `Dekatron.sv` напрямую. **Решение принято (OPEN-008 закрыт):** полная последовательная замена нижнего уровня. `DekatronTubeV2` реализуется и полностью верифицируется в изоляции — без каких-либо handshake-сигналов, поскольку это противоречило бы физике прибора (REQ-DEK-012) — и только затем вокруг неё пишется `DekatronCounterV2`, первый уровень иерархии, где Valid/Ready вообще применим. См. раздел 20, Фаза 1.
