radiolok/dekatronpc/doc/dekatron_valid_removal.md

---
title: Удаление признака Valid у декатрона, готовность счётчика по длительностям
date: 2026-10-06
status: отчёт
requirements: REQ-DEK-016, REQ-DMOD-006, REQ-CNT-V2-002/002a/003/007/008/009, REQ-PULSE-002, REQ-RTL-015, OPEN-013
---

# Удаление признака Valid у декатрона

## 1. Что было и почему убрано

`DekatronModule` выдавал `Valid = |MainOneHot`. При синтезе это была отдельная лампа ИЛИ-10 (`OR10_X7`). `DekatronCounter` собирал из этих признаков `out_valid = &dek_valid` и регистр `settled_q`, а `ready` был равен `(state == ST_IDLE) & settled_q & ~rst_active`.

Признак говорил только «разряд стоит на каком-то главном катоде». Закончилась ли операция, из него не следует:

- во время шага разряд проходит через подкатоды, и `Valid` падает в середине такта. Это не новость: длительность шага и так известна заранее;
- во время записи или сброса главные катоды заблокированы воздействием, `Valid` = 0 всё окно. Длительность окна и так задаёт реле времени.

Решение владельца (06.10.2026): признак у декатрона убрать, а готовность выдавать вызывающему блоку по известным длительностям:

- инкремент и декремент гарантированно укладываются в один такт `clk`;
- запись и сброс запускают реле времени (`writeTimer`). `ready` снимается в момент, когда счётчик видит операцию или поднятую линию сброса, и возвращается по окончании окна.

## 2. Изменения в RTL

| Файл | Изменение |
|---|---|
| `DekatronModule.sv` | Убран выход `Valid` и лампа `OR10_X7`. Проверка окна сваливания стала строгой (см. §3). |
| `DekatronCounter.sv` | Убраны `out_valid`, `dek_valid`, `settled_q`. Признаки `zeroes_q`/`nines_q`/`tops_q` защёлкиваются на каждом фронте `clk`. Новое состояние `ST_RST`: подъём `soft_rst`/`hard_rst` запускает тот же `writeTimer`, что и запись, а `ready` возвращается, только когда линия снята и окно истекло. Регистр `primed_q` держит `ready` снятым один такт после `rst_n`, пока признаки не защёлкнуты впервые. |
| `ApLine.sv`, `IpLine.sv` | Ожидание `X_ready & X_out_valid` заменено на `X_ready`. |
| `DekatronPhaseGen.sv`, `DekatronPulseSender.sv`, `DekatronModule.sv`, `DekatronCounter.sv` | `PHASE2_HS` по умолчанию 4 → 3: нарезка такта 3/3/4 вместо 3/4/3 (см. §3). |
| `rtl/tests/Dekatron.sv/Dekatron_tb.sv`, `rtl/tests/Counter.sv/Counter_tb.sv` | Ожидание `Valid`/`OutValid` заменено на `Ready` или на фиксированное число тактов. |

`ready` по-прежнему не зависит от `writing`: `ST_RST` — обычное состояние автомата, петли `ready → accept → write_req → writing → ready` нет (REQ-CNT-V2-002a).

## 3. Находка: шаг не укладывался в такт

Без `Valid` правило «шаг занимает один такт» должно выполняться в модели буквально. Замер на одноразрядном счётчике (`step_tb`, Icarus, шкала в тактах `hsClk`):

```
hs=41  фронт clk, Phase1 начинается
hs=43  разряд на подкатоде A
hs=44  Phase2
hs=46  разряд на подкатоде B
hs=48  фазы сняты, идёт сваливание (FALL_STEP_HS = 3)
hs=51  фронт clk  И  разряд падает на главный катод — тот же фронт
```

При нарезке 3/4/3 и `FALL_STEP_HS = 3` разряд попадает на главный катод ровно на следующем фронте `clk`. Запаса нет, и защёлка по этому фронту видит состояние «на подкатоде». Старый тракт это маскировал: `settled_q` снимал `ready` на один такт после каждого шага, а признаки не обновлялись, пока `Valid` = 0. Фактически шаг занимал два такта `clk` для любого потребителя признаков `zero`/`at_top`.

Симптом после удаления `Valid`: `IpLine` в промотке назад читал `loop_is_zero` от предыдущего шага, не находил парную скобку и уходил через 00000 в 99999 (тест `IpLine` зависал).

Исправление (выбрано владельцем): нарезка 3/3/4. Окно сваливания 4 hs против `FALL_STEP_HS = 3` даёт запас в один такт `hsClk`. Проверка в `DekatronModule` стала строгой: `HS_PER_CLK − PHASE1_HS − PHASE2_HS > FALL_STEP_HS`. `GUIDE_STEP_HS = 2` по-прежнему ≤ обеих фаз. Значения остаются оценочными до калибровки (OPEN-013).

## 4. Проверка

Все прогоны — Icarus через `rtl/run/emul` и Verilator `--lint-only`. Полную сборку DekatronPC в Verilator и регрессию cocotb не запускали.

| Тест | До (HEAD b68a39f) | После |
|---|---|---|
| `Dekatron` | pass | pass, 257 µs |
| `Counter` | pass | pass, 3181 µs |
| `ApLine` | pass | pass, 275 µs |
| `IpLine` (`looptest.bfk`) | pass, 784 µs | pass, **656 µs** |
| `verilator --lint-only DekatronPC` | чисто | чисто по этой правке; см. §5 |

`IpLine` стал на 16 % быстрее: шаги промотки больше не ждут лишний такт установления.

## 5. Решения по открытым пунктам (06.10.2026)

- **`LOOP_DEKATRON_NUM = 2`.** Изменение внёс владелец: по исследованию глубины вложенности 0–99 достаточно (REQ-CNT-002 — Done). Предупреждение WIDTHTRUNC в `DekatronCounter` устранено: `TOP_VALUE` по умолчанию теперь `{D_NUM{4'd5}}`, а не фиксированные 12 бит, подавление `WIDTHEXPAND` убрано. `verilator --lint-only -Wall` для DekatronPC чист.
- **Повтор `zero`/`at_top` встык в `TOP_LIMIT_MODE`.** Владелец считает это не проблемой: мастера `ApLine`/`IpLine` между шагами проходят через состояние ожидания и встык в этом режиме не шагают. Оставлено как есть.
- **Схемы.** Генератор схем теперь лежит в `tools/schemes/`. Обновлены листы 1 (временная диаграмма 3/3/4), 2 (без `OR10_X7`/`Valid`), 3 (окно записи от `write_req | rst`, `primed_q`, состояние `ST_RST` в автомате), 4, 5 (ожидание по `ready`, Loop — 2 декады) и 7. SVG и `SCHEMES.md` пересобраны командой `python3 tools/schemes/build.py`. Рендерера SVG в окружении нет, поэтому раскладку проверяли по координатам, а не глазами.
- cocotb `test_dek_counter` портом `out_valid` не пользуется. Локально его не прогоняли: в окружении нет cocotb (`cocotb_tools`). Проверка остаётся за CI.
