radiolok/dekatronpc/doc/dpcrun_golden_model.md

---
title: C++ golden model dpcrun — полный ISA, модульные тесты, CI
date: 2026-09-27
status: отчёт
requirements: REQ-GM-001, REQ-GM-003, REQ-GM-004, REQ-VER-015..022
---

# C++ golden model `dpcrun`: полный ISA

Модель лежит в сабмодуле `bfutils/dpcrun` (`dpcrun.h`, `dpcrun.cpp`), тесты — в `bfutils/dpcrun/test/test_dpcrun.cpp`, CI — `bfutils/.github/workflows/ci.yml`.

Итог:

- Модель переписана с нуля. Она поддерживает оба набора команд, MemLock с ленивым чтением, загрузку SOT/EOT, аппаратный и программный сбросы, переполнение счётчика циклов и защищённое от записи ПЗУ загрузчика.
- **По решению владельца проекта модель повторяет RTL как есть**, включая места, где RTL и TRS расходятся (§4). Исключение одно, это дефект COUT (§5.1).
- 53 модульных теста, 458 проверок, 1,5 с. Тесты гоняются в GitHub Actions репозитория bfutils (gcc и clang).
- Самопроверка по числам TRS: на `pi.bfk` модель насчитала **99 077** обращений к памяти данных — ровно столько, сколько замерено для RTL в TRS v0.7 §1. Расхождение IRET с цифрой 198 594 объяснено полностью (§3.4).
- При сверке найдено пять проблем в RTL и загрузчике (§5). Главная: `.` не запрашивает у `ApLine` чтение ячейки, и после `>` выводится значение предыдущей ячейки: Hello World печатается как `Hello WWrld!!`. TRS считает этот вопрос закрытым (OPEN-017).

## 1. Что было

Прежний `CppMachine`/`stepCpp()` интерпретировал **ASCII-текст** программы, а не опкоды (нарушение REQ-IPV2-005). Он знал только восемь символов Brainfuck и `0`. Не было Debug ISA, MemLock, SOT/EOT, сбросов и загрузчика. Промотка останавливалась не на парной скобке, а за ней, поэтому IRET не совпадал с RTL.

## 2. Интерфейс

```cpp
dpc::Config cfg;                 // apTop (OPEN-001), тумблеры RunOnHardRst, SoftRstOnEOT, EchoMode, Bell*
dpc::Machine m(cfg);
m.loadCode(dpc::assemble(src));  // загрузчик: текст -> опкоды, таблица generate_rom.py
m.setBootRom(dpc::assemble("DA0B<D{0B<D}BH"));
m.softReset(); m.run();          // панель: SoftRstKey, Run
dpc::Status s = m.step();        // одна инструкция = один проход S_DECODE
```

- `step()` возвращает `Ok`, `Halted` или `WaitInput`. `WaitInput` означает, что CIN или режим загрузки ждут ввода; после `pushInput()`/`pushInsn()` шаг повторяется.
- Наблюдаемое состояние: `ip()`, `ap()`, `loopCount()`, `dataCounter()`, `memLock()`, `insnMode()`, `loading()`, `halted()`, `loopOverflow()`, `insn()`, `iret()`, `bells()`, `output()`.
- `txData()` — ровно то, что RTL выдаёт на `tx_data_bcd`: всегда счётчик данных **[v0.10]**. Перед выводом `.` без MemLock грузит в него ячейку (OPEN-017). `cellValue()` — архитектурное значение текущей ячейки.
- Статистика `memReads()`/`memWrites()` повторяет обращения `ApLine` к памяти данных, включая `AP_TEST` перед скобками.
- Автономный запуск: `dpcrun -f prog.bfk [-b boot.bfk] [-B] [-a 99999] [-n max] [-s]`. Программа кладётся с адреса 0, за ней ставится HALT, затем Soft Reset и Run.

## 3. Семантика (по RTL)

### 3.1. Выборка и промотка (`IpLine`)

- IP указывает на **исполненную** инструкцию. Сдвиг выполняется при следующей выборке.
- После сброса, `CLRI` и останова первая выборка читает по текущему IP без инкремента (`ip_counted_q`).
- Решение о промотке принимается при следующей выборке по признаку `loop_val_zero`: в BF — ноль ячейки, в Debug — `AP == 0`. Детектор скобок один для обоих ISA.
- Промотка останавливается **на** парной скобке, и эта скобка затем декодируется как обычная инструкция (IRET +1).
- Счётчик вложенности: +1 за стартовую скобку и за каждую свою, −1 за ответную. Счётчик двухдекадный, 0–99 (`LOOP_SIZE = 100`, как `LOOP_DEKATRON_NUM = 2`). Инкремент со 99 — аппаратная ошибка (REQ-CNT-007). Как и в RTL (IpLine, `at_top`), она ловится ДО шага: инкремент не выдаётся, счётчик остаётся на 99 до CLRL или сброса, промотка прерывается, машина останавливается, звонок при `BellOnError`. Промотка, начатая со счётчиком на 99, переполняется сразу.
- Промотка **всегда завершается**. Память программ — кольцо: если своих скобок в нём не больше, чем ответных, счётчик доходит до нуля за один оборот. Иначе каждый оборот снова засчитывает стартовую скобку, и счётчик растёт до переполнения. Для одиночной `[` это примерно 10⁷ чтений (тест `unmatched_bracket_overflows`).
- Промотка идёт насквозь через ПЗУ загрузчика. `{`/`}` там имеют те же коды 0x6/0x7 и учитываются как скобки.

### 3.2. Данные (`ApLine`)

| Операция | Поведение |
|---|---|
| `+` `-` | без MemLock: чтение (если значения нет в регистре), затем шаг; MemLock ставится |
| `>` `<` | при MemLock — выгрузка в старую ячейку и снятие MemLock; шаг AP с переходом 29999 ↔ 0; ячейка не читается |
| `CLRA` | то же, что `>`, но AP → 0 |
| `CLRD`, `[-]` | счётчик → 0, MemLock ставится (REQ-ML-009) |
| `,` | счётчик ← символ, MemLock; эхо при `EchoMode` |
| `.` | чтение, если значения нет ни в счётчике, ни в регистре; вывод (см. §5.1) |
| `LOAD` | счётчик ← ячейка; MemLock не меняется |
| `STORE` | ячейка ← счётчик; MemLock не меняется (следующий `>`/`<`/`CLRML` запишет ячейку ещё раз) |
| `CLRML` | выгрузка при MemLock, снятие MemLock |
| `[` `]` в BF | `AP_TEST`: чтение, если значения нет под рукой |

Данные — 0..255 с переходом через 0. Сброс не выгружает грязный счётчик: его значение теряется, память сохраняется.

### 3.3. Управление (`MachineCtrl`)

- **HALT**: после останова IpLine сдвигает IP ещё на одну позицию, поэтому Run продолжает со следующей инструкции.
- **Hard Reset**: IP = 99900, AP/Data/Loop = 0, MemLock снят, Debug ISA. Машина стоит, если не включён `RunOnHardRst`. IRET сбрасывается только по `rst_n`.
- **Soft Reset**: всё в 0, BF ISA. Запуск — при `RunOnSoftRst`.
- **SOT** включает режим загрузки, ISA не меняется (OPEN-003, как в RTL). Опкоды пишутся с адреса после SOT, IP инкрементируется, каждый принятый опкод считается в IRET. Запись в банк загрузчика игнорируется.
- **EOT** распознаётся только в Debug ISA и в память не пишется. При `SoftRstOnEOT` выполняется Soft Reset, иначе останов. Вне загрузки EOT — NOP.
- **ISA0/ISA1** во время загрузки действуют и **записываются** в память.
- **BELL** считается событием `bells()`/`onBell` (OPEN-007 открыт).
- Все 32 комбинации `{mode, opcode}` декодируются. Резервный 0x3 Debug и EOT вне загрузки — NOP.

### 3.4. IRET на `pi.bfk`

TRS v0.7 приводит 198 594 инструкции — это счёт чистого Brainfuck. Модель насчитывает 221 386:

```
198 594  инструкций Brainfuck
+ 5 715  парных ']' после пропуска '['
+17 076  парных '[' после возврата по ']'
+     1  завершающий HALT
= 221 386
```

Каждая промотка добавляет декодирование парной скобки. Так работает RTL, и на эту величину должно рассчитываться пошаговое сравнение.

## 4. Где модель следует RTL, а не TRS

Решение владельца проекта (2026-09-27): модель повторяет RTL. Эти места отмечены в коде комментариями `RTL:` и закреплены тестами. Если RTL исправят, тест и модель меняются вместе.

| № | RTL | TRS | Тест |
|---|---|---|---|
| 1 | `CLRI` сбрасывает только IP, MemLock не трогает | REQ-ISA-DEBUG-004, REQ-ML-006: сбрасывает и MemLock | `clri_keeps_memlock` |
| 2 | ~~`CLRA`, `>`, `<` снимают MemLock только вместе с выгрузкой грязного счётчика~~ **Устранено 2026-10-08:** `dirty` удалён, при MemLock всегда выгрузка и снятие | REQ-ML-005/007: MemLock снимается | `clra_after_store_unlocks` |
| 3 | ~~После `STORE` (MemLock = 1, dirty = 0) блокировка переживает `>`~~ **Устранено 2026-10-08** вместе с `dirty` (REQ-APV2-003, `doc/memlock_single_flag.md`): `>` после `STORE` пишет ячейку второй раз и снимает MemLock | REQ-ML-005 | `store_keeps_lock_until_move` |
| 4 | ISA1 во время загрузки переключает ISA, после чего 0x4 — это `>`, а не EOT; загрузку завершит только ISA0 + EOT | не описано | `isa1_during_load_hides_eot` |

Пункты 2 и 3 были дефектом и устранены: флаг `dirty` удалён из RTL и модели, MemLock — единственный флаг владения ячейкой. Копирование по REQ-ISA-BF-004 (`LOAD`, переход, `STORE`) работает как прежде.

## 5. Найденные проблемы

### 5.1. `.` выводит значение не той ячейки — дефект RTL, противоречит OPEN-017

`MachineCtrl` на опкоде `5'h18` сразу поднимает `tx_vld` и не выдаёт `AP_COUT`. Константа `AP_COUT` объявлена, но нигде не используется. Без MemLock `tx_data_bcd` берётся из выходного регистра памяти, а после `>` он хранит **предыдущую** ячейку. Поэтому `>.` выводит не то. Если в модели убрать чтение перед выводом (то есть повторить RTL), `helloworld.bfk` печатает `Hello WWrld!!` вместо `Hello World!`.

TRS §18 закрывает OPEN-017 со словами «теперь используется». В текущем `MachineCtrl.sv` это не так.

Здесь модель RTL **не** повторяет: иначе она не прошла бы Hello World и была бы бесполезна как эталон. Она делает то, для чего в `ApLine` есть `OP_COUT`: читает ячейку при необходимости. Пошаговое сравнение поймает это место первым.

**Исправлено в RTL (2026-10-07), по решению владельца иначе, чем в модели.** Вывод всегда идёт со счётчика данных: `MachineCtrl` выдаёт `AP_COUT`, который при снятом MemLock загружает ячейку в счётчик (MemLock не меняется), и только потом `tx_vld`; в ApLine `tx_data_bcd = data_out`. Выводимый символ совпадает с моделью, но наблюдаемый `tx_data_bcd` между инструкциями — нет: модель возвращает `lock ? m_data : m_memReg`, RTL — счётчик, который после `>` держит прежнее значение. Модель приведена к тому же (bfutils, 2026-10-07): COUT при `!m_lock` загружает `m_data` из регистра памяти (с чтением при `!m_memHere`), MemLock и dirty не меняет; `txData()` возвращает `m_data`. Тест `tx_register_is_stale_after_move` переименован в `tx_shows_counter_after_move`, добавлен `cout_loads_cell_into_counter` (`+.>.<..`: чтения только при чужом регистре, вывод `ABAA`). 55 тестов, 482 проверки проходят; число обращений на Pi (99 077) не изменилось.

### 5.2. Переполнение счётчика циклов не останавливало машину — подтверждено, исправлено [v0.10]

В `MachineCtrl` присваивание `state <= S_HALT` по `loop_overflow` стоит **перед** `case (state)`. В том же такте `IpLine` уже вернулся в `S_IDLE` с `insn_valid_q = 1` и `ready = 1`, поэтому ветка `S_FETCH_W` присваивает `state <= S_DECODE` позже. Последнее неблокирующее присваивание побеждает. Машина декодирует скобку, на которой прервалась промотка, выставляет `error_flag` и продолжает работу, хотя REQ-CNT-007 требует останова.

Модель останавливается, как требует TRS. Нужен направленный тест `MachineCtrl` на Icarus.

**Подтверждено и исправлено (2026-10-07).** `MachineCtrl_tb` воспроизвёл дефект на прежнем автомате: машина не останавливалась, звонка по ошибке не было, скобка декодировалась. Нашёлся и второй дефект рядом: CLRL снимал `error_flag` в `S_DECODE`, а признак в IpLine гаснет только при приёме CLR_LOOP, поэтому в промежутке `error_flag` взводился снова и следующее переполнение уже не останавливало машину. В переписанном `MachineCtrl` (REQ-CTLV2-010) переполнение приоритетнее любого состояния и ловится по фронту `loop_overflow`; оба случая проходят. Комментарий «RTL: … can override it» в `Machine::scan()` (`bfutils/dpcrun/dpcrun.cpp`) устарел, поведение модели менять не нужно. Подробности: `doc/tube_count_reduction.md` §12.

### 5.3. В пошаговом режиме пропуск цикла не выполняется — дефект RTL

`IpLine.halt_rq` подключён к `IsHalted`. При входе в останов с `ip_counted_q` IpLine делает шаг IP **без проверки промотки**. В режиме Step машина останавливается после каждой инструкции, поэтому `[` при нулевой ячейке не пропускает тело, а входит в него. То же случится, если нажать Halt сразу после скобки. Модель пошаговый режим панели не моделирует.

### 5.4. `generate_rom.py` теряет NOP

`if not encoded: continue` отбрасывает опкод 0 (`'N'`), потому что 0 ложно. Программа с `N` в RTL-прошивке окажется короче, чем в модели, и все адреса после первого `N` сдвинутся. Исправление: `if encoded is None`. Загрузчик модели `dpc::assemble()` NOP сохраняет (тест `loader_skips_comments_keeps_nop`).

### 5.5. Загрузка в Debug ISA не может передать `>`

EOT и `>` имеют один код 0x4, а EOT распознаётся по `{insn_mode, insn_in}`. После `SOT` машина остаётся в Debug ISA (OPEN-003), поэтому первый же `>` в загружаемой BF-программе завершит загрузку. Рабочий протокол сейчас такой: `ISA1`, программа, `ISA0`, `EOT`. При этом `ISA1`/`ISA0` попадут в память. Это надо учесть при решении OPEN-003 и в загрузчиках (REQ-LOAD-014).

## 6. Тесты

`bfutils/dpcrun/test/test_dpcrun.cpp`, без внешних зависимостей, запуск через `ctest`:

| Группа | Тесты | Требования |
|---|---|---|
| Загрузчик | таблица символов, комментарии и NOP, обратное преобразование | REQ-IPV2-005 |
| Сбросы | включение, Hard/Soft Reset, потеря грязного счётчика, первая выборка без инкремента | REQ-RST-001/003/006/007/012, REQ-BOOT-002 |
| Общие | HALT и сдвиг IP, ISA0/ISA1, NOP-коды, все 32 комбинации | REQ-ISA-002..004, REQ-CTLV2-006, REQ-VER-022 |
| BF, данные | переходы 0..255 и 0..29999/99999, MemLock, выгрузка на `>`, ленивое чтение, устаревший `tx`, CLRD, LOAD, STORE (копирование), CLRML, COUT, CIN с эхом и ожиданием | REQ-ML-001..009, REQ-ISA-BF-001..006, REQ-VER-016/017 |
| Циклы | остановка на парной скобке, вложенность, одно чтение на `AP_TEST`, Debug-циклы по AP, глубина 99, переполнение 100 (до шага, счётчик остаётся на 99), повторное переполнение со 99, CLRL, одиночная скобка, промотка через ПЗУ | REQ-ISA-DEBUG-001..003, REQ-CNT-007, REQ-VER-013/021 |
| Debug ISA | BELL, BellOnHALT, CLRI, CLRA, CLRD, HRST с автозапуском загрузчика, SRST | REQ-ISA-DEBUG-004..009, REQ-VER-015 |
| SOT/EOT | загрузка за SOT, переход через 99999 → 0, защита ПЗУ, загрузка с пульта, EOT без сброса, ISA1 во время загрузки | REQ-LOAD-001..009, REQ-VER-018 |
| Программы | загрузчик очищает всю память данных, Hello World, Pi и 99 077 обращений | REQ-BOOT-003/005, REQ-VER-019 |

Тесты проверяют **модель**, а не RTL. Требования REQ-VER-0xx остаются открытыми, пока те же сценарии не прогнаны на RTL.

## 7. Интеграция

- **CI** — только в репозитории bfutils (решение владельца): `.github/workflows/ci.yml`, gcc и clang, `cmake` → `ctest` → `test/test.sh`. Мёртвый `.travis.yml` удалён. `cmake_minimum_required` поднят с 3.1 до 3.10: CMake 4.x отказывается конфигурировать проекты с минимумом ниже 3.5. Ветка clang локально не проверялась, компилятора на узле нет.
- **Verilator-тестбенч** `rtl/tests/DekatronPC.sv/DekatronPC_tb.cpp` переведён на новый интерфейс. Шаг RTL — проход `MachineCtrl` через `S_DECODE` до `S_IDLE`/`S_HALT`. Сравниваются IRET, IP, AP, `tx_data_bcd`, LoopCount и вывод терминала. Символ CIN передаётся модели. В `run_tests.sh` добавлен `-GEN_EMULATOR=1`, без него IRET и LoopCount не выводятся. **Тестбенч не собирался**: полная сборка DekatronPC в Verilator тяжёлая. Проверен только синтаксис против заглушки `VDekatronPC.h`. Сравнение по-прежнему включается ключом `-s`, в `run_tests.sh` оно не включено: оно упадёт на §5.1.

## 8. Что дальше

1. Исправить §5.1 (`AP_COUT` в декодере `.`) и §5.4 (`generate_rom.py`) — правки в одну строку.
2. Направленным тестом на Icarus подтвердить или снять §5.2.
3. Решить судьбу расхождений §4: исправить RTL под TRS или TRS под RTL. После этого поправить модель и тесты.
4. Собрать Verilator-тестбенч и прогнать `-s` на Hello World и Pi (тяжёлая задача, согласовать запуск).
