radiolok/dekatronpc/rtl/DekatronPC/emulator_inspection.md

---
title: Инспекция слоя эмулятора относительно TRS v0.6
date: 2026-08-15
status: отчёт
---

# Инспекция слоя эмулятора относительно TRS v0.6

Проверены: `Emulator.sv`, `io_key_display_block.sv`, `MS6205.sv`, `Sequencer.sv`, `KeyboardOpcodeInput.sv`, `KeyToSymbol.sv`, `segment7.sv`.

Общий вывод: **слой эмулятора в текущем виде не соберётся** — интерфейс `DekatronPC` изменился. Помимо механических правок портов найдены три содержательные проблемы, из которых одна ломает индикацию памяти, а другая противоречит физике сбросов.

---

## 1. Блокирующее: несовместимость интерфейса `DekatronPC`

`Emulator.sv:258` инстанцирует `DekatronPC` по прежнему списку портов. Расхождения:

| Было | Стало | Действие |
|---|---|---|
| `SoftRst_n`, `HardRst_n` (актив. нулём) | `SoftRstKey`, `HardRstKey` (актив. единицей) | инвертировать источники |
| — | `rst_n` (сброс логики, отдельно) | завести новый источник, см. §2 |
| `state[2:0]` | `state[3:0]` | расширить в трёх файлах, см. §4 |
| `ifdef EMULATOR` | параметр `EN_EMULATOR` | задать при инстанцировании |
| — | `BellOnCIN`, `BellOnHALT`, `BellOnError` | завести тумблеры |
| — | `Bell`, `LoopOverflow` | вывести на индикацию |

Приложение B в TRS фиксирует сигнатуру `Emulator ↔ DekatronPC` как контракт; по правилу из того же приложения это breaking change, требующий ревизии документа.

---

## 2. Содержательное: сброс машины дотягивается до периферии индикации

```systemverilog
assign Rst_n = SoftRst_n & HardRst_n;   // Emulator.sv:171
```

Далее этот `Rst_n` идёт во **все** блоки эмулятора: делители тактов,
`io_key_display_block`, `io_register_block`, UART, Consul, `FirmwareLoader`.

Сам по себе общемашинный характер сброса верен: и программный, и аппаратный
сброс приводят в исходное состояние всю машину — счётчики, обе линии, верхний
автомат, режим набора команд. Отличаются они только тем, какой адрес окажется
в счётчике инструкций и какой набор команд включится после снятия
(REQ-RST-001..016). Здесь менять нечего.

Неверно другое: этот же сигнал перезапускает **периферию индикации**.
Нажатие кнопки сброса на пульте сейчас останавливает тактовые делители,
сбрасывает секвенсор MS6205 и ИН-12, роняет UART и Consul. В реальной машине
кнопка сброса счётчиков генератор тактов не останавливает и индикацию не гасит.

**Требуется развести два разных сброса:**

| Сигнал | Источник | Куда идёт |
|---|---|---|
| `rst_n` — сброс логики | `KEY[0]`, включение питания | делители тактов, индикация, UART, Consul, ввод-вывод, и он же в `DekatronPC` как сброс логики |
| `SoftRstKey` / `HardRstKey` | кнопки пульта | только в `DekatronPC`, где реле времени превращает их в импульсы по катодам |

`RstTimeRelay` внутри `DekatronPC` выполняет аппаратный сброс при включении
(`RST_ON_POWERUP`), поэтому отдельного стартового `HardRst_n` в эмуляторе
больше не требуется.

### Исправление в RTL по итогам этого разбора

Проверка вскрыла пробел на стороне машины: `MachineCtrl` **не видел** сброса,
пришедшего с пульта. Реле срабатывало, счётчики и обе линии сбрасывались, а
верхний автомат продолжал выполнять текущую инструкцию и не обновлял режим
набора команд. Реагировал он только на сброс, который сам же и запросил
инструкцией HRST/SRST.

Исправлено: в `MachineCtrl` добавлены входы `soft_rst`/`hard_rst`, и реакция
на них общая для обоих источников — автомат переходит в ожидание снятия
сброса, сбрасывает режим загрузки, пошаговый режим и флаг ошибки, а после
снятия выставляет набор команд по типу сброса.

## 3. Содержательное: окно памяти на MS6205 показывает нули на 38% позиций

`MS6205.sv:151` формирует адрес второго порта памяти программ:

```systemverilog
ipAddress1[2*DEKATRON_WIDTH-1:0] <= ms6205Pos;   // ms6205Pos — ДВОИЧНЫЙ счётчик 0..159
```

Прежняя память принимала BCD и сама гнала его через `BcdToBinEnc`, поэтому «неправильный BCD» давал пусть и смещённый, но существующий адрес. Банковая память (REQ-MEMV2-003) адресуется тетрадами напрямую: тетрада больше 9 не выбирает ни одного банка, чтение возвращает нули.

Посчитано по диапазону `ms6205Pos = 0..159`:

| Окно | Затронуто позиций | Доля |
|---|---|---|
| Память программ (`ipAddress1[7:0] <= ms6205Pos`) | 60 из 160 | 38% |
| Память данных (`apAddress1[3:0] <= ms6205Pos[6:3]`) | 48 из 160 | 30% |

То есть более трети экрана окна памяти будет пустой.

**Требуется** преобразование `ms6205Pos` из двоичного в BCD перед подстановкой в адрес. Модуль `BinToBcd` в проекте есть, но он позиционный (one-hot→BCD) и для этого не годится — нужен двоичный→BCD, либо сделать `ms6205Pos` изначально BCD-счётчиком с шагом по тетрадам.

Второй вариант предпочтительнее: он заодно делает раскладку окна совпадающей с раскладкой банков, то есть строка экрана = строка банка.

---

## 4. Механическое: ширина шины состояния

`state` верхнего автомата вырос с 3 до 4 бит (14 состояний против прежних восьми). Правки:

- `Emulator.sv:117` — `output logic [2:0] DPC_currentState`
- `io_key_display_block.sv:23` — `input wire [2:0] DPC_currentState`
- `MS6205.sv:28` — `input wire [2:0] DPC_State`

В `MS6205` сигнал помечен `UNUSEDSIGNAL` и фактически не используется, так что правка чисто формальная. В `Sequencer.sv` собственный `state[2:0]` — это состояние секвенсора индикации, к машине отношения не имеет, трогать не нужно.

---

## 5. Потеряна функция: переключение программ по клавише

`key_next_app_i` прежде шёл в `IpLine`, который по нему сбрасывался и подхватывал следующую прошивку. В новом `IpLine` этой функции нет — она не относится к выборке инструкций.

Сейчас порт в `DekatronPC` присутствует, но не разведён: нажатие клавиши не делает ничего.

**Требуется** реализовать в слое эмулятора: по нажатию переключать `selector` между `FirmwareLoader`-ами и выдавать импульс на `SoftRstKey`.

---

## 6. Ширина данных второго порта памяти данных

`Ram` отдаёт `dbg_data` шириной 10 бит (ячейка `{hundreds[1:0], tens, ones}`), а `ApData1` в эмуляторе — 12 бит. В `DekatronPC` расширение нулями уже сделано (REQ-DATA-005), правок в эмуляторе не требуется. Отмечено, чтобы при отладке не искали расхождение.

---

## 7. Открытые пункты TRS, подтверждённые инспекцией

### OPEN-011 — тумблеры захардкожены

```systemverilog
assign SoftRstOnEOT = 1'b1;    // Emulator.sv:165
assign RunOnHardRst = 1'b0;
assign RunOnSoftRst = 1'b0;
logic EchoMode = 1'b1;         // Emulator.sv:239
```

Плюс три новых тумблера `BellOn*` без источника. Панель управления по-прежнему не реализована (REQ-PANEL-004..008).

### REQ-UART-006 — параметры UART захардкожены

`Emulator.sv:509–541`: `BAUD_RATE(110)`, `DATA_WIDTH(7)`, `CLK_FREQ(1000000)` заданы константами. Тумблеров скорости нет.

### REQ-CLK-004 — правила CDC отсутствуют, есть конкретный риск

`Emulator.sv:470–488`: сигнал `consul_tx_rdy_slow` формируется в домене `Clock_100Hz`, а защёлкивается в домене `Clock_1MHz` одним триггером `consul_tx_rdy_slow_old`. Синхронизатора нет — это прямой риск метастабильности на границе доменов, который TRS требует закрыть.

### REQ-IO-001 — старая шина ввода-вывода

`io_register_block` отвергнут в TRS, но по-прежнему инстанцирован (2 платы из 16). Ожидается замена на LVDS-платы (REQ-IO-002..006).

### OPEN-015 — банковая память не влезет в ПЛИС

Практический блокер именно для эмулятора: `DekatronPC` инстанцирует `Ram` на 100 000 ячеек и `IpMemory` на 100 000 — это 1000 банков каждая. На Cyclone V столько блоков памяти нет. Пока не появится плоская реализация с тем же интерфейсом, эмулятор не синтезируется.

---

## 8. Замечания, не требующие правок

**Загрузка программ идёт в Debug ISA.** `KeyboardOpcodeInput` вызывает `SymbolToOpcode(Symbol, 1'b0)` с жёстко заданным нулём, а признак конца передачи в `IpLine` проверяется как `{insn_mode, insn_in} == INSN_EOT`, где `EOT` — код Debug-набора. Значит загрузка обязана начинаться в Debug ISA, иначе опкод 4 будет истолкован как `AINC` и передача не завершится. Поведение унаследовано без изменений, но зависимость неочевидная и стоит отражения в документации.

**`apData` для индикации** заведён на `tx_data_bcd`. В новом `ApLine` это `MemLock ? счётчик : копия ячейки`, то есть по-прежнему актуальное значение текущей ячейки. Индикация остаётся корректной.

---

## Порядок работ

1. Разделить `rst_n` и кнопки сброса (§2) — иначе поведение машины будет неверным даже после того, как всё соберётся.
2. Привести инстанцирование `DekatronPC` к новому интерфейсу (§1, §4).
3. Исправить формирование адреса окна памяти в `MS6205` (§3).
4. Вернуть переключение программ (§5).
5. Решить OPEN-015 — без него эмулятор не синтезируется.
6. Закрыть OPEN-011 и REQ-UART-006 панелью тумблеров.
7. Поставить синхронизатор на границе Consul (REQ-CLK-004).
