radiolok/dekatronpc/img/magnetic_punch_card/DSC00021.JPG

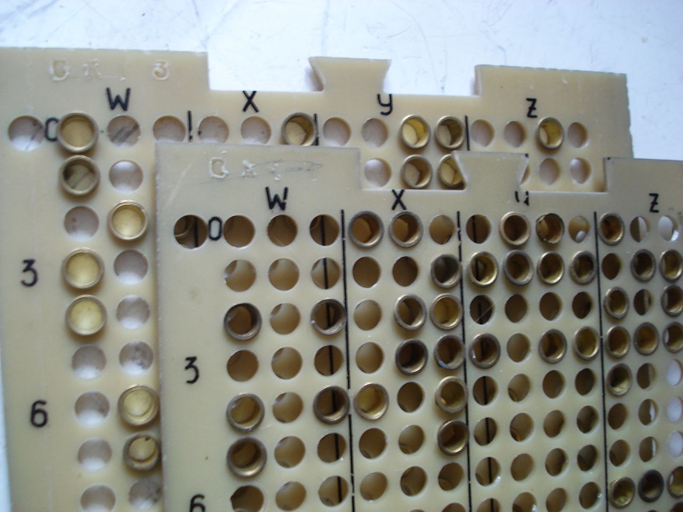
img/magnetic_punch_card/DSC00021.JPG
