radiolok/dekatronpc/img/magnetic_punch_card/DSC00022.JPG

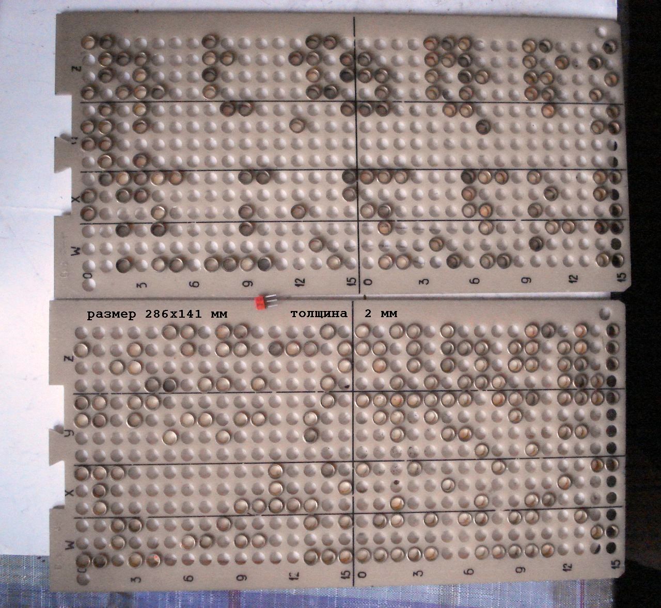
img/magnetic_punch_card/DSC00022.JPG
