radiolok/dekatronpc/img/magnetic_punch_card/DSC00024.JPG

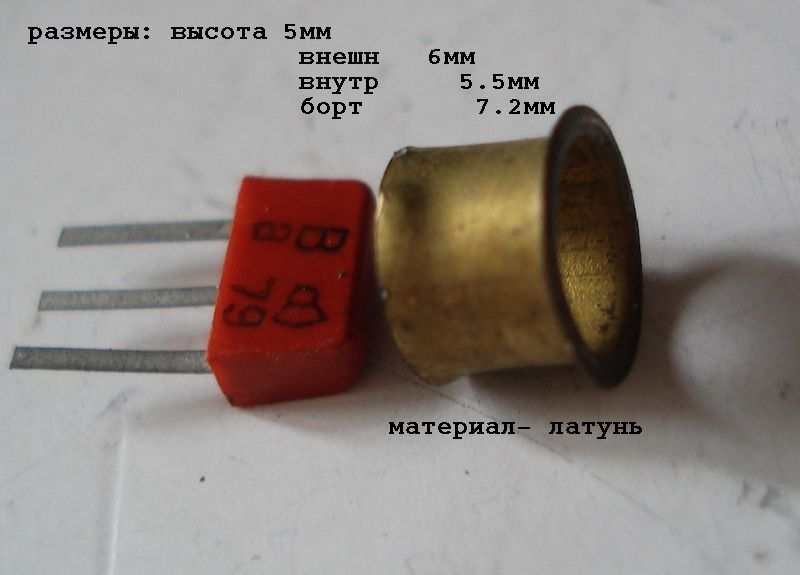
img/magnetic_punch_card/DSC00024.JPG
