radiolok/dekatronpc/sch/spice/long-tailed_or.asc

C1: cap; 4700pF
C2: cap; 4700pF
C3: cap; 20pF
C4: cap; 0.1µF
R1: res; 1k
R2: res; 10
R3: res; 1k
R4: res; 2.2k
R5: res; 1k
R6: res; 1k
R7: res; 1k
R8: res; 1k
R9: res; 100k
R10: res; 2.2k
R11: res; 2.2k
R12: res; 100k
R13: res; 98k
R14: res; 10k
U1: triode; 6N3P-E
U2: triode; 6N3P-E
U3: triode; 6N3P-E
U4: triode; 6N3P-E
V1: voltage; PULSE(-10 10 0 10ns 10ns 0.5us 1us)
V2: voltage; 200
V3: voltage; 20
V4: voltage; -160
V6: voltage; 40
V7: voltage; 20
Named nets: 0, -60V, 200V
.SUBCKT 6N3P-E  1 2 3 ; P G C (Triode) 16-Nov-2001
+ PARAMS: MU=31.33  EX=1.979  KG1=1920.5  KP=211.72 
+ KVB=300.0  VCT=0.00 RGI=1k
+ CCG=2.5P  CGP=1.3P CCP=1.4P
E1 7 0 VALUE=
+{V(1,3)/KP*LN(1+EXP(KP*(1/MU+(V(2,3)+VCT)/SQRT(KVB+V(1,3)*V(1,3)))))}
RE1 7 0 1G
G1 1 3 VALUE={(PWR(V(7),EX)+PWRS(V(7),EX))/KG1}
RCP 1 3 1G    ; TO AVOID FLOATING NODES IN MU-FOLLOWER
C1 2 3 {CCG}  ; CATHODE-GRID; 
C2 2 1 {CGP}  ; GRID-PLATE; 
C3 1 3 {CCP}  ; CATHODE-PLATE; 
D3 5 3 DX     ; FOR GRID CURRENT
R1 2 5 {RGI}  ; FOR GRID CURRENT
.MODEL DX D(IS=1N RS=1 CJO=10PF TT=1N)
.ENDS
.tran 2020us
