radiolok/dekatronpc/sch/spice/long-tailed_pair_pentode.asc

C2: cap; 4700pF
C3: cap; 4700pF
C4: cap; 100pF
C5: cap; 1µF
C6: cap; 1µF
C7: cap; 100pF
C8: cap; 100pF
C9: cap; 1µF
C10: cap; 1µF
L2: ind; 10µH
L3: ind; 10µH
L4: ind; 10µH
R1: res; 1k
R2: res; 8.2k
R4: res; 2.2k
R5: res; 1k
R6: res; 100k
R7: res; 2.2k
R8: res; 82k
R9: res; 100k
R10: res; 100
R11: res; 100
R12: res; 330k
R13: res; 10k
R14: res; 100k
R15: res; 100k
R16: res; 1k
R17: res; 2.2k
R18: res; 1k
R19: res; 100k
R20: res; 2.2k
R21: res; 100
R22: res; 100
R23: res; 200k
R24: res; 82k
U1: pentode1; 6J4
U2: pentode1; 6J4
U3: pentode1; 6J4
U4: pentode1; 6J4
V1: voltage; PULSE(-22 10 0 10ns 10ns 2.5us 5us)
V2: voltage; 200
V3: voltage; 60
V4: voltage; 200
Named nets: 0, -60V, 200V, 150
.SUBCKT 6J4  1 2 3 4 ; P G1 C G2 (Pentode) 15-Dec-2006
+ PARAMS: MU= 47.56  EX= 1.358  KG1= 430  KP=177.6   KC=112
+ KVB=  15.0  VCT=  0.00  RGI=1k
+ CCG=9P  CPG1=0.015P CCP=5P
RE1  7 0  1MEG    
E1   7 0  VALUE=  ; E1 BREAKS UP LONG EQUATION FOR G1.
+{V(4,3)/KP*LN(1+EXP((1/MU+V(2,3)/V(4,3))*KP))}
G1   1 3  VALUE={(PWR(V(7),EX)+PWRS(V(7),EX))/KG1*ATAN(V(1,3)/KVB)}
G2   4 3  VALUE={STP(((EXP(EX*(LN((V(4,3)/MU)+V(2,3)))))/KC)-((PWR(V(7),EX)+PWRS(V(7),EX))/KG1*ATAN(V(1,3)/KVB)))
+*(((EXP(EX*(LN((V(4,3)/MU)+V(2,3)))))/KC)-((PWR(V(7),EX)+PWRS(V(7),EX))/KG1*ATAN(V(1,3)/KVB)))}
RCP  1 3  1G      ; FOR CONVERGENCE
C1   2 3  {CCG}   ; CATHODE-GRID 1
C2   1 2  {CPG1}  ; GRID 1-PLATE
C3   1 3  {CCP}   ; CATHODE-PLATE
R1   2 5  {RGI}   ; FOR GRID CURRENT
D3   5 3  DX      ; FOR GRID CURRENT
.MODEL DX D(IS=1N RS=1 CJO=10PF TT=1N)
.ENDS
.tran 0 220us 200us
