radiolok/dekatronpc/sch/spice/RS-trigger.asc

C1: cap; 2.5pF
C2: cap; 2.5pF
Q1: npn
Q2: npn
R1: res; 22k
R2: res; 22k
R3: res; 10k
R4: res; 470k
R5: res; 330k
R7: res; 330k
R8: res; 470k
R9: res; 10k
U1: triode; 6N3P-E
U2: triode; 6N3P-E
V1: voltage; PULSE(0 5 2us 0 0 1us 10us)
V2: voltage; 200
V3: voltage; 100
V4: voltage; PULSE(0 5 7us 0 0 1us 10us)
Named nets: 0, -100v, 150V, Q, !Q
.SUBCKT 6N3P-E  1 2 3 ; P G C (Triode) 16-Nov-2001
+ PARAMS: MU=31.33  EX=1.979  KG1=1920.5  KP=211.72 
+ KVB=300.0  VCT=0.00 RGI=1k
+ CCG=2.5P  CGP=1.3P CCP=1.4P
E1 7 0 VALUE=
+{V(1,3)/KP*LN(1+EXP(KP*(1/MU+(V(2,3)+VCT)/SQRT(KVB+V(1,3)*V(1,3)))))}
RE1 7 0 1G
G1 1 3 VALUE={(PWR(V(7),EX)+PWRS(V(7),EX))/KG1}
RCP 1 3 1G    ; TO AVOID FLOATING NODES IN MU-FOLLOWER
C1 2 3 {CCG}  ; CATHODE-GRID; 
C2 2 1 {CGP}  ; GRID-PLATE; 
C3 1 3 {CCP}  ; CATHODE-PLATE; 
D3 5 3 DX     ; FOR GRID CURRENT
R1 2 5 {RGI}  ; FOR GRID CURRENT
.MODEL DX D(IS=1N RS=1 CJO=10PF TT=1N)
.ENDS
.tran 20us
