radiolok/dekatronpc/rtl/Emulator/Emulator.sv

module Emulator #(
    parameter DIVIDE_TO_01US = 28'd5,
    parameter DIVIDE_TO_1MS = 28'd1000,
    parameter DIVIDE_TO_4MS = 28'd3000,
    parameter DIVIDE_TO_1S = 28'd1000,
    parameter BOARDS = 16,
    parameter INSTALLED_BOARDS = 2
)(
    /* verilator lint_off UNUSEDSIGNAL */
	//////////// CLOCK //////////
	input 		          		FPGA_CLK_50,//V11
	input 		          		FPGA_CLK2_50,//Y13
	input 		          		FPGA_CLK3_50,//E11
	/* 3.3-V LVTTL */

	/*
	KEY0 - AH17
	KEY1 - AH16
	*/
	input				[1:0]			KEY,
	/* verilator lint_off UNDRIVEN */
    output			[7:0]			LED,
    /* verilator lint_on UNDRIVEN */
	/*
	SW0 - L10
	SW1 - L9
	SW2 - H6
	SW3 - H5
	*/
	input				[3:0]			SW,
    /* verilator lint_on UNUSEDSIGNAL */

	 /*
	 D0 - AH3
	 D1 - AH2
	 D2 - AF4
	 D3 - AG6
	 D4 - AF5
	 D5 - AE4
	 D6 - T13
	 */
	input [6:0] keyboard_data_in,

	input ms6205_ready,//T11
	output ms6205_write_addr_n,//Y5
	output ms6205_write_data_n,//U11
   output ms6205_marker,//AG5

	output in12_write_anode,//T8
	output in12_write_cathode,//T12
	output in12_clear_n,//AH5

	output keyboard_write,//AH6
	output keyboard_clear,//AH4

    input rx,//Y15
    output tx,//AA15

	/*
	D0 - V12
	D1 - AF7
	D2 - W12
	D3 - AF8
	D4 - Y8
	D5 - AB4
	D6 - W8
	D7 - Y4
	*/
	output [7:0] emulData,

    output logic Clock_1Hz, //AF18 GPIO1.24
    output logic Clock_1KHz, //AG23 GPIO1.22
    output logic Clock_10KHz,
    output logic Clock_1MHz, //AF25 GPIO1.20

	 /*
	 A0 - AA18
	 A1 - AC22
	 A2 - AD23
	 A3 - AE23
	 */
    output logic [3:0] io_address,
    /*
	 EN1 - AG21
	 EN2 - AH18
	 */
	 output logic [1:0] io_enable_n,
	 /*
	 D0 - AE20
	 D1 - AD19
	 D2 - AD20
	 D3 - AE24
	 D4 - AH22
	 D5 - AF22
	 D6 - AH21
	 D7 - AH19
	 */
    inout [7:0] io_data,

    output logic pwr_selector,
    input logic [3:0] selector,

`ifdef VERILATOR
    output logic [IP_DEKATRON_NUM*DEKATRON_WIDTH-1:0] IpAddress,
    output logic [AP_DEKATRON_NUM*DEKATRON_WIDTH-1:0] ApAddress,
    output logic [LOOP_DEKATRON_NUM*DEKATRON_WIDTH-1:0] LoopCount,
    output logic [DATA_DEKATRON_NUM*DEKATRON_WIDTH-1:0] tx_data_bcd,

    /* verilator lint_off UNUSEDSIGNAL */
    input logic [INSN_WIDTH-1:0] InsnIn,
    input logic InsnInValid,
    output logic InsnInReady,
    output logic InsnInReadEnable,
    /* verilator lint_on UNUSEDSIGNAL */
`endif

    output logic [3:0] DPC_currentState
);

assign LED[0] = Rst_n;
assign LED[1] = Clock_1Hz;
assign LED[2] = Clock_1KHz;
assign LED[6:3] = selector;

`ifndef VERILATOR
    logic [IP_DEKATRON_NUM*DEKATRON_WIDTH-1:0] IpAddress;
    logic [AP_DEKATRON_NUM*DEKATRON_WIDTH-1:0] ApAddress;
    logic [LOOP_DEKATRON_NUM*DEKATRON_WIDTH-1:0] LoopCount;
    logic [DATA_DEKATRON_NUM*DEKATRON_WIDTH-1:0] tx_data_bcd;
`endif

/* verilator lint_off UNUSEDSIGNAL */
logic [31:0] IRET;
logic [39:0] keysCurrentState;
logic [7:0] keyboardSymbol;
/* verilator lint_on UNUSEDSIGNAL */

logic keyHalt;
logic keyRun;
logic keyStep;
logic keyNextApp;
logic keyNextIp;
logic keyPrevIp;
logic keyInsnLoadingStart;
logic keyInsnLoadingStop;
logic Rst_n;
logic SoftRst_n;
logic HardRst_n;
logic RunOnSoftRst;
logic RunOnHardRst;
logic SoftRstOnEOT;

assign keyHalt = keysCurrentState[KEYBOARD_HALT_KEY];
assign keyRun = keysCurrentState[KEYBOARD_RUN_KEY];
assign keyStep = keysCurrentState[KEYBOARD_STEP_KEY];
assign keyNextApp = keysCurrentState[KEYBOARD_NONAME_KEY];
assign keyNextIp = keysCurrentState[KEYBOARD_ARROW_RIGHT_KEY]
                | keysCurrentState[KEYBOARD_INC_KEY];
assign keyPrevIp = keysCurrentState[KEYBOARD_ARROW_LEFT_KEY]
                | keysCurrentState[KEYBOARD_DEC_KEY];
assign keyInsnLoadingStart = keysCurrentState[KEYBOARD_IP_KEY];
assign keyInsnLoadingStop = keysCurrentState[KEYBOARD_AP_KEY]
                        | keysCurrentState[KEYBOARD_DATA_KEY]
                        | keysCurrentState[KEYBOARD_LOOP_KEY];
assign SoftRstOnEOT = 1'b1;
assign RunOnHardRst = 1'b0;
assign RunOnSoftRst = 1'b0;

assign SoftRst_n = ~keysCurrentState[KEYBOARD_SOFT_RST_KEY];
assign HardRst_n = KEY[0] & ~keysCurrentState[KEYBOARD_HARD_RST];
assign Rst_n = SoftRst_n & HardRst_n;

logic Clock_10MHz;
/* verilator lint_off UNUSEDSIGNAL */
logic [INSN_WIDTH - 1:0] Insn;
/* verilator lint_on UNUSEDSIGNAL */

logic [INSN_WIDTH - 1:0] KeyboardInsn;
logic KeyboardInsnValid;
logic KeyboardInsnReady;
logic KeyboardReadEnable;

logic [INSN_WIDTH - 1:0] FirmwareInsn_1;
logic FirmwareReadEnable_1;
logic FirmwareValid_1;
logic FirmwareReady_1;

logic [INSN_WIDTH - 1:0] FirmwareInsn_2;
logic FirmwareReadEnable_2;
logic FirmwareValid_2;
logic FirmwareReady_2;

logic [INSN_WIDTH - 1:0] InsnInInternal;
logic InsnInReadyInternal;
logic InsnInValidInternal;
logic InsnInLoading;

logic InsnLoadingStartInternal;
logic InsnLoadingStopInternal;

generate
    if (DIVIDE_TO_01US == 1) begin : clock_emulator
        assign Clock_10MHz = FPGA_CLK_50;
    end
    else begin : clock_fpga
    ClockDivider #(.DIVISOR({DIVIDE_TO_01US})) clock_divider_10MHz(
        .Rst_n(Rst_n),
        .clock_in(FPGA_CLK_50),
        .clock_out(Clock_10MHz)
    );
    end
endgenerate

ClockDivider #(
    .DIVISOR(10)
) clock_divider_1MHz(
    .Rst_n(Rst_n),
	.clock_in(Clock_10MHz),
	.clock_out(Clock_1MHz)
);

ClockDivider #(
    .DIVISOR({DIVIDE_TO_1MS}),
    .DUTY_CYCLE(80)
) clock_divider_1KHz(
    .Rst_n(Rst_n),
	.clock_in(Clock_1MHz),
	.clock_out(Clock_1KHz)
);

ClockDivider #(
    .DIVISOR({DIVIDE_TO_1S})
) clock_divider_1Hz(
    .Rst_n(Rst_n),
	.clock_in(Clock_1KHz),
	.clock_out(Clock_1Hz)
);

logic EchoMode = 1'b1;

logic [DATA_DEKATRON_NUM*DEKATRON_WIDTH-1:0] rx_data_bcd;

logic [7:0] tx_data;
logic [7:0] rx_data;
BcdToAscii bcdToAscii(tx_data_bcd, tx_data);

AsciiToBcd asciiToBcd(rx_data, rx_data_bcd);

/* verilator lint_off UNDRIVEN */
/* verilator lint_off UNUSEDSIGNAL */
logic [AP_DEKATRON_NUM*DEKATRON_WIDTH-1:0] ApAddress1;
/* verilator lint_on UNDRIVEN */
logic [DATA_DEKATRON_NUM*DEKATRON_WIDTH-1:0] ApData1;
/* verilator lint_on UNUSEDSIGNAL */
logic [IP_DEKATRON_NUM*DEKATRON_WIDTH-1:0] IpAddress1;
logic [INSN_WIDTH-1:0] RomData1;

DekatronPC dekatronPC(
    .IpAddress(IpAddress),
    .ApAddress(ApAddress),
    .LoopCount(LoopCount),
    .hsClk(Clock_10MHz),
    .Clk(Clock_1MHz),
    .rst_n(Rst_n),
    .SoftRstKey(~SoftRst_n),
    .HardRstKey(~HardRst_n),
    .Halt(keyHalt),
    .Run(keyRun),
    .InsnIn(InsnInInternal),
    .InsnInValid(InsnInValidInternal),
    .InsnInReady(InsnInReadyInternal),
    .InsnInLoading(InsnInLoading),
    .EchoMode(EchoMode),
    .RunOnHardRst(RunOnHardRst),
    .RunOnSoftRst(RunOnSoftRst),
    .SoftRstOnEOT(SoftRstOnEOT),
    .BellOnCIN(1'b0),
    .BellOnHALT(1'b0),
    .BellOnError(1'b0),
    .tx_data_bcd(tx_data_bcd),
    .tx_vld(tx_vld),
    .tx_rdy(tx_rdy),
    .rx_data_bcd(rx_data_bcd),
    .rx_vld(rx_vld),
    .rx_rdy(rx_rdy),
    .Step(keyStep),
    .keyNextIp(keyNextIp),
    .keyPrevIp(keyPrevIp),
    .InsnLoadingStart(InsnLoadingStartInternal),
    .InsnLoadingStop(InsnLoadingStopInternal),
    .key_next_app_i(keyNextApp),
    .IRET(IRET),
    .IpAddress1(IpAddress1),
    .ApAddress1(ApAddress1),
    .ApData1(ApData1),
    .RomData1(RomData1),
    .state(DPC_currentState),
    .IsHalted(),
    .Bell(),
    .LoopOverflow(),
    .Insn(Insn)
);

io_key_display_block #(
    .DIVIDE_TO_4MS(DIVIDE_TO_4MS)
)ioKeyDisplayBlock(
    .keyboard_data_in(keyboard_data_in),
    .ms6205_ready(ms6205_ready),
    .ms6205_write_addr_n(ms6205_write_addr_n),
    .ms6205_write_data_n(ms6205_write_data_n),
    .ms6205_marker(ms6205_marker),
    .in12_write_anode(in12_write_anode),
    .in12_write_cathode(in12_write_cathode),
    .in12_clear_n(in12_clear_n),
    .keyboard_write(keyboard_write),
    .keyboard_clear(keyboard_clear),
    .keyboard_keysCurrentState(keysCurrentState),
    .keyboard_symbol(keyboardSymbol),
    .emulData(emulData),
    .ipAddress(IpAddress),
    .ipAddress1(IpAddress1),
    .RomData1(RomData1),
    .apAddress1(ApAddress1),
    .apData1(ApData1),
    .apData(tx_data_bcd),
    .loopCounter(LoopCount),
    .apAddress(ApAddress),
    .Clock_1s(Clock_1Hz),
    .Clock_1ms(Clock_1KHz),
    .Clock_1us(Clock_1MHz),
    .Rst_n(Rst_n),
    .tx_data(tx_data),
    .tx_vld(tx_vld),
    .DPC_currentState(DPC_currentState),
    .InsnLoading(InsnInLoading)
);

/* verilator lint_off UNUSEDSIGNAL */
logic [127:0] io_input_regs;
/* verilator lint_on UNUSEDSIGNAL */

/* verilator lint_off UNDRIVEN */
logic [127:0] io_output_regs;
/* verilator lint_on UNDRIVEN */

//logic Clock_10KHz;

ClockDivider #(
    .DIVISOR(100)
) clock_divider_100KHz(
    .Rst_n(Rst_n),
	.clock_in(Clock_1MHz),
	.clock_out(Clock_10KHz)
);


io_register_block #(
    .BOARDS(BOARDS),
    .INSTALLED_BOARDS(INSTALLED_BOARDS)
)IoRegisterBlock(
    .Clk(Clock_10KHz),
	.Rst_n(Rst_n),
    .addr_o(io_address),
    .enable_n_o(io_enable_n),
    .data_io(io_data),
    .regs_in_o(io_input_regs),
    .regs_out_i(io_output_regs)
);



logic                        tx_rdy  ;
logic                        tx_vld  ;
//rx signal
logic                          rx_vld  ;
logic                          rx_rdy  ;
// Источник терминала до буфера приёма
logic [7:0]                    term_rx_data;
logic                          term_rx_vld;
logic                          term_rx_vld_old;


logic [7:0] uart_rx_data;
logic       uart_tx_vld;
logic       uart_tx_rdy;
logic       uart_rx_vld;

logic [7:0] consul_rx_data;
logic       consul_tx_vld;
logic       consul_tx_rdy;
logic       consul_rx_vld;

assign pwr_selector = 1'b1;

always_comb begin
    KeyboardReadEnable = 1'b0;
    KeyboardInsnReady = 1'b0;
    FirmwareReadEnable_1 = 1'b0;
    FirmwareReady_1 = 1'b0;
    FirmwareReadEnable_2 = 1'b0;
    FirmwareReady_2 = 1'b0;
`ifdef VERILATOR
    InsnInReadEnable = 1'b0;
    InsnInReady = 1'b0;
`endif
    InsnLoadingStartInternal = 1'b0;
    InsnLoadingStopInternal = 1'b0;

    case (selector)
    4'b1010: begin
        InsnInInternal = KeyboardInsn;
        InsnInValidInternal = KeyboardInsnValid;
        KeyboardInsnReady = InsnInReadyInternal;
        KeyboardReadEnable = InsnInLoading;

        InsnLoadingStartInternal = keyInsnLoadingStart;
        InsnLoadingStopInternal = keyInsnLoadingStop;
    end
    4'b1001: begin
        InsnInInternal = FirmwareInsn_1;
        InsnInValidInternal = FirmwareValid_1;
        FirmwareReady_1 = InsnInReadyInternal;
        FirmwareReadEnable_1 = InsnInLoading;
    end
    4'b1000: begin
        InsnInInternal = FirmwareInsn_2;
        InsnInValidInternal = FirmwareValid_2;
        FirmwareReady_2 = InsnInReadyInternal;
        FirmwareReadEnable_2 = InsnInLoading;
    end
    default: begin
`ifdef VERILATOR
        InsnInInternal = InsnIn;
        InsnInValidInternal = InsnInValid;
        InsnInReady = InsnInReadyInternal;
        InsnInReadEnable = InsnInLoading;
`else
        InsnInInternal = 4'b0;
        InsnInValidInternal = 1'b0;
`endif
    end
    endcase
end

always_comb begin
    if (selector == 4'b0001) begin
        uart_tx_vld  = tx_vld;
        consul_tx_vld  = '0;
        tx_rdy  = uart_tx_rdy;
        term_rx_data = uart_rx_data;
        term_rx_vld  = uart_rx_vld;
    end else begin
        uart_tx_vld  = '0;
        consul_tx_vld  = tx_vld;
        tx_rdy  = consul_tx_rdy;
        term_rx_data = consul_rx_data;
        term_rx_vld  = consul_rx_vld;
    end
end

// Буфер приёма: DekatronPC не защёлкивает символ и пишет счётчик данных
// прямо с rx_data_bcd, поэтому символ держится здесь до rx_vld & rx_rdy
// (REQ-UART-008). Приём по фронту: kb_data_vld консула медленный и
// длится много тактов 1 МГц.
always @(posedge Clock_1MHz, negedge Rst_n) begin
    if (~Rst_n) begin
        rx_data         <= 8'h0;
        rx_vld          <= 1'b0;
        term_rx_vld_old <= 1'b0;
    end else begin
        term_rx_vld_old <= term_rx_vld;
        if (rx_vld & rx_rdy)
            rx_vld <= 1'b0;
        else if (~rx_vld & term_rx_vld & ~term_rx_vld_old) begin
            rx_data <= term_rx_data;
            rx_vld  <= 1'b1;
        end
    end
end

logic Clock_100Hz;
ClockDivider #(
    .DIVISOR(10)
) clock_divider_100Hz(
    .Rst_n(Rst_n),
	.clock_in(Clock_1KHz),
	.clock_out(Clock_100Hz)
);

logic [15:0] consul_regs_in;
logic [9:0] consul_regs_out;

assign io_output_regs[31:16]  = 16'hAA55;


assign consul_regs_in = io_input_regs[15:0];
assign io_output_regs[9:0] = consul_regs_out;

logic consul_tx_rdy_slow;
logic consul_tx_vld_slow;
logic consul_tx_rdy_slow_old;

always @(posedge Clock_1MHz, negedge Rst_n) begin
    if (~Rst_n) begin
        consul_tx_rdy_slow_old <= 1'b1;
        consul_tx_rdy <= 1'b1;
        consul_tx_vld_slow <= 1'b0;
    end else begin
        consul_tx_rdy_slow_old <= consul_tx_rdy_slow;
        if (~consul_tx_rdy_slow_old & consul_tx_rdy_slow) begin
            consul_tx_rdy <= 1'b1;
            consul_tx_vld_slow <= 1'b0;
        end
        else begin
            if (consul_tx_vld) begin
                consul_tx_rdy <= 1'b0;
                consul_tx_vld_slow <= 1'b1;
            end
        end
    end
end

consul Consul(
    .Clk(Clock_100Hz),
    .Rst_n(Rst_n),
    .regs_in(consul_regs_in),
    .regs_out(consul_regs_out),
    .print_data_i(tx_data),
    .kb_data_o(consul_rx_data),
    .print_data_vld(consul_tx_vld_slow),
    .kb_data_vld(consul_rx_vld),
    .print_data_rdy(consul_tx_rdy_slow)
);

/* verilator lint_off UNUSEDSIGNAL */
logic                          rx_pc_pass ;
/* verilator lint_on UNUSEDSIGNAL */
logic tx_n;
assign tx = ~tx_n;


uart_tx#(
    .DATA_WIDTH   ( 7   ) ,
    .PARITY_CHECK ( "NONE" ) ,
    .CLK_FREQ     ( 1000000    ) ,
    .STOP_BITS     (1),
    .BAUD_RATE    ( 110    )
)transmitter(
    .clk    ( Clock_1MHz       ),
    .rst    ( ~Rst_n       ),

    .i_vld  ( uart_tx_vld    ),
    .i_data ( tx_data[6:0]   ),

    .o_rdy  ( uart_tx_rdy    ),
    .tx     ( tx_n      )
);

uart_rx#(
    .DATA_WIDTH   ( 7   ) ,
    .PARITY_CHECK ( "NONE" ) ,
    .CLK_FREQ     ( 1000000    ) ,
    .BAUD_RATE    ( 110    )
)receiver(
    .clk     ( Clock_1MHz        ),
    .rst     ( ~Rst_n        ),

    .rx      ( ~rx         ),
    .i_rdy   ( 1'b1       ),

    .o_vld   ( uart_rx_vld     ),
    .pc_pass ( rx_pc_pass ),
    .o_data  ( uart_rx_data[6:0]    )
) ;

assign uart_rx_data[7] = 1'b0;

KeyboardOpcodeInput keyboardOpcodeInput(
    .Clk(Clock_1MHz),
    .Rst_n(Rst_n),

    .ReadEnable(KeyboardReadEnable),

    .Symbol(keyboardSymbol),
    .Opcode(KeyboardInsn),
    .Ready(KeyboardInsnReady),
    .Valid(KeyboardInsnValid)
);

FirmwareLoader #(
    .ROWS(512),
    .FW_PATH("../load_firmware_hello.hex")
) firmwareLoader_hello(
    .Clk(Clock_1MHz),
    .Rst_n(Rst_n),

    .Enable(FirmwareReadEnable_1),

    .Valid(FirmwareValid_1),
    .Ready(FirmwareReady_1),
    .InsnOut(FirmwareInsn_1)
);

FirmwareLoader #(
    .ROWS(650),
    .FW_PATH("../load_firmware_pi.hex")
) firmwareLoader_pi(
    .Clk(Clock_1MHz),
    .Rst_n(Rst_n),

    .Enable(FirmwareReadEnable_2),

    .Valid(FirmwareValid_2),
    .Ready(FirmwareReady_2),
    .InsnOut(FirmwareInsn_2)
);

endmodule
