radiolok/dekatronpc/rtl/run/text.sv

module firmware #(
///mnt/d/radiolok@oc.urlnn.ru/Projects/20180271-DekatronPC/vhdl/programs/pi/pi.bfk
parameter portSize = 18,
parameter dataSize = 4)(
/* verilator lint_off UNUSEDSIGNAL */
input wire [portSize-1:0] Address,
/* verilator lint_on UNUSEDSIGNAL */
output reg [dataSize-1:0] Data
);
always_comb
/* verilator lint_off WIDTHEXPAND */
  case(Address)
    18'h0: Data = 4'h2; //+ 
    18'h1: Data = 4'h2; //+ 
    18'h2: Data = 4'h2; //+ 
    18'h3: Data = 4'h2; //+ 
    18'h4: Data = 4'h6; //[ 
    18'h5: Data = 4'h5; //< 
    18'h6: Data = 4'h2; //+ 
    18'h7: Data = 4'h4; //> 
    18'h8: Data = 4'h4; //> 
    18'h9: Data = 4'h4; //> 
    18'h10: Data = 4'h4; //> 
    18'h11: Data = 4'h4; //> 
    18'h12: Data = 4'h4; //> 
    18'h13: Data = 4'h4; //> 
    18'h14: Data = 4'h4; //> 
    18'h15: Data = 4'h2; //+ 
    18'h16: Data = 4'h2; //+ 
    18'h17: Data = 4'h2; //+ 
    18'h18: Data = 4'h2; //+ 
    18'h19: Data = 4'h2; //+ 
    18'h20: Data = 4'h2; //+ 
    18'h21: Data = 4'h2; //+ 
    18'h22: Data = 4'h2; //+ 
    18'h23: Data = 4'h2; //+ 
    18'h24: Data = 4'h2; //+ 
    18'h25: Data = 4'h5; //< 
    18'h26: Data = 4'h5; //< 
    18'h27: Data = 4'h5; //< 
    18'h28: Data = 4'h5; //< 
    18'h29: Data = 4'h5; //< 
    18'h30: Data = 4'h5; //< 
    18'h31: Data = 4'h5; //< 
    18'h32: Data = 4'h3; //- 
    18'h33: Data = 4'h7; //] 
    18'h34: Data = 4'h4; //> 
    18'h35: Data = 4'h2; //+ 
    18'h36: Data = 4'h2; //+ 
    18'h37: Data = 4'h2; //+ 
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
    18'h13021: Data = 4'h4; //> 
    18'h13022: Data = 4'h4; //> 
    18'h13023: Data = 4'h4; //> 
    18'h13024: Data = 4'h2; //+ 
    18'h13025: Data = 4'h5; //< 
    18'h13026: Data = 4'h5; //< 
    18'h13027: Data = 4'h5; //< 
    18'h13028: Data = 4'h7; //] 
    18'h13029: Data = 4'h5; //<
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
