radiolok/dekatronpc/rtl/run/vtube_sdf.py

"""SDF delays and setup/hold checks for a Yosys netlist of vacuum-tube cells.

Writes into OUT_DIR:
  <module>.sdf  one per netlist module that holds library cells: an IOPATH
                entry for every specify path of the cell in vtube_cells.v,
                with the value from vtube_timing.json, and SETUPHOLD for the
                triggers (Icarus parses it but does not check it)
  vtube_sdf.sv  module vtube_sdf, a second simulation root (iverilog
                -s vtube_sdf): one $sdf_annotate per module instance of
                the netlist under SCOPE, a vtube_setuphold checker on every
                trigger, and a final summary line
                "VTUBE TIMING: <n> setup, <m> hold violations"

Icarus cannot find escaped instance names with '.' or '[' in an SDF path
(Yosys writes \\dek[0].dModule for generate blocks), and it has no
INSTANCE * wildcard. So each SDF is relative to one module and is applied
to every instance of that module separately; Verilog hierarchical names
reach any scope. A cell with such a name itself gets cell_<type>.sdf
(empty INSTANCE), applied to the cell's own scope.

usage: vtube_sdf.py -c vtube_cells.v -T vtube_timing.json -n top_synth.v
                    -t top -s tb.dut_instance -o OUT_DIR
"""

import argparse
import json
import os
import re
import sys

ID = r"(?:\\\S+|[A-Za-z_][\w$]*)"
KEYWORDS = {"module", "input", "output", "inout", "wire", "reg", "assign",
            "parameter", "localparam", "initial", "always", "endmodule",
            "if", "begin", "end"}
ASYNC = {"DFF": 0, "DFFSR": 1, "DFFSR_n": 2}


def vname(name):
    """Name as it is written in a hierarchical reference."""
    return name + " " if name.startswith("\\") else name


def plain(name):
    return name[1:] if name.startswith("\\") else name


def cell_paths(cells_path):
    """{cell: [(edge, in, out)]} from the specify blocks."""
    text = open(cells_path).read()
    paths = {}
    for name, body in re.findall(r"^module (\w+)\(.*?\n(.*?)^endmodule", text, re.M | re.S):
        spec = re.search(r"specify(.*?)endspecify", body, re.S)
        paths[name] = [] if not spec else [
            (m.group(1) or "", m.group(2), m.group(3)) for m in re.finditer(
                r"\((posedge\s+)?(\w+)\s*=>\s*\(?\s*(\w+)", spec.group(1))]
    return paths


def parse_netlist(path):
    """{module: [(type, instance)]} in file order (Yosys write_verilog layout:
    one instance header "type name (" per line)."""
    mods, cur = {}, None
    head = re.compile(rf"^module ({ID})\s*\(")
    inst = re.compile(rf"^\s*({ID})\s+({ID})\s*\(\s*$")
    for line in open(path):
        if cur is None:
            m = head.match(line)
            if m:
                cur = mods.setdefault(m.group(1), [])
        elif line.startswith("endmodule"):
            cur = None
        else:
            m = inst.match(line)
            if m and m.group(1) not in KEYWORDS:
                cur.append((m.group(1), m.group(2)))
    return mods


def delay(v):
    return f"({v[0]}) ({v[1]})" if isinstance(v, list) else f"({v})"


def bad_name(inst):
    """Icarus splits SDF instance paths at '.', even escaped ones."""
    return re.search(r"[.\[\]]", inst) is not None


def cell_entry(ctype, inst, paths, timing):
    t = timing["cells"][ctype]
    io = []
    for edge, a, y in paths[ctype]:
        key = f"{edge}{a}->{y}"
        if key not in t["iopath"]:
            sys.exit(f"vtube_timing.json: {ctype} has no value for {key}")
        src = f"(posedge {a})" if edge else a
        io.append(f"(IOPATH {src} {y} {delay(t['iopath'][key])})")
    ent = (f' (CELL (CELLTYPE "{ctype}") (INSTANCE {inst})\n'
           f'  (DELAY (ABSOLUTE {" ".join(io)}))')
    for d, (su, ho) in t.get("setuphold", {}).items():
        ent += f"\n  (TIMINGCHECK (SETUPHOLD {d} (posedge C) ({su}) ({ho})))"
    return ent + ")"


def write_sdf(path, design, entries, timing):
    head = (f'(DELAYFILE\n (SDFVERSION "3.0")\n (DESIGN "{design}")\n'
            f' (PROGRAM "vtube_sdf.py")\n (DIVIDER .)\n (TIMESCALE {timing["timescale"]})')
    open(path, "w").write("\n".join([head, *entries, ")"]) + "\n")


def main():
    ap = argparse.ArgumentParser(description=__doc__.splitlines()[0])
    ap.add_argument("-c", "--cells", required=True)
    ap.add_argument("-T", "--timing", required=True)
    ap.add_argument("-n", "--netlist", required=True)
    ap.add_argument("-t", "--top", required=True)
    ap.add_argument("-s", "--scope", required=True, help="hierarchical name of the top instance")
    ap.add_argument("-o", "--out", required=True)
    args = ap.parse_args()

    paths = cell_paths(args.cells)
    timing = json.load(open(args.timing))
    mods = parse_netlist(args.netlist)
    if args.top not in mods:
        sys.exit(f"{args.netlist}: top module {args.top} not found")
    missing = sorted({t for insts in mods.values() for t, _ in insts
                      if t in paths and paths[t] and t not in timing["cells"]})
    if missing:
        sys.exit(f"{args.timing}: no timing for cells {', '.join(missing)}")
    os.makedirs(args.out, exist_ok=True)

    out = os.path.abspath(args.out)
    # Cells named like \\g_lvl[0].rel get an SDF of their own type with an
    # empty INSTANCE, applied to the cell's own scope
    sdf_of, cell_sdf = {}, {}
    for i, (mod, insts) in enumerate(mods.items()):
        cells = [(t, n) for t, n in insts if t in paths and paths[t]]
        for t, n in cells:
            if bad_name(n) and t not in cell_sdf:
                cell_sdf[t] = os.path.join(out, f"cell_{t}.sdf")
                write_sdf(cell_sdf[t], t, [cell_entry(t, "", paths, timing)], timing)
        entries = [cell_entry(t, plain(n), paths, timing) for t, n in cells if not bad_name(n)]
        if entries:
            base = re.sub(r"\W", "_", plain(mod))[-40:]
            sdf_of[mod] = os.path.join(out, f"m{i}_{base}.sdf")
            write_sdf(sdf_of[mod], plain(mod), entries, timing)

    annotate, checks, n_cells = [], [], 0

    def walk(mod, scope):
        nonlocal n_cells
        if mod in sdf_of:
            annotate.append(f'\t$sdf_annotate("{sdf_of[mod]}", {scope});')
        for t, inst in mods[mod]:
            ref = f"{scope}.{vname(inst)}"
            if t in mods:
                walk(t, ref)
            elif t in paths and paths[t]:
                n_cells += 1
                if bad_name(inst):
                    annotate.append(f'\t$sdf_annotate("{cell_sdf[t]}", {ref});')
                sh = timing["cells"][t].get("setuphold", {}).get("D")
                if sh and t in ASYNC:
                    s = f"{ref}.S" if ASYNC[t] else "1'b0"
                    r = f"{ref}.R" if ASYNC[t] else "1'b0"
                    checks.append(
                        f"vtube_setuphold #(.SETUP({sh[0]}), .HOLD({sh[1]}), .ASYNC({ASYNC[t]}))"
                        f" c{len(checks)} (.C({ref}.C), .D({ref}.D), .S({s}), .R({r}));")

    walk(args.top, args.scope)
    total = lambda f: " + ".join(f"c{i}.{f}" for i in range(len(checks))) or "0"
    sv = [f"// Generated by rtl/run/vtube_sdf.py from {os.path.basename(args.netlist)}"
          f" and {os.path.basename(args.timing)}; do not edit.",
          f"// {n_cells} cells, {len(annotate)} annotated scopes, {len(checks)} triggers checked.",
          "module vtube_sdf;", "timeunit 1ns;", "timeprecision 1ps;",
          "initial begin", *annotate, "end", "", *checks, "",
          "final", f'\t$display("VTUBE TIMING: %0d setup, %0d hold violations",',
          f"\t         {total('setup_cnt')},", f"\t         {total('hold_cnt')});",
          "endmodule"]
    open(os.path.join(args.out, "vtube_sdf.sv"), "w").write("\n".join(sv) + "\n")
    print(f"  sdf   {n_cells} cells, {len(annotate)} annotated scopes, {len(checks)} triggers checked")


if __name__ == "__main__":
    main()
