radiolok/dekatronpc/rtl/run/qn_absorb.py

"""Absorb inverters on trigger outputs into the free inverted output QN.

A tube trigger (Eccles-Jordan) has both anodes, so Q and QN cost the same.
ABC sees triggers as black boxes and builds ~Q with a NOT cell. This pass
takes the mapped Yosys JSON netlist, finds every inverter whose input is a
trigger's Q, moves its loads to the trigger's QN and drops the inverter.

Cell roles come from the liberty file: a cell with an ff()/latch() group and
a QN pin is a trigger, a cell whose only output function is "A'" is an
inverter.

usage: qn_absorb.py -l vtube_cells.lib -i in.json -o out.json
"""

import argparse
import json
import re


def lib_roles(lib_text):
    """Return (trigger cell names, inverter cell names) from the liberty text."""
    triggers, inverters = set(), set()
    for m in re.finditer(r'cell\s*\(\s*(\w+)\s*\)\s*\{', lib_text):
        name = m.group(1)
        nxt = lib_text.find('cell(', m.end())
        body = lib_text[m.end():nxt if nxt != -1 else len(lib_text)]
        if re.search(r'\b(ff|latch)\s*\(', body) and re.search(r'pin\s*\(\s*QN\s*\)', body):
            triggers.add(name)
        funcs = re.findall(r'function\s*:\s*"([^"]*)"', body)
        if funcs == ["A'"]:
            inverters.add(name)
    return triggers, inverters


def absorb(module, triggers, inverters):
    """Rewire one module in place; return the number of removed inverters."""
    cells = module.get('cells', {})
    q_of = {}      # bit -> trigger cell name whose Q drives it
    for name, cell in cells.items():
        if cell['type'] in triggers:
            q = cell['connections'].get('Q', [])
            if len(q) == 1 and isinstance(q[0], int):
                q_of[q[0]] = name

    port_bits = set()
    for port in module.get('ports', {}).values():
        port_bits.update(b for b in port['bits'] if isinstance(b, int))
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
